kunichiko/RetroCastX/hardware/adc-frontend/parts/TI_PCM1808PWR/TSSOP-14_L5.0-W4.4-H1.0-LS6.4-P0.65.step

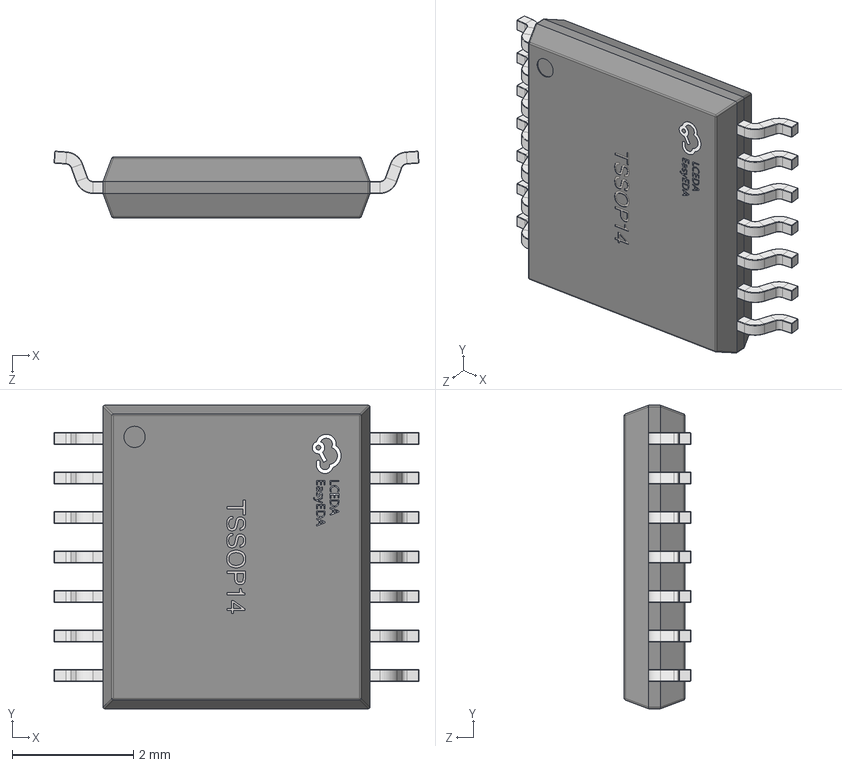
[picture p24: CAD file, 2026-07-28]
hardware/adc-frontend/parts/TI_PCM1808PWR/TSSOP-14_L5.0-W4.4-H1.0-LS6.4-P0.65.step
6.01 x 5.00 x 1.10 mm
