kunichiko/RetroCastX/hardware/adc-frontend/parts/TI_TLV70019DDCR/SOT-23-5_L2.9-W1.6-P0.95-LS2.8-BR.step

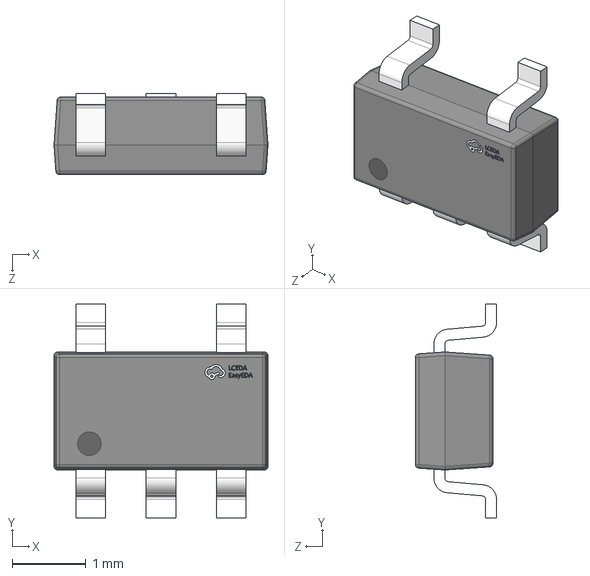
[picture p25: CAD file, 2026-07-28]
hardware/adc-frontend/parts/TI_TLV70019DDCR/SOT-23-5_L2.9-W1.6-P0.95-LS2.8-BR.step
2.90 x 2.90 x 1.10 mm
