kunichiko/RetroCastX/hardware/adc-frontend/parts/TI_TVP7002PZP/HTQFP-100_L14.0-W14.0-H1.20-P0.50-LS16.0-BL-EP6.2.step

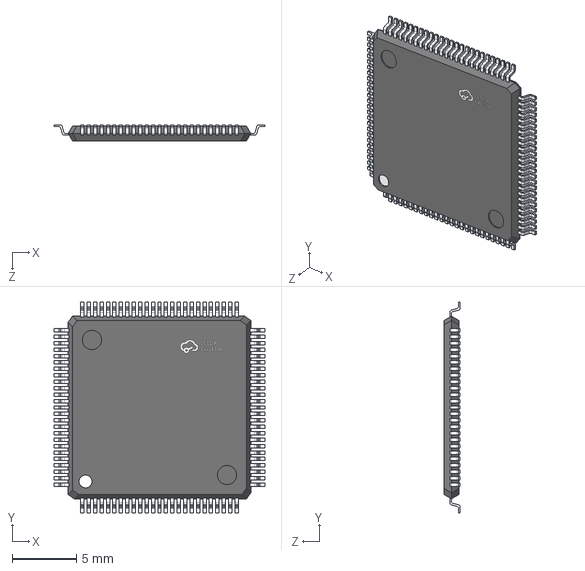
[picture p26: CAD file, 2026-07-28]
hardware/adc-frontend/parts/TI_TVP7002PZP/HTQFP-100_L14.0-W14.0-H1.20-P0.50-LS16.0-BL-EP6.2.step
16.4 x 16.4 x 1.28 mm
