kunichiko/RetroCastX/hardware/adc-frontend/parts/UNI_ROYAL_0402WGF1002TCE/R0402_L1.0-W0.5-H0.4.step

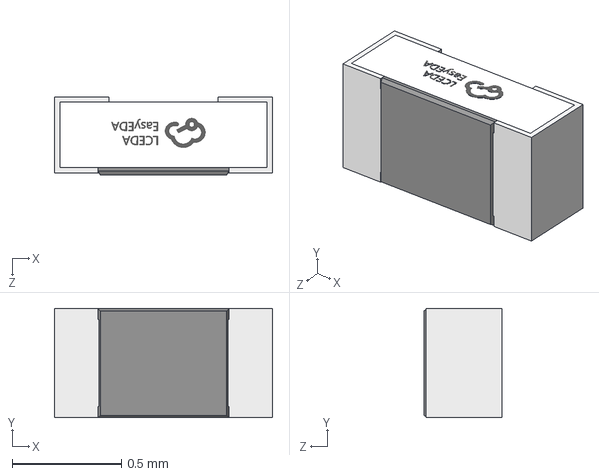
[picture p27: CAD file, 2026-07-28]
hardware/adc-frontend/parts/UNI_ROYAL_0402WGF1002TCE/R0402_L1.0-W0.5-H0.4.step
1.00 x 0.501 x 0.36 mm
