kunichiko/RetroCastX/hardware/adc-frontend/parts/UNKNOWN_PJ_327C_4A/AUDIO-SMD_L11.8-W6.0-H5.0-4P.step

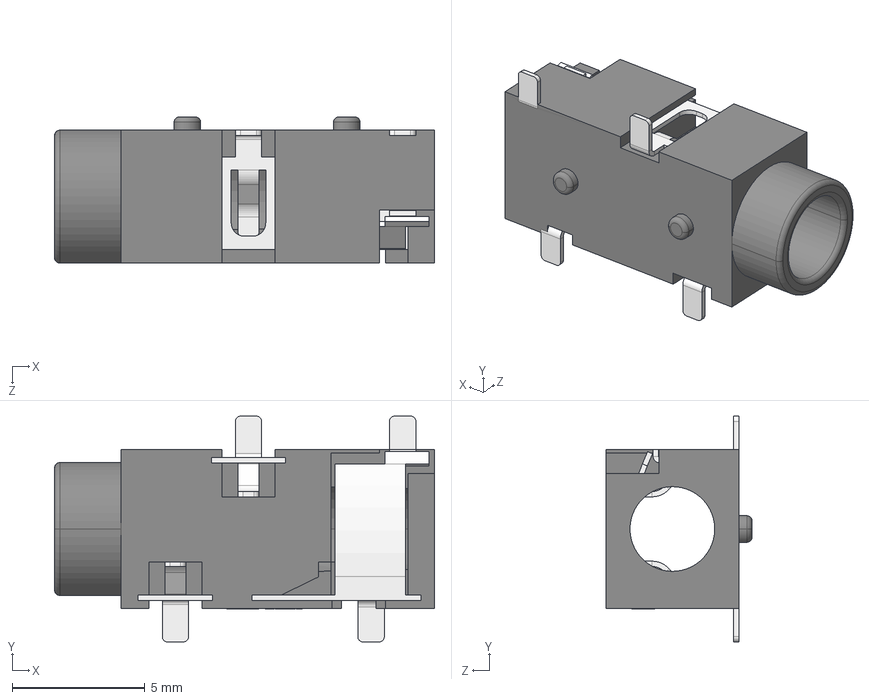
[picture p28: CAD file, 2026-07-28]
hardware/adc-frontend/parts/UNKNOWN_PJ_327C_4A/AUDIO-SMD_L11.8-W6.0-H5.0-4P.step
14.3 x 8.50 x 5.50 mm
