kunichiko/RetroCastX/hardware/adc-frontend/parts/UNKNOWN_TYPE_C_31_M_12/USB-C_SMD-TYPE-C-31-M-12.step

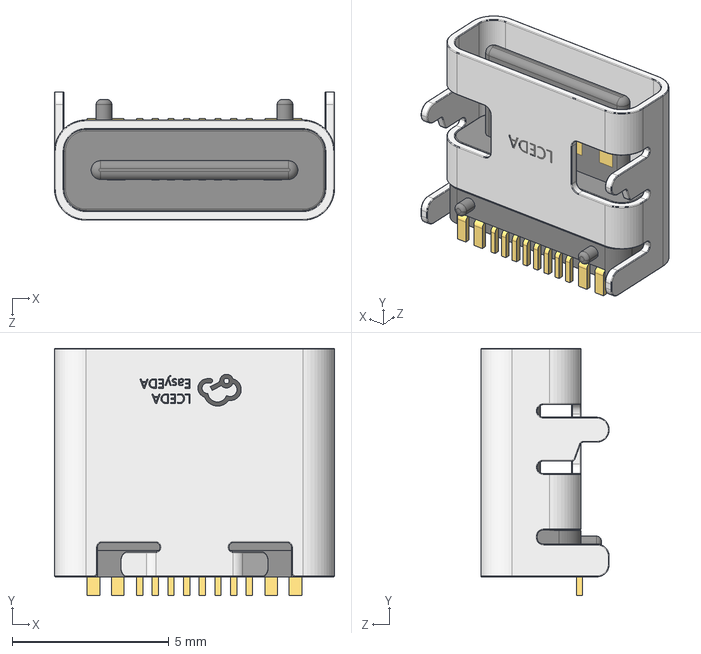
[picture p29: CAD file, 2026-07-28]
hardware/adc-frontend/parts/UNKNOWN_TYPE_C_31_M_12/USB-C_SMD-TYPE-C-31-M-12.step
8.94 x 7.90 x 4.10 mm
