kunichiko/RetroCastX/hardware/adc-frontend/parts/WCH_CH347F/QFN-28_L4.0-W4.0-P0.40-BL-EP2.7.step

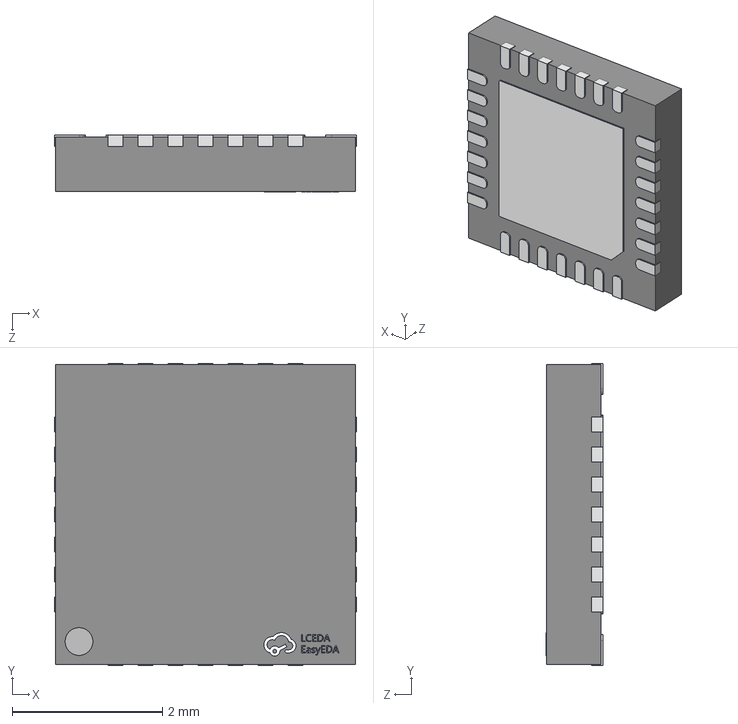
[picture p30: CAD file, 2026-08-18]
hardware/adc-frontend/parts/WCH_CH347F/QFN-28_L4.0-W4.0-P0.40-BL-EP2.7.step
4.02 x 4.02 x 0.76 mm
