kunichiko/RetroCastX/hardware/adc-frontend/parts/Worldsemi_WS2812B_2020/LED-SMD_4P-L2.0-W2.0-H0.8-TL_WS2812B-2020.step

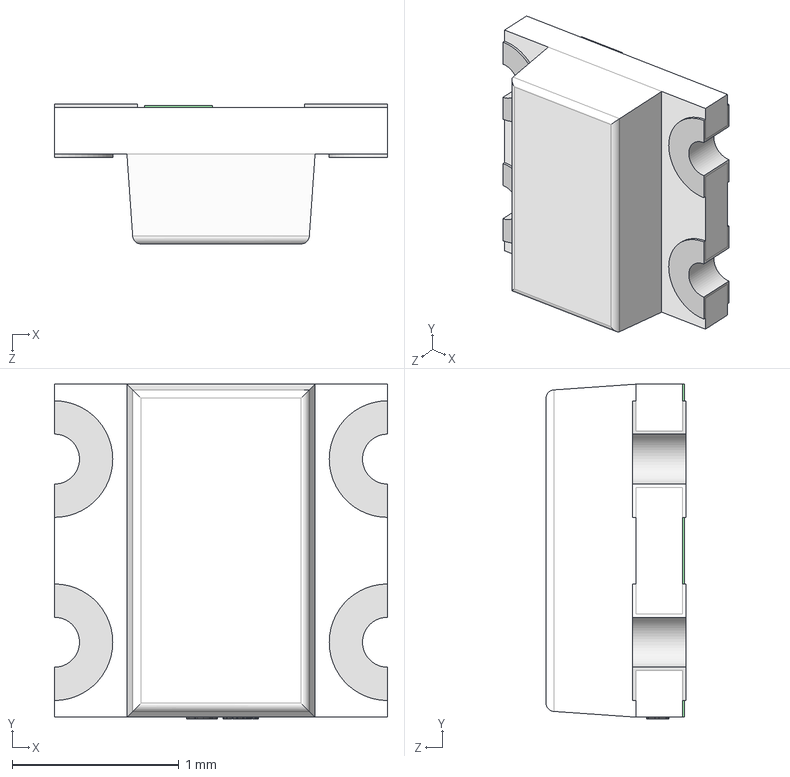
[picture p31: CAD file, 2026-08-12]
hardware/adc-frontend/parts/Worldsemi_WS2812B_2020/LED-SMD_4P-L2.0-W2.0-H0.8-TL_WS2812B-2020.step
2.00 x 2.01 x 0.84 mm
