kunichiko/RetroCastX/hardware/adc-frontend/parts/XFCN_BH254V_10P/IDC-TH_10P-P2.54-V-R2-C5-S2.54.STEP

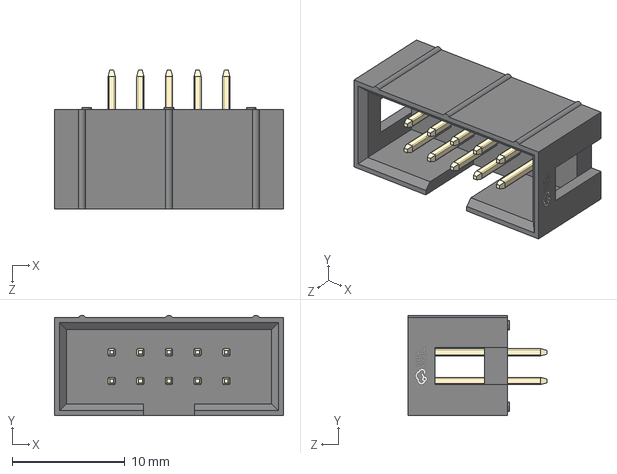
[picture p32: CAD file, 2026-09-25]
hardware/adc-frontend/parts/XFCN_BH254V_10P/IDC-TH_10P-P2.54-V-R2-C5-S2.54.STEP
20.3 x 8.89 x 12.3 mm
