kunichiko/RetroCastX/hardware/adc-frontend/parts/YAGEO_CC1812KKX7RDBB472/C1812_L4.5-W3.2-H2.6.step

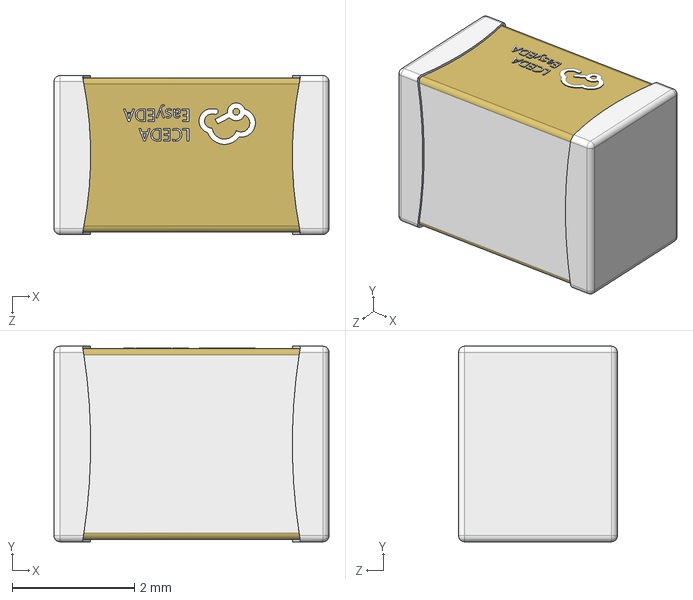
[picture p33: CAD file, 2026-07-28]
hardware/adc-frontend/parts/YAGEO_CC1812KKX7RDBB472/C1812_L4.5-W3.2-H2.6.step
4.50 x 3.20 x 2.60 mm
