kunichiko/RetroCastX/hardware/adc-frontend/parts/YXC_OT322527MJBA4SL/OSC-SMD_4P-L3.2-W2.5-CJ13-320001210A20.step

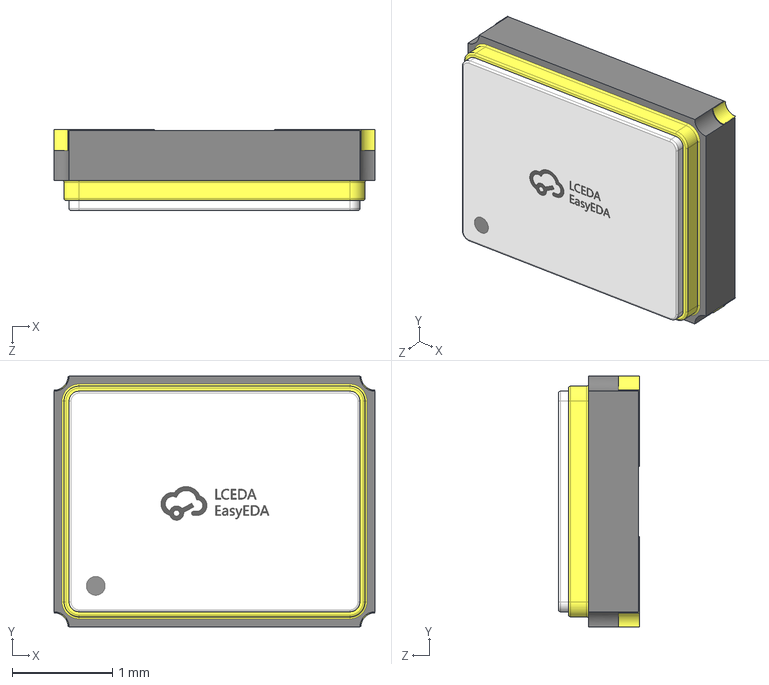
[picture p34: CAD file, 2026-07-28]
hardware/adc-frontend/parts/YXC_OT322527MJBA4SL/OSC-SMD_4P-L3.2-W2.5-CJ13-320001210A20.step
3.20 x 2.50 x 0.811 mm
