kunichiko/RetroCastX/hardware/adc-frontend/parts/YXC_X32258MSB4SI/CRYSTAL-SMD_4P-L3.2-W2.5-BL.step

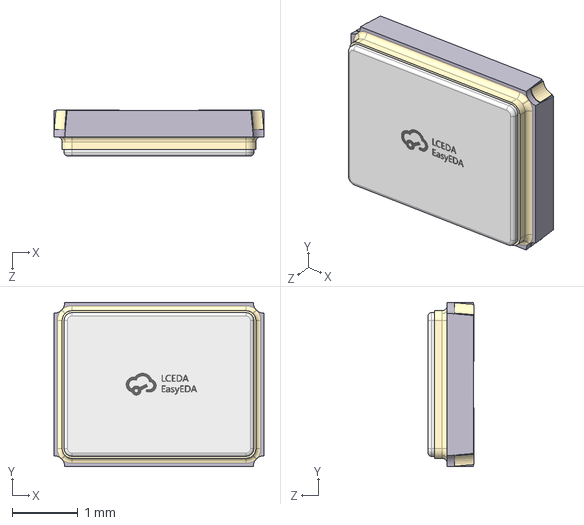
[picture p35: CAD file, 2026-08-03]
hardware/adc-frontend/parts/YXC_X32258MSB4SI/CRYSTAL-SMD_4P-L3.2-W2.5-BL.step
3.20 x 2.50 x 0.701 mm
