kunichiko/RetroCastX/hardware/console-frontend/parts/ROHM_EMZT6_8ET2R/EMT6_L1.6-W1.2-P0.50-LS1.6-BL.step

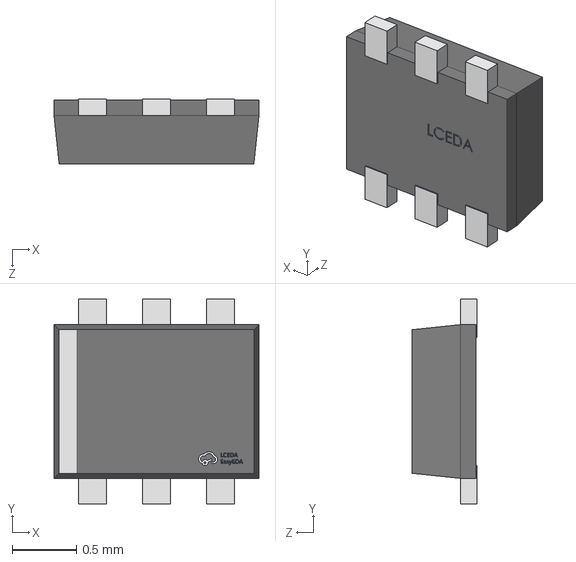
[picture p36: CAD file, 2026-07-28]
hardware/console-frontend/parts/ROHM_EMZT6_8ET2R/EMT6_L1.6-W1.2-P0.50-LS1.6-BL.step
1.60 x 1.60 x 0.511 mm
