kunichiko/RetroCastX/hardware/console-frontend/parts/SAMSUNG_CL21A106KAYNNNE/C0805_L2.0-W1.3-H1.3.step

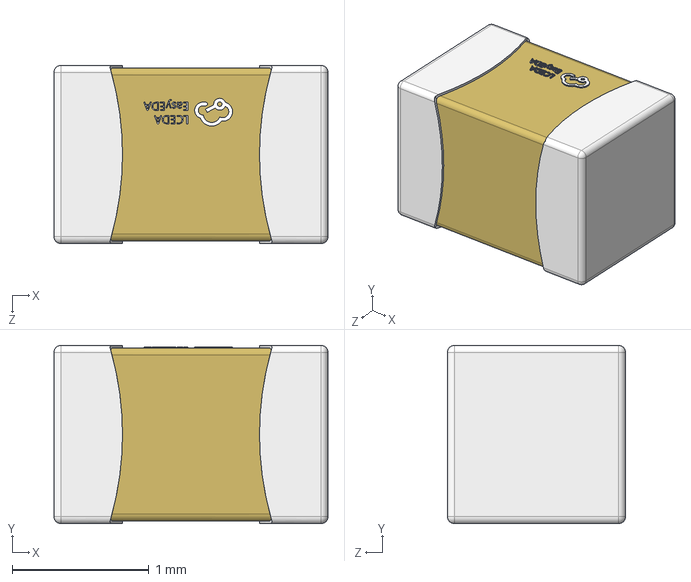
[picture p37: CAD file, 2026-07-28]
hardware/console-frontend/parts/SAMSUNG_CL21A106KAYNNNE/C0805_L2.0-W1.3-H1.3.step
2.00 x 1.30 x 1.30 mm
