kunichiko/RetroCastX/hardware/console-frontend/parts/TI_TS5A23159DGSR/VSSOP-10_L3.0-W3.0-H1.1-LS4.9-P0.50.step

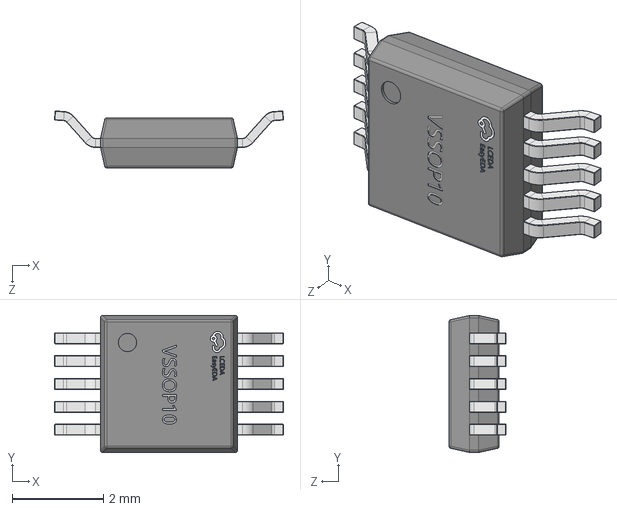
[picture p38: CAD file, 2026-09-25]
hardware/console-frontend/parts/TI_TS5A23159DGSR/VSSOP-10_L3.0-W3.0-H1.1-LS4.9-P0.50.step
5.01 x 3.00 x 1.25 mm
