kunichiko/RetroCastX/hardware/console-frontend/parts/UNI_ROYAL_0603WAF1002T5E/R0603.STEP

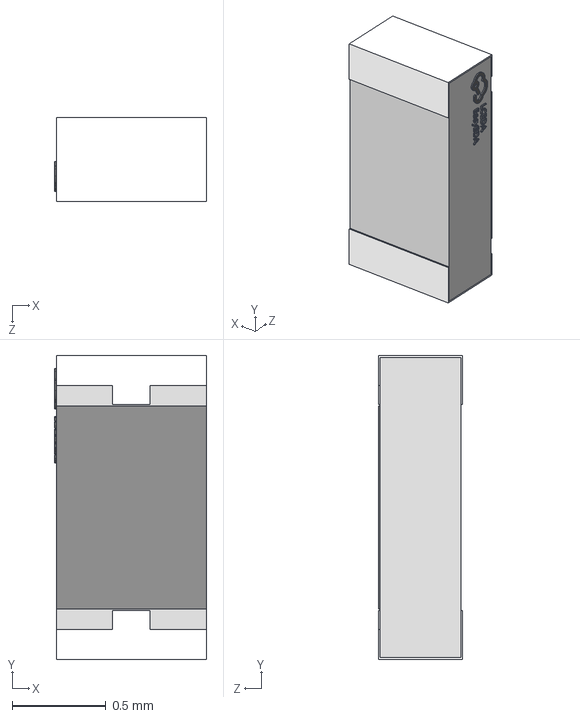
[picture p39: CAD file, 2026-09-25]
hardware/console-frontend/parts/UNI_ROYAL_0603WAF1002T5E/R0603.STEP
0.81 x 1.62 x 0.45 mm
