kunichiko/RetroCastX/hardware/console-frontend/parts/XINGLIGHT_XL_2020RGBC_2812B/6.STEP

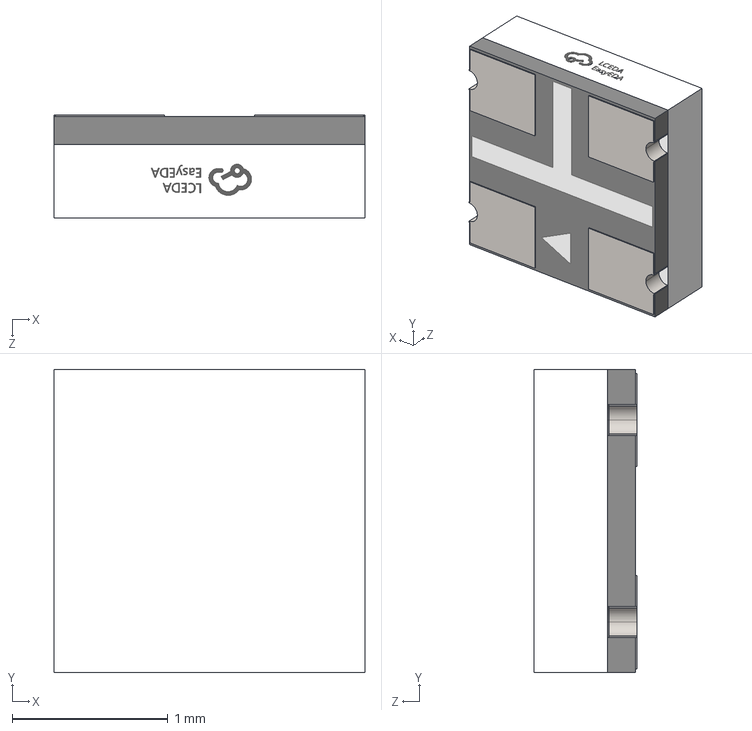
[picture p40: CAD file, 2026-08-19]
hardware/console-frontend/parts/XINGLIGHT_XL_2020RGBC_2812B/6.STEP
2.00 x 1.95 x 0.66 mm
