kunichiko/RetroCastX/hardware/console-frontend/parts/YAGEO_CC0603KRX7R9BB104/C0603_L1.6-W0.8-H0.8.step

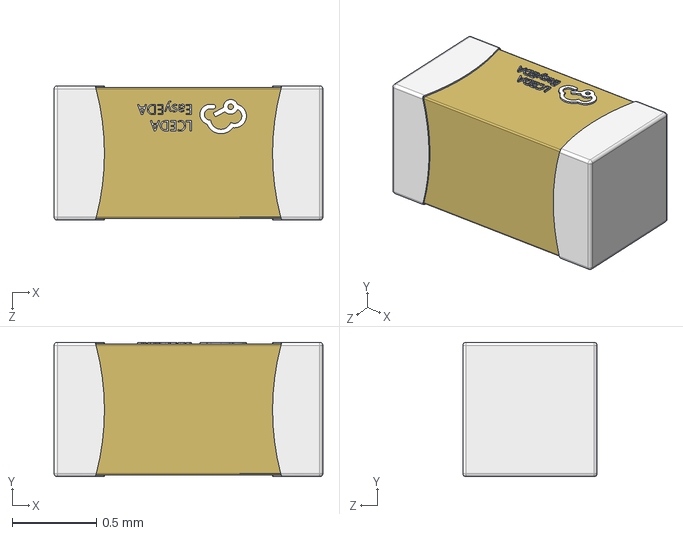
[picture p41: CAD file, 2026-07-28]
hardware/console-frontend/parts/YAGEO_CC0603KRX7R9BB104/C0603_L1.6-W0.8-H0.8.step
1.60 x 0.8 x 0.8 mm
