kunichiko/RetroCastX/client/src/main.rs

//! RetroCastX viewer (scaffold).
//!
//! egui/eframe(wgpuバックエンド)でフレームを表示する。v0.1はegui標準の
//! テクスチャAPIで毎フレーム全面アップロード(512x512なら余裕)。
//! パレット吸着・CRTシェーダ・VRR present制御は、後段でwgpuの
//! paint callback(egui_wgpu::Callback)へ移行して実装する。
//!
//! Usage:
//!   cargo run --release -- [--board IP] [--mac AA:BB:..] [--port 34600] [--no-subscribe]
//!
//! --mimicx-probe は MimicX へのキー転送経路(CoreMIDI)だけを確かめて終了する。
//!
//! --mac は購読対象ボードのMACを指名する(複数ボードLANで必須。省略時は
//! ワイルドカード=全ボード、単一ボードLAN専用)。
//!
//! 既定ではSUBSCRIBEを**各NICのサブネット宛**にブロードキャストし、ボードの
//! ストリームを自分に向ける。限定ブロードキャスト(255.255.255.255)は使わない:
//! あれは既定経路に載るので、VPN接続中は送信自体が失敗する
//! (receiver.rs の broadcast_targets 参照)。sender_sim相手なら --no-subscribe
//! でよい(sender_simはSUBSCRIBEを無視して--dest宛に送るため)。

// Windows: コンソール窓を出さずに起動する。これが無いと、Explorerから起動しても
// 先に真っ黒なコンソールが開いてからUIが出る(通常のGUIアプリの見た目にならない)。
// 代わりにコンソールから起動したときは main の先頭で親のコンソールへ繋ぎ直すので、
// --headless の出力はこれまでどおり見える。
#![windows_subsystem = "windows"]

mod appicon;
mod assembler;
mod awake;
mod audio;
mod bezel;
mod claim;
mod cleanout;
mod fullscreen;
mod keytap;
mod netcheck;
mod ntsc;
mod profiles;
mod remote_input;
mod render;
mod protocol;
mod receiver;
mod settings;
mod theme;
mod toast;

use std::sync::atomic::Ordering;
use std::sync::Arc;

use eframe::egui;

/// コンソールから起動されたときだけ、その親コンソールへ標準出力を戻す。
/// Explorer から起動したときは親が無いので何も起きない(コンソールは出ない)。
/// **最初の出力より前に呼ぶこと** — 標準ハンドルは初回使用時に決まるため。
#[cfg(windows)]
fn attach_parent_console() {
    use windows_sys::Win32::System::Console::{AttachConsole, ATTACH_PARENT_PROCESS};
    unsafe { AttachConsole(ATTACH_PARENT_PROCESS) };
}

#[cfg(not(windows))]
fn attach_parent_console() {}

/// 伝送形式の表示名。数値のままだと 0=888 / 1=555 が直感に反するので名前で出す
fn pixfmt_name(f: u8) -> &'static str {
    match f {
        protocol::PIXFMT_RGB888 => "RGB888 (3B/px)",
        protocol::PIXFMT_RGB555 => "RGB555 (2B/px)",
        protocol::PIXFMT_RGB565 => "RGB565 (2B/px)",
        protocol::PIXFMT_YC8 => "YC8 (2B/px)",
        _ => "unknown",
    }
}

fn main() -> eframe::Result {
    attach_parent_console();
    let mut port = protocol::DEFAULT_PORT;
    let mut subscribe_to = Some("255.255.255.255".to_string());
    let mut headless_secs: Option<u64> = None;
    // --headless のときに完成フレームをPPMへ落とす。絵を目で見られない環境で
    // 「組立・復調までは合っているのか」を切り分けるため
    let mut dump_frame: Option<String> = None;
    // 連続Nフレームを番号付きで落とす(フレーム間で変わる現象の追跡用)
    let mut dump_seq: Option<usize> = None;
    let mut no_vsync = false;
    let mut fullscreen_mode = false;
    let mut rotate: u32 = u32::MAX;   // 未指定なら設定ファイルの値を使う
    let mut target_mac: Option<[u8; 6]> = None;
    let mut decay = 0.8f32;
    // インターレース時の減衰率。既定1.0=減衰しない。
    // インターレースは「毎フレーム半分の行が来ない」のが正常なので、パケットロス用の
    // 減衰をそのまま掛けると面全体がフィールドレートでちらつく。CRTの残光を模すなら
    // 少し減衰させたい人もいるので設定にしてある。
    let mut interlace_decay = 1.0f32;
    // ★**ウィンドウ番号はアプリが配る。** 1プロセスで複数のウィンドウを開く
    //   ので、プロセスごとにロックを取る必要はもう無い。0番が主ウィンドウ。
    let slot_id: u32 = 0;

    // 保存済み設定を読み、CLI引数があればそれで上書きする(その回だけ有効)
    let mut cfg = settings::Settings::load_slot(slot_id);
    eprintln!("settings: {}", settings::Settings::path_for_slot(slot_id).display());
    let mut audio = receiver::AudioOpts::default();
    audio.source = cfg.audio_source;
    // 起動時から設定のデバイスで開く(既定デバイスで鳴り始めるのを防ぐ)
    audio.device = cfg.audio_device.clone();
    let mut bind = String::from("0.0.0.0");
    let mut args = std::env::args().skip(1);
    while let Some(a) = args.next() {
        match a.as_str() {
            "--board" => subscribe_to = Some(args.next().expect("--board needs an IP")),
            "--mac" => target_mac = Some(parse_mac(&args.next().expect("--mac needs AA:BB:.."))),
            "--port" => port = args.next().expect("--port needs a value").parse().unwrap(),
            "--no-subscribe" => subscribe_to = None,
            // 受信/送信ソケットを1つのNICに縛る。**VPN下でも通常は不要**
            // (宛先がNICごとのサブネット宛なので既定経路を参照しない。
            //  receiver.rs の broadcast_targets 参照)。NICを1つに絞りたいときだけ。
            "--bind" => bind = args.next().expect("--bind needs an IP (e.g. 192.168.11.24)"),
            // ドット復元(1タップ逆フィルタ)の係数 a を 0.0..0.9 で指定。
            // 0 で無効。設定ファイルの値を一時的に上書きする(A/B検証用)。
            "--dot-restore" => {
                let a: f32 = args.next().expect("--dot-restore needs a (e.g. 0.36)")
                    .parse().expect("--dot-restore は 0.0〜0.9 の数値");
                cfg.dot_a_milli = (a.clamp(0.0, 0.9) * 1000.0).round() as u32;
            }
            "--dump-seq" => {
                dump_seq = Some(args.next().expect("--dump-seq needs a count")
                                .parse().unwrap())
            }
            "--dump-frame" => {
                dump_frame = Some(args.next().expect("--dump-frame needs a path"))
            }
            "--headless" => {
                headless_secs = Some(args.next().expect("--headless needs seconds").parse().unwrap())
            }
            // VRR実験用: presentをvsyncから切り離す(wgpu AutoNoVsync)。
            // VRR対応パネルなら「フレームが来たときに出す」に近づく第一歩
            "--no-vsync" => no_vsync = true,
            // 低遅延フルスクリーン(専用presentスレッド+Immediate、ソース駆動present)
            "--fullscreen" => fullscreen_mode = true,
            // 画面回転(縦画面のゲーム用)。0/90/180/270 度、時計回り
            "--rotate" => {
                let v: u32 = args.next().expect("--rotate needs 0|90|180|270").parse().unwrap();
                rotate = match v {
                    0 => 0, 90 => 1, 180 => 2, 270 => 3,
                    _ => panic!("--rotate は 0/90/180/270 のいずれか"),
                };
            }
            // 欠損ライン減衰率(1.0=前フレーム保持のまま, 0.8=毎フレーム80%へ暗転して消える)
            "--interlace-decay" => {
                interlace_decay = args.next()
                    .expect("--interlace-decay needs a value (e.g. 1.0)").parse().unwrap()
            }
            "--decay" => {
                decay = args.next().expect("--decay needs a value (e.g. 0.8)").parse().unwrap()
            }
            // 音声: 再生するsource(0=RGB端子音声, 1=LINE入力, 2=S/PDIF)
            "--audio" => {
                audio.source =
                    Some(args.next().expect("--audio needs 0|1|2").parse().unwrap());
                cfg.audio_source = audio.source;
            }
            // MimicX への経路だけを確かめて終了する(GUIは起動しない)。
            // 「キーが効かない」ときに、宛先が無いのか送れているのかを切り分ける
            "--mimicx-probe" => std::process::exit(!remote_input::probe() as i32),
            // 受け取った物理キーを stderr へ出す。「そのキーがアプリに届いて
            // いないのか、届いているが転送していないのか」の切り分け用
            // NIC受信バッファーの確認だけして終了する(GUIは起動しない)。
            // 実機での切り分け用。IPはボードのアドレス(経路の判定に使う)
            "--netcheck" => {
                let ip = args.next().expect("--netcheck needs the board IP");
                let b = netcheck::probe(&ip);
                println!("board {ip} への経路の NIC: {b:?}");
                match &b {
                    netcheck::Buffers::Known { adapter, value } => {
                        println!("  アダプタ      : {adapter}");
                        println!("  ReceiveBuffers: {value} (推奨 {})", netcheck::RECOMMENDED);
                        if b.should_warn() {
                            println!("  → 小さすぎます:");
                            println!("     {}", netcheck::fix_command(Some(adapter)));
                        } else {
                            println!("  → 足りています");
                        }
                    }
                    netcheck::Buffers::Unsupported => {
                        println!("  このドライバは *ReceiveBuffers を公開していません(判定不能)");
                    }
                    netcheck::Buffers::Unknown => {
                        println!("  調べられませんでした(経路が引けない/レジストリが読めない)");
                    }
                }
                std::process::exit(0);
            }
            "--log-keys" => {
                remote_input::LOG_KEYS.store(true, Ordering::Relaxed);
            }
            "--no-audio" => {
                audio.source = None;
                cfg.audio_source = None;
            }
            // 音量[%]。保存値より優先(その回だけ)
            "--volume" => {
                let pct: f32 = args.next().expect("--volume needs 0..150").parse().unwrap();
                cfg.volume = (pct / 100.0).clamp(0.0, 1.5);
            }
            // 音声バッファ[ms]。小さいほど低遅延だが枯渇(音切れ)しやすい
            "--audio-buffer" => {
                audio.prebuffer_ms =
                    args.next().expect("--audio-buffer needs ms").parse().unwrap();
                audio.max_ms = audio.prebuffer_ms * 3;
            }
            other => {
                eprintln!("unknown arg: {other}");
                std::process::exit(2);
            }
        }
    }

    if let Some(secs) = headless_secs {
        return run_headless(port, bind, subscribe_to, target_mac, secs, decay, interlace_decay,
                            audio, dump_frame, dump_seq, cfg.dot_a_milli);
    }
    if fullscreen_mode {
        let rot = if rotate == u32::MAX { cfg.rotate } else { rotate };
        let p = render::Params {
            rotate: rot,
            tube: cfg.tube_aspect,
            filter: cfg.filter,
            window: cfg.window,
            time_based: cfg.tube_time_based,
            h_size: 1.0, h_pos: 0.0, v_size: 1.0, v_pos: 0.0,
            ..Default::default()
        };
        fullscreen::run(port, bind, subscribe_to, target_mac, decay, interlace_decay, audio, p); // 戻らない
    }

    let mut wgpu_options = eframe::egui_wgpu::WgpuConfiguration::default();
    if no_vsync {
        wgpu_options.surface.present_mode = eframe::wgpu::PresentMode::AutoNoVsync;
        wgpu_options.surface.desired_maximum_frame_latency = Some(1); // 低遅延優先
    }

    let options = eframe::NativeOptions {
        viewport: {
            // アイコンは実行時に設定しないとタスクバー/タイトルバーに出ない
            // (exeへの埋め込みはExplorerのファイル用。appicon.rs 参照)
            let mut vp = egui::ViewportBuilder::default()
                .with_inner_size([cfg.window_w, cfg.window_h])
                .with_title(if slot_id == 0 {
                    "RetroCast X".to_string()
                } else {
                    // ★**番号を出す。** 3つ並べたときに、どのウィンドウの設定を
                    //   触っているのか分からなくなる
                    format!("RetroCast X #{}", slot_id)
                });
            // ★**位置も戻す。** 大きさだけでは並びが戻らない(3画面筐体では
            //   横に並べた配置そのものが設定)。
            if let (Some(x), Some(y)) = (cfg.window_x, cfg.window_y) {
                vp = vp.with_position([x, y]);
            }
            if let Some(icon) = appicon::egui_icon() {
                vp = vp.with_icon(icon);
            }
            vp
        },
        wgpu_options,
        ..Default::default()
    };
    eframe::run_native(
        "RetroCast X",
        options,
        Box::new(move |cc| {
            // アイコン由来の配色を先に当てる(ウィジェットが作られる前)
            theme::apply(&cc.egui_ctx);
            install_cjk_font(&cc.egui_ctx);
            // ★**映像テクスチャの置き場はアプリに1つ。** セッションごとに
            //   insert すると型で索く辞書なので上書きになり、**先に開いた
            //   ウィンドウの映像が消える**。中身はウィンドウ番号で分ける。
            if let Some(rs) = cc.wgpu_render_state.as_ref() {
                // 描画先の色空間を出す。映像テクスチャはこれに合わせて選ぶ
                // (render::video_tex_format が sRGB 性を揃える)。
                eprintln!("render target format: {:?}", rs.target_format);
                rs.renderer
                    .write()
                    .callback_resources
                    .insert(render::Blits::default());
            }
            let mut app = App {
                sessions: vec![Session::new(
                    slot_id, &cc.egui_ctx, cc.wgpu_render_state.clone(), port,
                    subscribe_to, target_mac, bind.clone(), no_vsync,
                    decay, interlace_decay, audio, cfg.clone(),
                )],
                port,
                bind: bind.clone(),
                no_vsync,
                decay,
                interlace_decay,
                awake: awake::KeepAwake::new(),
            };
            app.restore_windows(&cc.egui_ctx, cc.wgpu_render_state.clone());
            Ok(Box::new(app))
        }),
    )
}


/// CJKを含むシステムフォントをeguiへ追加する。
/// 出力デバイス名はOS由来で日本語を含むことがあり、egui既定フォントにはCJKの
/// グリフが無いため豆腐(□)になる。フォントは同梱せず、実行環境のものを使う。
fn install_cjk_font(ctx: &egui::Context) {
    // 単一フォント(.ttf/.otf)のみ。.ttc はコレクションでab_glyphが扱えない
    const CANDIDATES: &[&str] = &[
        // macOS
        "/System/Library/Fonts/Supplemental/Arial Unicode.ttf",
        "/Library/Fonts/Arial Unicode.ttf",
        // Linux (Noto/VLGothic)
        "/usr/share/fonts/opentype/noto/NotoSansCJK-Regular.ttc",
        "/usr/share/fonts/truetype/noto/NotoSansCJK-Regular.ttf",
        "/usr/share/fonts/truetype/vlgothic/VL-Gothic-Regular.ttf",
        // Windows
        "C:/Windows/Fonts/meiryo.ttc",
        "C:/Windows/Fonts/msgothic.ttc",
        "C:/Windows/Fonts/YuGothR.ttc",
    ];
    for path in CANDIDATES {
        let Ok(bytes) = std::fs::read(path) else { continue };
        let mut fonts = egui::FontDefinitions::default();
        fonts.font_data.insert(
            "cjk".to_owned(),
            std::sync::Arc::new(egui::FontData::from_owned(bytes)),
        );
        // 既定フォントの後ろに足す(ASCIIは既定の見た目を保ち、CJKだけ補完)
        for family in [egui::FontFamily::Proportional, egui::FontFamily::Monospace] {
            fonts.families.entry(family).or_default().push("cjk".to_owned());
        }
        ctx.set_fonts(fonts);
        return;
    }
    eprintln!("font: CJK対応フォントが見つからないため日本語が豆腐になります");
}

/// "AA:BB:CC:DD:EE:FF" → [u8; 6](区切りは ':' or '-')。
fn parse_mac(s: &str) -> [u8; 6] {
    let parts: Vec<&str> = s.split([':', '-']).collect();
    assert_eq!(parts.len(), 6, "MAC must have 6 octets: {s}");
    let mut mac = [0u8; 6];
    for (i, p) in parts.iter().enumerate() {
        mac[i] = u8::from_str_radix(p, 16).expect("bad MAC octet");
    }
    mac
}

/// GUIなしで受信パイプラインだけ動かし、毎秒統計を出力する(検証・CI用)。
fn run_headless(
    port: u16,
    bind: String,
    subscribe_to: Option<String>,
    target_mac: Option<[u8; 6]>,
    secs: u64,
    decay: f32,
    interlace_decay: f32,
    audio: receiver::AudioOpts,
    dump_frame: Option<String>,
    dump_seq: Option<usize>,
    dot_a_milli: u32,
) -> eframe::Result {
    let shared = Arc::new(receiver::Shared::default());
    shared.dot_a_milli.store(dot_a_milli, std::sync::atomic::Ordering::Relaxed);
    receiver::spawn(
        receiver::Config { port, bind: bind.clone(), subscribe_to, target_mac, decay, interlace_decay, audio },
        shared.clone(),
        || {},
    )
    .expect("UDP bind failed");
    for _ in 0..secs {
        std::thread::sleep(std::time::Duration::from_secs(1));
        let s = shared.stats.lock().unwrap().clone();
        let mode = shared.mode.lock().unwrap().clone();
        let dims = mode
            .map(|m| format!("{}x{}", m.hactive, m.vactive))
            .unwrap_or_else(|| "no mode".into());
        println!(
            "{dims}  {:.1} fps  {:.1} Mbps  frames={} pkts={} lost={} qdrop={} orphan={}",
            s.fps, s.mbps, s.frames, s.packets, s.lost_packets, s.queue_drops,
            s.orphan_lines
        );
        // 音声。**枯渇の切り分け表示を GUI を開かずに読めるように。**
        if let Some(a) = shared.audio.lock().unwrap().clone() {
            let ms = |us: u64| us as f64 / 1000.0;
            let rate = a.device_rate.load(Ordering::Relaxed).max(1);
            let last = a.last_underrun_us.load(Ordering::Relaxed);
            println!(
                "   audio: buffered {} ms  pkts {}  underruns {}  gap max {:.1} ms  cb max {} f{}",
                a.buffered.load(Ordering::Relaxed) * 1000 / rate,
                a.packets.load(Ordering::Relaxed),
                a.underruns.load(Ordering::Relaxed),
                ms(a.arrival_gap_max_us.load(Ordering::Relaxed)),
                a.cb_frames_max.load(Ordering::Relaxed),
                if last > 0 {
                    format!("  last {:.0}s前 無着 {:.0} ms",
                            ms(a.now_us() - last) / 1000.0,
                            ms(a.last_underrun_gap_us.load(Ordering::Relaxed)))
                } else { String::new() });
        }
        // 連続フレームを番号付きで落とす。**フレームごとに入れ替わる縞**のような
        // 「1枚では分からない」現象を追うのに要る(実際に必要になった)。
        if let (Some(path), Some(n)) = (dump_frame.as_ref(), dump_seq) {
            let mut last = 0u64;
            let mut got = 0usize;
            let t0 = std::time::Instant::now();
            while got < n && t0.elapsed() < std::time::Duration::from_secs(10) {
                let g = shared.frame_gen.load(Ordering::Acquire);
                if g == last {
                    std::thread::sleep(std::time::Duration::from_micros(500));
                    continue;
                }
                last = g;
                if let Some(f) = shared.frame.lock().unwrap().as_ref() {
                    let mut out = format!("P6\n{} {}\n255\n", f.width, f.height)
                        .into_bytes();
                    for px in f.rgba.chunks_exact(4) {
                        out.extend_from_slice(&px[..3]);
                    }
                    let _ = std::fs::write(format!("{path}.{got:04}.ppm"), &out);
                    got += 1;
                }
            }
            println!("   dump: {path}.0000..{:04}.ppm ({}枚)", got.saturating_sub(1), got);
            return Ok(());
        }
        // 完成フレームをそのままPPMへ落とす。**GUIを開かずに絵を確かめる唯一の手段。**
        // 「絵が出ない」を追うとき、組立・復調までは正しいのか、描画側なのかを
        // ここで切り分けられる(実際にこれで切り分けた)。
        if let Some(path) = dump_frame.as_ref() {
            if let Some(f) = shared.frame.lock().unwrap().as_ref() {
                let mut out = format!("P6\n{} {}\n255\n", f.width, f.height).into_bytes();
                for px in f.rgba.chunks_exact(4) {
                    out.extend_from_slice(&px[..3]);
                }
                if std::fs::write(path, &out).is_ok() {
                    let n = f.rgba.chunks_exact(4).filter(|p| p[0] | p[1] | p[2] != 0).count();
                    println!("   dump: {path} ({}x{}) 非黒画素 {}/{} = {:.1}%",
                             f.width, f.height, n, f.width * f.height,
                             n as f32 * 100.0 / (f.width * f.height) as f32);
                }
            }
        }
        // NTSC復調の状態。**GUIを開かずに確認できるようにしておく。**
        // この環境は画面収録の権限が無く、絵で確かめられないので数値で出す
        if s.ntsc_comb_step > 0 {
            println!("   NTSC復調: {}行ロック  コム間隔{}  位相差{:.0}°(180°が正常)",
                     s.ntsc_locked, s.ntsc_comb_step, s.ntsc_phase_deg);
            if s.ntsc_svideo {
                println!("   S端子(赤chのバーストで判定): コムは使わない/輝度は素通し");
            } else {
                println!("   3次元コム: {}行  動きと判定 {:.1}%  1フレーム前との位相ズレ {:.1}°  \
                          TBC {:.3}サンプル",
                         s.ntsc_lines_3d, 100.0 * s.ntsc_motion_frac,
                         s.ntsc_phase_drift_deg, s.ntsc_tbc_rms);
            }
        } else if s.ntsc_mono {
            println!("   NTSC: 白黒(バーストなし) 黒レベルのみ校正");
        }
        // 生産側がUIを待った時間。**GUIのときだけパケットが落ちる**を切り分ける
        if s.publish_wait_max_ms > 0.05 {
            println!("   フレーム差し替えのUI待ち: 合計{:.1}ms 最大{:.1}ms /区間",
                     s.publish_wait_ms, s.publish_wait_max_ms);
        }
        println!("   インタレース判定(測定): {}  未充填の行 {}",
                 if s.interlace_measured { "1フィールドずつ来ている(太らせ停止・減衰なし)" }
                 else { "プログレッシブ扱い(太らせ有効)" },
                 s.unfilled_rows);
        // 何も来ないときに、どの種別が届いていないかを出す。
        // ブロードキャストだけ届いてユニキャストが届かない、などが分かる
        if s.frames == 0 {
            let k: Vec<String> = ["LINE", "AUDIO", "MODE", "INFO", "CONFIG", "other"]
                .iter()
                .zip(shared.kind_counts.iter())
                .map(|(n, c)| format!("{n}={}", c.load(Ordering::Relaxed)))
                .collect();
            println!("   受信種別: {}", k.join(" "));
        }
    }
    let s = shared.stats.lock().unwrap().clone();
    shared.stop.store(true, Ordering::Relaxed);
    if s.frames == 0 {
        eprintln!("FAIL: no frames received");
        std::process::exit(1);
    }
    println!("OK: {} frames, {} lost packets", s.frames, s.lost_packets);
    Ok(())
}

/// **新しいフレームが画面に出る間隔**の計測(vsync量子化の検出用)。
///
/// ★**描画にかかった時間ではない。** `refresh_texture` は新フレームが無ければ
///   即 return するので、ここに来るのは「中身が変わったpaint」だけ。だから
///   ボードが59.8fps送っているのにここが54.9Hzなら、**8%のフレームが表示されずに
///   置き換わっている**という意味になる。以前は "paint" と表示していて
///   「描画に18msかかっている」と読めてしまった。
///
/// present完了時刻そのものはwgpu経由では取れないため、この間隔を代理指標にする
/// (FIFOではスワップチェーンのバックプレッシャでvsync周期に量子化される)。
/// CPU側で実際にかかった時間は `cpu_summary` に別に出す。
struct PaceMeter {
    last_paint: Option<std::time::Instant>,
    intervals_ms: std::collections::VecDeque<f32>,
    last_log: std::time::Instant,
    summary: String,
    /// ★**間隔と処理時間は別物。** 上の intervals_ms は「新フレームが画面に出る
    ///   間隔」で、FIFOのvsync待ちを含む。こちらはCPU側で実際にかかった時間で、
    ///   間隔が伸びたときに「我々が遅いのか、待たされているのか」を分ける。
    ui_ms: std::collections::VecDeque<f32>,
    upload_ms: std::collections::VecDeque<f32>,
    cpu_summary: String,
    /// ★**描画そのものの回数。** 新フレームの有無に関わらず数える。
    ///   これが60Hz出ているのに新フレーム間隔が54Hzなら「描画は回っているが
    ///   フレームが置き換わっている」、こちらも54Hzなら「描画が回っていない」。
    ui_calls: u32,
    ui_rate_hz: f32,
    ui_since: std::time::Instant,
    /// 表示できた新フレームのレート[Hz]。受信レートと並べて出す
    pub new_frame_hz: f32,
}

impl PaceMeter {
    fn new() -> Self {
        Self {
            last_paint: None,
            intervals_ms: std::collections::VecDeque::with_capacity(256),
            last_log: std::time::Instant::now(),
            summary: String::new(),
            ui_ms: std::collections::VecDeque::with_capacity(256),
            upload_ms: std::collections::VecDeque::with_capacity(256),
            cpu_summary: String::new(),
            ui_calls: 0,
            ui_rate_hz: 0.0,
            ui_since: std::time::Instant::now(),
            new_frame_hz: 0.0,
        }
    }

    fn note_upload(&mut self, d: std::time::Duration) {
        if self.upload_ms.len() >= 256 { self.upload_ms.pop_front(); }
        self.upload_ms.push_back(d.as_secs_f32() * 1000.0);
    }

    fn note_ui(&mut self, d: std::time::Duration) {
        if self.ui_ms.len() >= 256 { self.ui_ms.pop_front(); }
        self.ui_ms.push_back(d.as_secs_f32() * 1000.0);
        self.ui_calls += 1;
        let el = self.ui_since.elapsed().as_secs_f32();
        if el >= 1.0 {
            self.ui_rate_hz = self.ui_calls as f32 / el;
            self.ui_calls = 0;
            self.ui_since = std::time::Instant::now();
        }
        let f = |v: &std::collections::VecDeque<f32>| -> (f32, f32) {
            if v.is_empty() { return (0.0, 0.0); }
            let n = v.len() as f32;
            let mean = v.iter().sum::<f32>() / n;
            let max = v.iter().cloned().fold(0.0f32, f32::max);
            (mean, max)
        };
        let (um, ux) = f(&self.ui_ms);
        let (tm, tx) = f(&self.upload_ms);
        self.cpu_summary = format!(
            "描画 {:.1}Hz / CPU: UI {um:.2}ms(最大{ux:.2}) 転送 {tm:.2}ms(最大{tx:.2})",
            self.ui_rate_hz);
    }

    /// 新フレームを受け取った(= 中身が変わるpaint)
    fn on_new_frame(&mut self) {
        let now = std::time::Instant::now();
        if let Some(prev) = self.last_paint {
            let ms = prev.elapsed().as_secs_f32() * 1000.0;
            if self.intervals_ms.len() >= 256 {
                self.intervals_ms.pop_front();
            }
            self.intervals_ms.push_back(ms);
        }
        self.last_paint = Some(now);
        if self.last_log.elapsed().as_secs_f32() >= 1.0 && !self.intervals_ms.is_empty() {
            let n = self.intervals_ms.len() as f32;
            let mean = self.intervals_ms.iter().sum::<f32>() / n;
            let var = self.intervals_ms.iter().map(|x| (x - mean) * (x - mean)).sum::<f32>() / n;
            self.new_frame_hz = 1000.0 / mean;
            self.summary = format!(
                "新フレーム間隔 {:.2}ms σ{:.2} → {:.2}Hz",
                mean,
                var.sqrt(),
                self.new_frame_hz
            );
            // ★CPU側の内訳も一緒に出す。パネルはマウスを止めないと読めないので、
            //   「マウスを動かしている最中」の数字はログでしか取れない
            //   (実機で「ウィンドウ上でマウスを動かすとレートが下がる」を追うのに要った)
            eprintln!("pace: {} | {}", self.summary, self.cpu_summary);
            self.last_log = std::time::Instant::now();
        }
    }
}

/// 実測タイミングから「まともな映像が来ているか」を判定する。
/// 無信号だとTVPのH-PLLがロックを失い、DATACLKが低速で自走してADCが浮いた入力の
/// ノイズを拾うため、砂嵐が表示される。実測値が現実的な範囲を外れたら無信号とみなす。
fn signal_is_valid(m: &protocol::Mode) -> bool {
    let fh_hz = m.hfreq_mhz_x1000 as f64 / 1000.0;
    // 15kHz系(≒15.98k)〜31kHz系(≒31.5k)を含む余裕のある範囲
    (12_000.0..80_000.0).contains(&fh_hz)
        && (100..1500).contains(&m.vtotal)
        && m.dotclk_hz > 5_000_000
}

/// pll_divide と位相を自動で決める処理の進行状態。
///
/// 原理は host/python/retrocastx/pll_tune.py の autotune と同じ。要点だけ:
/// 「近傍で鋭さが最大の点」を探す方法は有理倍に騙される(1.5倍は位相ロックする
/// 有理比なので本物の局所ピークに見える)。そこで、まず上限まで意図的に過剰
/// サンプルしてスペクトル占有率から倍率を割り出し、そこから8の倍数で±7%だけ
/// 局所探索して詰める。最後に位相を振る。
///
/// ## 簡易(Quick)とフル(Full)
///
/// 上のフルスキャンは**探索範囲が広すぎる**。プロファイルを選んでいるなら
/// pll_divide は「水晶÷分周 ÷ fH が整数」を満たす数点しか取り得ないので、
/// その数点だけを見ればよい(例: X68000の31.5kHzなら htotal 1104/736/552/368)。
///
/// **機種固有の分岐は一切書かない。** 候補は `profiles::scan_candidates` が
/// プロファイルの水晶/分周表と fH から作るので、機種を足すときは
/// `profiles.rs` の表を書けばここは触らなくてよい。
///
/// ### 何で1:1を判定するか — 位相感度
///
/// 使うのは**位相感度**。1ドット=1サンプルなら、位相を半ドット動かせば全サンプルが
/// ドットの中央から境目へ移るので鮮鋭度が大きく落ちる。過剰サンプルだと、位相を
/// 動かしても「一部のサンプルが境目に来る」状態が入れ替わるだけなので変化が小さい。
/// **同じ pll_divide での比**なので、絵の内容にも入力の帯域にも依存しない。
///
/// ★**スペクトル占有率で1:1を判定してはいけない。** 一度これで実装して外した。
///   占有率は「1:1ならスペクトルがNyquistまで埋まる」を前提にするが、入力の
///   アナログ帯域がドットレートに対して足りていない機種ではその前提が崩れる。
///   X68000の768x512(34.776MHz)がまさにそれで、1ドットが白の64%までしか
///   立たない。正解の1104で測っても占有率は0.7程度しか出ないので、
///   `1104 × 0.7 = 773` から「736だ」と誤って1段降りた(実機で発生)。
///   1.0倍と1.5倍を占有率で見分けるのは、この機種では原理的に無理。
///
///   占有率にも使い道はあって、`est = 設定値 × 占有率 = 真のhtotal × 帯域率`
///   なので **真の htotal の下限**になる(帯域率 ≤ 1 だから)。下限としてなら
///   信用できるので、枝刈りと最後のフォールバックにだけ使う。
///
/// ### 選び方
///
/// **全候補の位相感度を測ってから、いちばん感度が強い(最悪÷最良がいちばん小さい)
/// 点を採る。** どれもしきい値を下回らなければ判別できていないので、いちばん
/// 大きい候補に倒す。大きい側は整数倍の過剰サンプルで眠くなるだけだが、小さい側は
/// ドットを飛ばして絵が壊れる。非対称なので迷ったら上。この経路に来るのはたいてい、
/// そのモードが1:1にできない(TVPの下限12MHzで整数倍を強いられている)場合。
///
/// ★**「感度が立った最初の候補で止まり、降りる先を占有率で枝刈りする」形は
///   実機で外した**(2026-09-04、31.5kHz の 512x512 で 1104 のまま動かなかった。
///   降下が一度も起きていなかった)。枝刈りの根拠は「est = 設定値 × 占有率 は
///   真の htotal の下限」だったが成り立っていなかった。真値 736 を 1104 で測った
///   ときの占有率の理論上の上限は 736/1104 = 0.667 なのに実測は 0.716 出た
///   (99%エネルギーの裾がノイズを拾う)。下限として使えない量で枝刈りしていた
///   ので、正解が候補から消えていた。
///
///   判定材料の側は十分な差が出ていた。実測(31.5kHz 512x512、真値736):
///
/// ```text
///     pll 1104  最良 160.25  最悪 156.58  → 98%   1.5倍オーバーサンプル
///     pll  736  最良 377.11  最悪 200.92  → 53%   ★1:1
///     pll  552  最良 406.15  最悪 351.23  → 87%
/// ```
///
///   **鮮鋭度の絶対値では選べない**ことにも注意(552 の最良 406 は 736 の 377 より
///   大きい)。見るのは同じ設定内での比。`quick_pick` の試験でこの値を固定してある。
///
/// ### 結果には内訳を出す
///
/// 「pll_div 1104 / 位相 0 で完了(要確認: 最悪の位相は 98%)」だけでは、候補を1つ
/// しか測っていないのか、全部測って選べなかったのかが分からない。上の不具合の
/// 切り分けに手間をかけたので、候補ごとの位相感度を必ず並べる。
enum AutoPhase {
    /// 上限まで過剰サンプルして占有率を測る
    Oversample,
    /// 8の倍数で局所探索(pll候補, 結果)
    Sweep { cands: Vec<u32>, i: usize, best: (u32, f32), med: Vec<f32> },
    /// 簡易: 候補を htotal の**大きい順**に、位相を8点振って「1:1かどうか」を見る。
    /// `k` は位相の点番号(位相 = k*4)
    QuickProbe { i: usize, k: u8, best: (u8, f32), worst: f32 },
    /// 位相を粗く振る
    PhaseCoarse { i: u8, best: (u8, f32), all: Vec<f32> },
    /// 位相を1刻みで詰める
    PhaseFine { list: Vec<u8>, i: usize, best: (u8, f32) },
}

/// スキャンの種類。**探索空間の広さだけが違う**。測り方(占有率と鮮鋭度)も
/// 位相の詰め方も同じ。
enum AutoMode {
    /// 簡易: プロファイルの水晶/分周が許すモードだけを見る。
    Quick {
        /// 測る順番。htotal の**降順**で、設定値(pll_divide)の重複は除いてある。
        /// 設定値が同じ点は測っても区別できないので1回で済ませる
        ladder: Vec<profiles::ScanPoint>,
        /// 候補ごとの (最良位相, その鮮鋭度, 最悪の鮮鋭度)。測った順に積む。
        /// 全候補を測り終えたら、位相感度(最悪÷最良)がいちばん小さい点を採る
        probes: Vec<(u8, f32, f32)>,
    },
    /// フル: プロファイルを使わず、絵のスペクトルだけから範囲を割り出して
    /// 8刻みで舐める。プロファイルに無いモードや、未知の機種で使う
    Full,
}

struct AutoTune {
    mode: AutoMode,
    phase: AutoPhase,
    /// この時刻まではボードの反映待ち
    wait_until: std::time::Instant,
    /// 待ち開始時点の測定回数。これより進んだ測定だけを採用する
    base_n: u64,
    /// 経過表示
    note: String,
    /// 最悪の位相(参考表示用)
    worst: f32,
    /// 半分にして測り直した回数
    attempt: u8,
    /// 簡易スキャンで選んだ点のオーバーサンプル倍率。
    /// **1より大きいなら位相感度が弱いのが正常**なので、最後の判定に使う
    over: u32,
    /// 簡易スキャンの判定の内訳(例 "1104→98% 736→53% 552→87%")。
    /// **結果だけだと外したときに切り分けられない。** 実機で1度そうなった
    report: String,
}

/// 位相を振っても鮮鋭度が変わらない(最悪÷最良がこれより大きい)なら、まだ
/// 1ドットが複数サンプルに広がっている = 過剰サンプル、と判定する。
///
/// 0.85 はフルスキャン側で実機から決めた値(15kHz帯で 0.95 = ほぼ変わらない、が
/// 過剰サンプルの実測)。簡易スキャンが1段降りるかどうかもこの1つの数字で決まる。
const PHASE_SENSITIVE: f32 = 0.85;

/// NTSCの1ライン[µs]と1フレームのライン数。管面の窓を時間とライン数で書くのに使う
const NTSC_LINE_US: f32 = 63.556;
const NTSC_LINES: f32 = 525.0;

/// コンポジット/S端子(YC8)の管面を `mon_bands` に置くキー。実在しない帯域番号
/// (帯域は kHz の値なので重ならない)。設定ファイルには `mon.1000` で残る。
const MON_KEY_NTSC: u32 = 1000;

/// コンポジット/S端子の管面の初期値 [H幅, H位置, V幅, V位置]。
///
/// ★**ビデオデッキの HDMI 出力と同じ範囲を映す**(2026-10-09 実測、白黒の格子
///   パターン。中央の点と格子を目印に、こちらの受信データと同じ物差しで比べた)。
///     横: 9.95〜60.87µs(= ntsc::ACTIVE_US)。中心 35.41µs が中央の点に一致
///     縦: 480ライン。フレームの 35.6〜515.6 行目(中央の点は 272.5 行目)
///   以前は15kHz帯の管面(RGB用)を共用していて、帰線区間の黒い余白まで映り、
///   中心も右へずれていた。
///   位置は「周期の中心からのずれ」で、絵を動かす向きに符号を取る(render.rs)。
const MON_NTSC: [f32; 4] = {
    let (h0, h1) = ntsc::ACTIVE_US;
    let (v0, v1) = (35.6, 515.6);
    [
        (h1 - h0) / NTSC_LINE_US,
        0.5 - (h0 + h1) * 0.5 / NTSC_LINE_US,
        (v1 - v0) / NTSC_LINES,
        0.5 - (v0 + v1) * 0.5 / NTSC_LINES,
    ]
};

/// 全候補を測り終えたあと、どれを採るかを決める。返り値は (添字, その位相感度)。
///
/// 位相感度(最悪÷最良)がいちばん小さい = 1ドットが1サンプルに載っている点を採る。
/// どれも `PHASE_SENSITIVE` を下回らなければ判別できていないので、**いちばん
/// 大きい候補(添字0)** に倒す。大きい側は整数倍の過剰サンプルで眠くなるだけだが、
/// 小さい側はドットを飛ばして絵が壊れる。非対称なので迷ったら上。
///
/// `probes` は (最良位相, 最良の鮮鋭度, 最悪の鮮鋭度) を候補の順(htotal降順)に。
/// 「画に合わせる」ときの目標のウィンドウ内寸。動かす必要が無ければ `None`。
///
/// `tex` は**画の実寸ではなく、いま画面に出ている(レターボックス後の)大きさ**。
/// だから `tex + 外側の余白` は必ず現在の内寸**以下**になる ─ つまりこの操作は
/// 「余白を削って縮める」。1回なら意図どおりだが、**繰り返すと縮み続ける**。
///
/// ★**丸め程度の差では動かさない。** 比が一致すれば余白は0になって収束する
///   はずだが、点と画素の丸めやパネル幅の増減で毎回わずかに残る。Windows の
///   DPI 拡大では1回あたりの目減りが大きく、**同期がふらつくたびに合わせ直して
///   窓が消えていった**(2026-09-10 実機。Macでは目減りが小さく気付かなかった)。
/// 要求した内寸と実寸のずれをどこまで許すか[point]。
/// 端数の丸めは通すが、タイトルバーや枠のぶん(数十point)は通さない。
const FIT_TOLERANCE: f32 = 4.0;

/// 要求してから答え合わせをするまでの猶予。ウィンドウマネージャの応答と
/// アニメーションを待つぶん。
const FIT_VERDICT_AFTER: std::time::Duration = std::time::Duration::from_millis(700);

/// 直前の内寸要求が通ったかの判定。
#[derive(Debug, PartialEq, Eq)]
enum FitVerdict {
    /// まだ分からない(猶予内)。要求を保持して次のフレームで見直す
    Pending,
    /// 要求どおりになった
    Honored,
    /// 猶予を過ぎても要求と違う。以後この環境では自動サイズ合わせをしない
    Ignored,
}

fn fit_verdict(
    requested: egui::Vec2,
    actual: egui::Vec2,
    elapsed: std::time::Duration,
) -> FitVerdict {
    if (actual - requested).length() <= FIT_TOLERANCE {
        FitVerdict::Honored
    } else if elapsed >= FIT_VERDICT_AFTER {
        FitVerdict::Ignored
    } else {
        FitVerdict::Pending
    }
}

fn fit_target(
    window: egui::Vec2,
    avail: egui::Vec2,
    tex: egui::Vec2,
    monitor: Option<egui::Vec2>,
) -> Option<egui::Vec2> {
    let chrome = window - avail;
    let mut want = tex + chrome;
    // 画面より大きくしない(はみ出すと操作できなくなる)
    if let Some(mon) = monitor {
        want = want.min(mon * 0.95);
    }
    let delta = (want - window).abs();
    (delta.x > 3.0 || delta.y > 3.0).then_some(want)
}

fn quick_pick(probes: &[(u8, f32, f32)]) -> (usize, f32) {
    let rel_of = |p: &(u8, f32, f32)| if p.1 > 0.0 { p.2 / p.1 } else { 1.0 };
    let (mut j, mut min_rel) = (0usize, f32::MAX);
    for (idx, p) in probes.iter().enumerate() {
        let r = rel_of(p);
        if r < min_rel {
            (j, min_rel) = (idx, r);
        }
    }
    if min_rel > PHASE_SENSITIVE {
        j = 0;
    }
    (j, min_rel)
}

const AUTO_PLL_MIN: u32 = 200;
const AUTO_PLL_MAX: u32 = 2304;

struct Session {
    shared: Arc<receiver::Shared>,
    /// 再生中の音声source(UI表示用)
    audio_source: Option<u8>,
    /// 出力デバイス一覧(起動時に列挙。再列挙ボタンで更新)
    audio_devices: Vec<String>,
    /// UIで選択中のデバイス。None は「システム既定」
    audio_device_sel: Option<String>,
    /// 音量(0.0..1.5、1.0=原音)。ミュート時も値は保持してトグルで戻せるようにする
    audio_volume: f32,
    audio_muted: bool,
    /// 設定の保存(スライダー操作中に毎フレーム書かないよう、変更後に少し待って書く)
    settings_dirty: Option<std::time::Instant>,
    /// 画枠パラメータ(ボードへCONFIGで送る値)。モードごとに最適値が違うので、
    /// ビルドし直さずにここで追い込む。
    tune_vbp: i32,
    tune_hs_offset: i32,
    tune_pll_divide: i32,
    /// TVPのアナログ映像帯域。0=最大 / 15=最小(約95MHz)
    tune_video_bw: u8,
    /// 1ラインまるごと送る(非黒範囲の最適化を切る)。
    /// 全黒行の直後の数行で範囲判定が壊れて行が欠ける不具合の回避策。
    tune_full_line: bool,
    /// フレーム間引き。0=毎フレーム / 1=2フレームに1回 …
    /// 受信が追いつかない機械での保険。音声は間引かない
    tune_frame_skip: u8,
    /// 復調を止めて生のYを見る(切り分け用。設定には保存しない)
    raw_view: bool,
    /// 表示するフィールド 0=織り込み / 1=偶数 / 2=奇数(同上)
    field_view: u8,
    /// 見た目の調整(彩度・明るさ・コントラスト・色相)。設定に保存する
    adjust: ntsc::Adjust,
    /// 管面の幾何に使う vtotal(スロット数)を平滑した値。**整数のまま使わない。**
    ///
    /// ★インターレースは 262.5 ライン/フィールドなので、ボードが測る vtotal は
    ///   262 と 263 を交互に返すのが正常。瞬間値を幾何に使うと縦のスケールが
    ///   フレームごとに 0.38% 変わり、絵が上下に震える(実機で「横線の縦位置が
    ///   フレームごとに動いて二重線に見える」形で出た。片フィールド表示でも
    ///   残ったので、織り込みではなく幾何側だと切り分けられた)。
    /// (描画中に更新するので Cell。paint_tube を &mut self にすると波及が大きい)
    vtotal_smooth: std::cell::Cell<f32>,
    /// 前回 vtotal_smooth を更新した時刻。平滑の時定数を**時間で**決めるのに使う。
    /// フレーム数で決めると、MODEが1秒に1〜2回しか来ないのに60Hzで回るせいで
    /// 収束しきってしまい、平均されずに追従する(実機で縦が数ピクセル伸び縮みした)
    vtotal_last_t: std::cell::Cell<Option<std::time::Instant>>,
    /// 平滑をリセットする判定用。モードが変わったら追従を待たずに飛ばす
    vtotal_mode_id: std::cell::Cell<u16>,
    /// 直近で入力設定を書き込んだソース(ラベル, 件数, 自動か)。パネルの確認表示用。
    /// 一時通知(スナックバー)
    toasts: toast::Toasts,
    /// 伝送形式が映像ソースと食い違ったので `input_regs` を自動で書いたか。
    /// **食い違いが解消したら false に戻す**ので、ボードの電源を入れ直すたびに
    /// 1回だけ書き直す。書いてから MODE が変わるまでの間に何度も書かないための掛け金。
    input_regs_autowritten: bool,
    /// 映像ソースのプロファイル名(profiles::PROFILES の key)。空文字は「自動」。
    /// pll_divide を絵の内容ではなく fH とドットクロック候補から決めるのに使う
    source_profile: String,
    tune_phase: u8,
    /// 送信したがまだボードの応答で確認できていない値(key → (値, 送信時刻))。
    /// 応答が返るまでは自分の値を優先し、押した瞬間に元へ戻って見えるのを防ぐ。
    tune_pending: std::collections::HashMap<u16, (u32, std::time::Instant)>,
    /// 次に現在値を問い合わせる時刻。全キーが揃うまで繰り返す
    tune_get_at: Option<std::time::Instant>,
    /// 「ボード」欄の編集中テキスト。**ボードの値を直接いじらない** ─
    /// 1文字打つたびにCONFIGが飛ぶと、打ちかけの名前が基板に載る。
    /// None は「まだ編集を始めていない(ボードの値をそのまま出す)」。
    ident_name_edit: Option<String>,
    ident_ip_edit: Option<String>,
    /// 個体設定を最後に問い合わせた時刻。ボードを選び直したら取り直す
    ident_get_at: Option<std::time::Instant>,
    /// いま個体設定を読み込んであるボードのMAC。切り替えを検知する
    ident_for: Option<[u8; 6]>,
    /// 最後に見たボード側の値。**これが変わったら編集欄を捨てる。**
    /// SETの応答が返るとボードの値が変わるので、編集欄に古いテキストが
    /// 残っていると「適用/戻す」が出たままになり、押すと古い名前が飛ぶ。
    ident_name_seen: Option<String>,
    ident_ip_seen: Option<u32>,
    /// ボードの現在値を取り込み済みか。起動時に1回だけ合わせる
    tune_synced: bool,
    /// TVPの細ゲイン(レジスタ08h/09h/0Ah)。ゲイン = 1 + N/256。
    /// **基板ごとに違う**ので手で詰められるようにする。値はボードから読み戻す。
    tune_gain_r: i32,
    /// SOGスライス閾値(レジスタ10h bit[7:3]、5bit)。**同期をどの高さで切るか。**
    /// 低すぎると暗い映像を同期と誤認して垂直検出が壊れる。映像源ごとに違うので
    /// 絵を見ながら振れるようにする。値はボードから読み戻す。
    tune_sog_thresh: i32,
    /// 同期処理制御(レジスタ22h)。bit0=VS Bypass / bit1=VS Select。
    /// 既定 0x08 は VSOUT をハーフライン積算器に作らせる(525ライン前提)。
    tune_sync_ctl2: i32,
    /// SOGOUTのLow期間を「垂直ブロードパルス」とみなす閾値[pixクロック]。
    /// 捕捉側はこれで垂直区間を見つけ、その瞬間のライン内位相からフィールド極性を出す。
    tune_sog_vth: i32,
    /// フィールド極性の向き(0/1)。経路によって符号が変わる。
    tune_field_invert: i32,
    /// 生同期(TTL)の位相をフィールド極性に使わないか。0=使う / 1=使わない。
    /// 生同期を繋がない方式では 1(浮いた同期入力の自己発振で raw_ok が誤って立つ)。
    tune_no_raw_phase: i32,
    /// lines/frame などの読み出し専用ステータスを次に問い合わせる時刻。
    /// これらは**変化する値**なので、tune 値と違って繰り返し取り直す。
    stat_get_at: Option<std::time::Instant>,
    /// 伝送形式(0x36)。0=RGB888 / 1=RGB555 / 3=YC8。
    /// ゲートウェアは実行時に切り替えるので、他の tune 値と同じ扱いにする
    tune_pixfmt: i32,
    tune_gain_g: i32,
    tune_gain_b: i32,
    /// 現在のウィンドウ内寸(保存用)
    window_size: egui::Vec2,
    /// ウィンドウ位置(復元用)。並びを戻すのに要る
    window_pos: Option<egui::Pos2>,
    /// このセッションのビューポートを一度でも出したか。
    ///
    /// ★**位置と大きさは最初の1回しか指定しない。** 毎フレーム
    ///   `ViewportBuilder` に載せると、eframe が差分を見て毎回
    ///   「ここへ動かせ」を送る。ユーザがドラッグしても次のフレームで
    ///   引き戻され、**掴んでも動かせないウィンドウ**になる。
    viewport_shown: bool,
    /// 最後に心拍(=設定の保存)を打った時刻
    settings_beat: Option<std::time::Instant>,
    /// アプリへの要求: 新しいウィンドウを開きたい(次のフレームで App が拾う)。
    /// 指定があればそのボードを選んだ状態で開く。
    want_new_window: Option<Option<[u8; 6]>>,
    /// このウィンドウの番号。設定ファイル・GPUテクスチャ・ビューポートIDの鍵。
    ///
    /// ★**空いているうち最小を割り当てる。** 0,1,2 を開いて1を閉じ、また開けば
    ///   1が返るので、そのウィンドウの設定(画枠・音量・接続先・位置)が
    ///   そのまま復元される。
    slot_id: u32,
    /// 接続先の指定(自動 / 特定の基板 / つながない)
    board_sel: settings::BoardSel,
    /// 中央の描画領域と画のサイズ。ウィンドウを等倍に合わせるのに使う
    last_avail: egui::Vec2,
    last_tex: egui::Vec2,
    /// 起動後に一度だけ自動で等倍に合わせたか
    did_autofit: bool,
    /// 次のフレームでウィンドウを等倍に合わせる
    want_fit: bool,
    /// 切り替わりかけているモードと、それを最初に見た時刻。
    ///
    /// ★**すぐには追従しない。** モードは fh/vtotal/htotal の**測定値**から
    ///   作るので、同期が一瞬乱れるだけで別のモードに見える。そのたびに
    ///   切り出しと回転をリセットしていたため、**絵が飛んでいた**
    ///   (2026-09-10。ボード側で vactive が 568→372 に飛ぶ現象を実測)。
    pending_mode: Option<(String, std::time::Instant)>,
    /// 最後にウィンドウを合わせたときの「絵の大きさを決める要素」。
    ///
    /// ★**モードキーとは別に持つ。** モードキーは fh/htotal/vtotal で作るので、
    ///   映像が乱れて同期がふらつくと**絵の大きさは変わっていないのに**変化する。
    ///   それでウィンドウを合わせ直していたため、乱れるたびに窓が縮んでいった。
    fitted_sig: Option<(u16, u16, u32, [u32; 4])>,
    /// 直前に OS へ要求した内寸。次のフレームで実際の内寸と突き合わせる。
    ///
    /// ★**要求どおりにならない環境がある。** `fit_target` は
    ///   「余白 = 内寸 - 描画領域」を測って、その余白ぶんを足した内寸を要求する。
    ///   要求した内寸と、次に測れる内寸がずれる環境では、そのずれが毎回余白に
    ///   化けて積もり、合わせ直すたびにウィンドウが縮んでいく(Windows で発生。
    ///   macOS では出なかった)。**ずれを見つけたら合わせるのをやめる。**
    ///   合っていない環境で反復しても正しい大きさには辿り着けないし、
    ///   ユーザーが手で決めた大きさを奪い続ける方がずっと害が大きい。
    fit_requested: Option<(egui::Vec2, std::time::Instant)>,
    /// 要求が通らないと分かった環境では、自動サイズ合わせを止める
    fit_disabled: bool,
    /// 受信中フレームの寸法(GPUテクスチャは callback_resources 側が持つ)
    frame_size: (u32, u32),
    render_state: Option<eframe::egui_wgpu::RenderState>,
    seen_gen: u64,
    /// 画面回転 0/1/2/3 = 時計回りに 0/90/180/270 度
    rotate: u32,
    /// 表示する切り出し範囲[画素]。w か h が 0 なら全体を表示
    crop: [u32; 4],
    /// 管面の縦横比(幅/高さ)。0 なら有効映像の比のまま
    tube_aspect: f32,
    /// 右の操作パネルを表示するか。隠すと映像(と枠)だけになる。
    /// 隠すと戻すUIが無くなるので、Tabキーで必ず戻せるようにしてある。
    show_panel: bool,
    /// モニタの枠(ベゼル)の名前。空文字は枠なし
    bezel: String,
    /// 枠を一時的に隠す。プルダウンの選択(bezel)は保ったまま切り替えたいので、
    /// 「なし」を選ぶのとは別に持つ。B キーで切り替える。
    bezel_off: bool,
    /// 配信用クリーン出力ウィンドウ(OBS のウィンドウキャプチャ用)
    clean_open: bool,
    clean_size: [f32; 2],
    clean_undecorated: bool,
    /// 調査用の数値と細かい設定を出すか
    show_advanced: bool,
    /// 音声入力を映像ソースに追従させるか
    audio_auto: bool,
    /// S/PDIF を主系統へ混ぜるか
    spdif_mix: bool,
    /// S/PDIF の音量(主系統とは独立)
    spdif_volume: f32,
    /// 実際にウィンドウへ適用済みの値。設定変更を1回だけ送るために持つ
    clean_size_applied: [f32; 2],
    clean_undecorated_applied: bool,
    /// 枠のテクスチャ。ラスタライズした幅と一緒に持ち、幅が変わったら作り直す
    bezel_tex: Option<(egui::TextureHandle, u32)>,
    /// 補間 0=ニアレスト 1=バイリニア 2=sharp-bilinear
    filter: u32,
    /// ドット復元の係数 a ×1000。0=無効。詳細は assembler の dot_a_milli
    dot_a_milli: u32,
    /// インターレース時の残光(1.0=減衰しない)。設定に保存する
    interlace_decay: f32,
    /// 管面が映す時間窓 [h0,h1,v0,v1]。CRTのH位置/H幅・V位置/V幅に相当
    window: [f32; 4],
    tube_time_based: bool,
    /// いまの帯域のモニタプロファイル [H幅, H位置, V幅, V位置]。
    /// 1周期のうち管面に出る割合と、周期の中心からのずれ
    mon: [f32; 4],
    /// 帯域ごとのモニタプロファイル(CZ-612Dのような3モードディスプレイに相当)
    mon_bands: std::collections::BTreeMap<u32, [f32; 4]>,
    /// 帯域ごとの [pll_divide, 位相]
    band_pll: std::collections::BTreeMap<u32, [u32; 2]>,
    /// いまの周波数帯[kHz]。0 は未確定
    band_khz: u32,
    /// `mon_bands` を引くキー。普段は `band_khz` と同じで、コンポジット/S端子
    /// (YC8)のときだけ `MON_KEY_NTSC` になる。0 は未確定
    mon_key: u32,
    auto: Option<AutoTune>,
    /// 自動調整の結果表示(完了後に残す)
    auto_done: Option<String>,
    /// モードごとの切り出し・回転。キーは fH_vtotal_htotal
    modes: std::collections::BTreeMap<String, [u32; 6]>,
    /// いま適用しているモードのキー(変化したら保存・復元する)
    mode_key: String,
    rx_error: Option<String>,
    subscribe_to: Option<String>,
    no_vsync: bool,
    pace: PaceMeter,
    /// MimicX へのキー転送。起動時は常にOFF(保存しない)。ONのまま起動すると
    /// キーが黙って実機へ流れるので、毎回明示的に入るようにしている
    remote: remote_input::RemoteInput,
    /// 転送ON/OFF操作(⌘+Shift+ESC / F12)の検出。押下の瞬間だけを拾う
    remote_toggle: remote_input::ToggleDetect,
    /// 物理キーの取り出し口。egui の Key では JIS の ¥/_/かな が落ちるので、
    /// AppKit のイベントを直接見る(keytap.rs)
    keytap: Option<keytap::KeyTap>,
    /// NIC受信バッファーの確認結果。ボードが見つかってから1回だけ調べる
    /// (レジストリを読むだけなので同期でよい)
    netcheck: Option<netcheck::Buffers>,
    /// 起動時のダイアログを出すか。**確度の高い設定チェックのときだけ**立てる
    /// (ロス率は推定なうえセッション中に発火するので、割り込ませない)
    netcheck_modal: bool,
    /// 「今後表示しない」。設定に保存する
    netcheck_muted: bool,
    /// 直ったことを確認したので、再起動を勧めるダイアログを出す。
    ///
    /// ★**直った直後が勧めどき。** 受信バッファーはNICドライバのリングなので、
    ///   広げても**すでに開いているソケットの取りこぼしの記録は消えない**し、
    ///   アダプタのリセットで購読も切れている。ここで再起動を促さないと
    ///   「直したのに lost が増えたまま」で直っていないように見える。
    netcheck_restart_ask: bool,
    /// 「直す」を押した結果。**押しただけで終わりにしない** ─ UACを拒否したり
    /// ドライバが受け付けなかったりするので、確かめ直して結果を出す。
    netcheck_fix: Option<String>,
    /// 直したあとに調べ直す時刻(アダプタのリセットが終わるのを待つ)
    netcheck_recheck_at: Option<std::time::Instant>,
}

impl Session {
    /// 映像のフレームが来ているか。受信が途絶えると統計は 200ms の待ちで
    /// 更新されて fps が 0 に戻るので、ボードを外せば1秒以内に偽になる。
    /// 音声だけ来ている状態は数えない(スリープ抑止の条件に使うため)
    fn receiving_video(&self) -> bool {
        self.shared.stats.lock().unwrap().fps > 1.0
    }

    /// ★**`CreationContext` を受け取らない。** 起動時にしか手に入らないので、
    ///   受け取っていると**実行中にウィンドウを増やせない**。必要なのは
    ///   `egui::Context` と wgpu の描画状態だけで、どちらも後からでも取れる。
    #[allow(clippy::too_many_arguments)]
    fn new(
        slot_id: u32,
        egui_ctx: &egui::Context,
        render_state: Option<eframe::egui_wgpu::RenderState>,
        port: u16,
        subscribe_to: Option<String>,
        target_mac: Option<[u8; 6]>,
        bind: String,
        no_vsync: bool,
        decay: f32,
    interlace_decay: f32,
        audio: receiver::AudioOpts,
        cfg: settings::Settings,
    ) -> Self {
        let audio_source = audio.source;
        let shared = Arc::new(receiver::Shared::default());
        let ctx = egui_ctx.clone();
        let rx_error = receiver::spawn(
            receiver::Config { port, bind: bind.clone(), subscribe_to: subscribe_to.clone(), target_mac, decay, interlace_decay, audio },
            shared.clone(),
            move || ctx.request_repaint(),
        )
        .err()
        .map(|e| format!("UDP {port} bind failed: {e}"));
        let mut app = Self {
            shared,
            audio_source,
            audio_devices: audio::output_devices(),
            audio_device_sel: cfg.audio_device.clone(),
            audio_volume: cfg.volume,
            audio_muted: cfg.muted,
            settings_dirty: None,
            tune_vbp: cfg.tune_vbp,
            tune_hs_offset: cfg.tune_hs_offset,
            tune_pll_divide: cfg.tune_pll_divide,
            tune_video_bw: cfg.tune_video_bw,
            tune_full_line: cfg.tune_full_line,
            tune_frame_skip: cfg.tune_frame_skip,
            tune_phase: cfg.tune_phase,
            raw_view: false,
            field_view: 0,
            adjust: ntsc::Adjust {
                hue_deg: cfg.adj_hue_deg,
                saturation: cfg.adj_saturation,
                brightness: cfg.adj_brightness,
                contrast: cfg.adj_contrast,
                gamma: if cfg.adj_gamma > 0.0 { cfg.adj_gamma } else { 1.0 },
            },
            vtotal_smooth: std::cell::Cell::new(0.0),
            vtotal_last_t: std::cell::Cell::new(None),
            vtotal_mode_id: std::cell::Cell::new(u16::MAX),
            toasts: toast::Toasts::default(),
            input_regs_autowritten: false,
            source_profile: cfg.source_profile.clone(),
            tune_pending: Default::default(),
            tune_get_at: None,
            ident_name_edit: None,
            ident_ip_edit: None,
            ident_get_at: None,
            ident_for: None,
            ident_name_seen: None,
            ident_ip_seen: None,
            tune_synced: false,
            // 初期値は REGS_X68000 と同じ(v0.9.0 で校正した値)。
            // 実際の値はボードから読み戻して上書きされる
            tune_gain_r: 64,
            // 初期値はゲートウェアの既定。起動時にボードから読み戻して合わせる
            tune_sog_thresh: 0x0B,
            tune_sync_ctl2: 0x08,
            tune_sog_vth: 400,
            tune_field_invert: 0,
            tune_no_raw_phase: 0,
            stat_get_at: None,
            tune_pixfmt: protocol::PIXFMT_RGB555 as i32,
            tune_gain_g: 61,
            tune_gain_b: 57,
            window_size: egui::vec2(cfg.window_w, cfg.window_h),
            window_pos: cfg.window_x.zip(cfg.window_y).map(|(x, y)| egui::pos2(x, y)),
            viewport_shown: false,
            settings_beat: None,
            want_new_window: None,
            slot_id,
            board_sel: cfg.board_sel,
            last_avail: egui::Vec2::ZERO,
            last_tex: egui::Vec2::ZERO,
            did_autofit: false,
            want_fit: false,
            pending_mode: None,
            fitted_sig: None,
            fit_requested: None,
            fit_disabled: false,
            frame_size: (0, 0),
            render_state,
            seen_gen: 0,
            rotate: cfg.rotate,
            crop: [cfg.crop_x, cfg.crop_y, cfg.crop_w, cfg.crop_h],
            tube_aspect: cfg.tube_aspect,
            show_panel: cfg.show_panel,
            bezel: cfg.bezel.clone(),
            bezel_off: cfg.bezel_off,
            clean_open: cfg.clean_open,
            clean_size: cfg.clean_size,
            clean_undecorated: cfg.clean_undecorated,
            show_advanced: cfg.show_advanced,
            audio_auto: cfg.audio_auto,
            spdif_mix: cfg.spdif_mix,
            spdif_volume: cfg.spdif_volume,
            clean_size_applied: cfg.clean_size,
            clean_undecorated_applied: cfg.clean_undecorated,
            bezel_tex: None,
            filter: cfg.filter,
            dot_a_milli: cfg.dot_a_milli,
            interlace_decay: cfg.interlace_decay,
            window: cfg.window,
            tube_time_based: cfg.tube_time_based,
            mon: cfg.mon,
            mon_bands: cfg.mon_bands.clone(),
            band_pll: cfg.band_pll.clone(),
            band_khz: 0,
            mon_key: 0,
            auto: None,
            auto_done: None,
            modes: cfg.modes.clone(),
            mode_key: String::new(),
            rx_error,
            subscribe_to,
            no_vsync,
            pace: PaceMeter::new(),
            remote: remote_input::RemoteInput::default(),
            remote_toggle: Default::default(),
            // ★**キー横取りは1つだけ。** AppKit のイベント監視をウィンドウの数だけ
            //   仕掛けると同じキーが何度も実機へ飛ぶ。転送するのは主ウィンドウだけ。
            keytap: (slot_id == 0).then(|| keytap::KeyTap::install(egui_ctx)),
            netcheck: None,
            netcheck_modal: false,
            netcheck_muted: cfg.netcheck_muted,
            netcheck_restart_ask: false,
            netcheck_fix: None,
            netcheck_recheck_at: None,
        };
        // ★起動時にも一度合わせる。設定に前回の音声入力が残っていても、
        //   復元した映像ソースと食い違ったままにしない。
        app.apply_auto_audio();
        // ★パネルを一度も開かなくても効くように、起動時に一度入れておく。
        //   UI の描画に依存させると「閉じたまま起動 → S/PDIF が鳴らない」になる。
        app.shared.aux.set(app.spdif_mix, app.spdif_volume);
        app
    }

    fn refresh_texture(&mut self, ctx: &egui::Context) {
        let generation = self.shared.frame_gen.load(Ordering::Acquire);
        if generation == self.seen_gen {
            return;
        }
        self.seen_gen = generation;
        self.pace.on_new_frame();
        // ★**ロックの順序が逆だった。** 以前はフレームのロックを持ったまま
        //   `rs.renderer.write()` を取りに行っていた。描画中はレンダラのロックが
        //   取れないので、paint が 19ms かかる間ずっとフレームのロックを握り続け、
        //   受信側の `shared.frame.lock()` がその間ブロックされていた。
        //   レンダラを先に取れば、フレームのロックはGPU転送の間だけで済む。
        //   (両方を取るのはここだけなので、順序を入れ替えても行き詰まらない)
        if let Some(rs) = self.render_state.as_ref() {
            let mut w = rs.renderer.write();
            let guard = self.shared.frame.lock().unwrap();
            let Some(frame) = guard.as_ref() else { return };
            self.frame_size = (frame.width as u32, frame.height as u32);
            if let Some(m) = w.callback_resources.get_mut::<render::Blits>() {
                m.entry(self.slot_id, &rs.device, rs.target_format).upload(
                    &rs.device, &rs.queue, &frame.rgba,
                    frame.width as u32, frame.height as u32);
            }
        } else {
            let guard = self.shared.frame.lock().unwrap();
            if let Some(frame) = guard.as_ref() {
                self.frame_size = (frame.width as u32, frame.height as u32);
            }
        }
        let _ = ctx;
    }
}

impl Session {
    /// いま使う枠。bezel_off なら枠なしとして扱う(選択は保つ)。
    fn active_bezel(&self) -> Option<&'static bezel::Bezel> {
        if self.bezel_off {
            None
        } else {
            bezel::by_key(&self.bezel)
        }
    }

    /// 管面(GPUで描く映像)を指定した矩形へ描く。
    ///
    /// Retina では論理座標と実画素が違う。sharp-bilinear は出力画素数を基準に
    /// 境目の幅を決めるので、実画素で渡す。
    fn paint_tube(&self, ui: &mut egui::Ui, rect: egui::Rect) {
        let ppp = ui.ctx().pixels_per_point();
        ui.painter().add(eframe::egui_wgpu::Callback::new_paint_callback(
            rect,
            render::Callback {
                session: self.slot_id,
                params: self.render_params(),
                dst: (rect.width() * ppp, rect.height() * ppp),
            },
        ));
    }

    /// パネルのセクション見出し。
    ///
    /// ★以前は `ui.strong()` だけだったので、本文の monospace と字面が近く
    ///   「どこでセクションが切れているか」が読み取れなかった。区切り線は
    ///   既に各セクションの終わりに入っているので、ここでは大きさと余白で
    ///   段差を付ける。
    fn section(ui: &mut egui::Ui, title: &str) {
        theme::section(ui, title);
    }

    /// パネル最上部の簡易スキャン。
    ///
    /// ★**Tune の奥にもあるが、そこはスクロールしないと届かない。** モードが
    ///   変わるたびに押すものなので、いちばん上に出して S キーでも叩けるように
    ///   してある。実体は同じ `auto_start_quick()`。
    fn quick_scan_bar(&mut self, ui: &mut egui::Ui) {
        ui.horizontal(|ui| {
            if self.auto.is_some() {
                if ui.button("中止").clicked() {
                    self.auto = None;
                    self.auto_done = Some("中止しました".into());
                }
                if let Some(a) = self.auto.as_ref() {
                    ui.monospace(a.note.clone());
                }
            } else {
                let n = self.scan_candidates().len();
                let btn = ui.add_enabled(
                    n > 0,
                    egui::Button::new(egui::RichText::new("簡易スキャン").strong()),
                );
                let btn = btn.on_hover_text(if n > 0 {
                    format!(
                        "候補 {n} 点の位相感度を測って、いちばん感度が強い点を採ります\n\
                         (候補1つにつき8秒ほど。位相も最適値に合わせます)。\n\
                         S キーでも実行できます。詳細は Tune の同じボタンを参照"
                    )
                } else {
                    "この fH を説明できる候補がありません\n\
                     (MODE未受信か、プロファイルに無いドットクロック)".to_string()
                });
                if btn.clicked() {
                    self.auto_start_quick();
                }
                ui.weak("S");
                // ★詳細の出し入れはここに置く。**調査用の数値と細かい設定が
                //   常用時の表示に混ざっていて読みづらい**ため、既定では畳む。
                ui.separator();
                let mut adv = self.show_advanced;
                if ui.checkbox(&mut adv, "詳細")
                    .on_hover_text(
                        "調査用の数値(present方式・CPU時間・パケット統計など)と、\n\
                         細かい設定(vbp / hs_offset / pll_div / 間引き / 帯域制限 / 位相)を\n\
                         出し入れします。問題を追うときだけ開けば十分です")
                    .changed()
                {
                    self.show_advanced = adv;
                    self.mark_settings_dirty();
                }
            }
        });
        // 直前の結果はここに出す。押した場所の近くに出ないと見落とす
        if self.auto.is_none() {
            if let Some(d) = self.auto_done.clone() {
                ui.weak(d);
            }
        }
    }

    /// 配信用クリーン出力ウィンドウを1フレーム描く。
    ///
    /// 本体と同じ `paint_tube`(同じシェーダ)を、UIもベゼルも無い別ウィンドウへ
    /// 出すだけ。OBS の「ウィンドウキャプチャ」でこれを掴めば、調整UIを写り込ませずに
    /// 配信ソースにできる。
    fn clean_output(&mut self, ctx: &egui::Context) {
        if !self.clean_open {
            return;
        }
        let opts = cleanout::Opts {
            session: self.slot_id,
            size: self.clean_size,
            resize: self.clean_size != self.clean_size_applied,
            undecorated: self.clean_undecorated,
            redecorate: self.clean_undecorated != self.clean_undecorated_applied,
            aspect: cleanout::display_aspect(
                self.frame_size, self.crop, self.tube_aspect_eff(), self.rotate),
            has_video: self.frame_size.0 > 0,
        };
        let keep = cleanout::show(ctx, &opts, |ui, rect| self.paint_tube(ui, rect));
        self.clean_size_applied = self.clean_size;
        self.clean_undecorated_applied = self.clean_undecorated;
        if !keep {
            self.clean_open = false;
            self.mark_settings_dirty();
        }
    }

    /// 現在のUI状態を設定として書き出す。スライダー操作中に毎フレーム書くのを
    /// 避けるため、変更を記録して少し待ってから1回だけ保存する。
    fn mark_settings_dirty(&mut self) {
        self.settings_dirty = Some(std::time::Instant::now());
    }

    fn flush_settings(&mut self) {
        if self.mon_key > 0 {
            self.mon_bands.insert(self.mon_key, self.mon);
        }
        if self.band_khz > 0 {
            let k = self.band_khz;
            self.band_pll.insert(k, [self.tune_pll_divide.max(0) as u32,
                                     self.tune_phase as u32]);
        }
        if !self.mode_key.is_empty() {
            let k = self.mode_key.clone();
            self.modes.insert(k, [self.crop[0], self.crop[1], self.crop[2],
                                  self.crop[3], self.rotate, self.tune_phase as u32]);
        }
        let due = self
            .settings_dirty
            .map_or(false, |t| t.elapsed() >= std::time::Duration::from_millis(700));
        if !due {
            return;
        }
        self.settings_dirty = None;
        settings::Settings {
            volume: self.audio_volume,
            muted: self.audio_muted,
            audio_source: self.audio_source,
            audio_device: self.audio_device_sel.clone(),
            rotate: self.rotate,
            tube_aspect: self.tube_aspect,
            dot_a_milli: self.dot_a_milli,
            show_panel: self.show_panel,
            netcheck_muted: self.netcheck_muted,
            bezel: self.bezel.clone(),
            bezel_off: self.bezel_off,
            clean_open: self.clean_open,
            clean_size: self.clean_size,
            clean_undecorated: self.clean_undecorated,
            show_advanced: self.show_advanced,
            audio_auto: self.audio_auto,
            spdif_mix: self.spdif_mix,
            spdif_volume: self.spdif_volume,
            filter: self.filter,
            interlace_decay: self.interlace_decay,
            adj_hue_deg: self.adjust.hue_deg,
            adj_saturation: self.adjust.saturation,
            adj_brightness: self.adjust.brightness,
            adj_contrast: self.adjust.contrast,
            adj_gamma: self.adjust.gamma,
            window: self.window,
            tube_time_based: self.tube_time_based,
            mon: self.mon,
            mon_bands: self.mon_bands.clone(),
            band_pll: self.band_pll.clone(),
            modes: self.modes.clone(),
            crop_x: self.crop[0],
            crop_y: self.crop[1],
            crop_w: self.crop[2],
            crop_h: self.crop[3],
            board_sel: self.board_sel,
            // 生きている間は心拍を打つ。落ちても最後の時刻が残るので復元できる
            last_used: settings::Settings::now_unix(),
            window_x: self.window_pos.map(|p| p.x),
            window_y: self.window_pos.map(|p| p.y),
            window_w: self.window_size.x,
            window_h: self.window_size.y,
            tune_vbp: self.tune_vbp,
            tune_hs_offset: self.tune_hs_offset,
            tune_pll_divide: self.tune_pll_divide,
            tune_video_bw: self.tune_video_bw,
            tune_full_line: self.tune_full_line,
            tune_frame_skip: self.tune_frame_skip,
            tune_phase: self.tune_phase,
            source_profile: self.source_profile.clone(),
        }
        .save_slot(self.slot_id);
    }

    /// 音声の状態表示 + 出力デバイス/source の選択UI。
    /// cpalのStreamは生成スレッドから動かせないので、選択は「要求」として置き、
    /// 受信スレッドが再生器を作り直す。
    /// 映像入力の選択。**もっともよく使う操作なのでパネル上部に置く。**
    ///
    /// ★以前は Tune の中にあったが、Tune は問題を追うときの場所なので
    ///   常用の操作がそこにあるのは筋が悪かった。送信は自前で完結させて
    ///   いるので、Tune が畳まれていても入力は切り替えられる。
    fn source_ui(&mut self, ui: &mut egui::Ui) {
        let mut send: Vec<(u16, u32)> = Vec::new();
        // 映像ソースは「配線の方式」でもある。選んだらその入力設定をボードへ書く。
        //
        // ★**TVPのレジスタは電源で消える。** ビットストリームをSPIフラッシュに
        //   焼いても、pixfmt・入力MUX・同期の取り方・クランプ・ゲインは
        //   CONFIG で入れ直す必要がある。以前は毎回
        //   `python3 -m retrocastx.videoin apply composite` を叩いていた。
        //   同じ選択を選び直してもコンボは反応しないので、書き直しボタンも要る。
        ui.horizontal(|ui| {
            theme::label_col(ui, "映像ソース");
            let cur = self.source_profile.clone();
            let mut sel = cur.clone();
            let name = |k: &str| -> String {
                if k.is_empty() {
                    "自動".into()
                } else {
                    profiles::by_key(k).map_or_else(|| k.to_string(), |p| p.label.to_string())
                }
            };
            egui::ComboBox::from_id_salt("srcprof")
                .width(190.0)
                .selected_text(name(&cur))
                .show_ui(ui, |ui| {
                    ui.selectable_value(&mut sel, String::new(), "自動");
                    for p in profiles::PROFILES {
                        ui.selectable_value(&mut sel, p.key.to_string(), p.label);
                    }
                });
            let changed = sel != cur;
            if changed {
                self.source_profile = sel;
                self.mark_settings_dirty();
                // ★入力を切り替えたら音声も付いてくる(「自動」のときだけ)
                self.apply_auto_audio();
            }
            let prof = profiles::by_key(&self.source_profile);
            let has_regs = prof.is_some_and(|p| !p.input_regs.is_empty());
            let write = ui
                .add_enabled(has_regs, egui::Button::new("入力設定を書き込む"))
                .on_hover_text(
                    "TVPの入力MUX・同期の取り方・クランプ・ゲイン・伝送形式を書く。\n\
                     ボードの電源を入れ直すと消えるので、そのときはここを押す\n\
                     (焼き直しは不要。全部CONFIGで済む)",
                )
                .clicked();
            if let Some(p) = prof {
                if (changed || write) && !p.input_regs.is_empty() {
                    // ★伝送形式は、**いまのボードの値でこのソースが成立するなら
                    //   上書きしない**。実行時に選べるようにしたので、
                    //   X68000 RGB を RGB888 で見ているところへ入力設定を書いて
                    //   黙って RGB555 に戻されると、選択が消えたように見える。
                    //   YC8 が要るソース(コンポジット/S端子)や、ボードが
                    //   別種の形式で止まっている場合は上書きする(救済が要る)。
                    let have = self.shared.mode.lock().unwrap().as_ref().map(|m| m.pixfmt);
                    let is_rgb = |f: u8| matches!(f, protocol::PIXFMT_RGB888
                                                    | protocol::PIXFMT_RGB555
                                                    | protocol::PIXFMT_RGB565);
                    let keep_fmt = match (p.pixfmt(), have) {
                        (Some(want), Some(h)) if want != protocol::PIXFMT_YC8 => is_rgb(h),
                        _ => false,
                    };
                    let mut n = 0;
                    let mut wrote: Vec<(u16, u32)> = Vec::new();
                    for (k, v, _) in p.input_regs {
                        if keep_fmt && *k == protocol::CFG_KEY_PIXFMT {
                            continue;
                        }
                        send.push((*k, *v));
                        wrote.push((*k, *v));
                        n += 1;
                    }
                    // ★書いた値で Tune欄の表示も更新する。ここを忘れると
                    //   表示が古いまま残り、次に触ったときに古い値が飛ぶ。
                    for (k, v) in wrote {
                        self.set_tune_mirror(k, v);
                    }
                    self.toasts.info(format!("{} の入力設定をボードへ書き込みました ({n}件)", p.label));
                }
            }
        });
        // ボードの伝送形式が**このソースで成立しない**ときだけ言う。
        //
        // ★「プロファイルの値と一致するか」で見てはいけない。伝送形式は
        //   実行時に選べる(上の「伝送形式」コンボ)ので、X68000 RGB を
        //   RGB888 で受けるのは**正当な選択**であって異常ではない。
        //   一致で判定すると、そこで「設定が消えた」と嘘の警告が出る
        //   (2026-09-03 に実際に出た)。
        //
        // 成立するかどうかは形式の**種類**で決まる:
        //   YC8 … コンポジット/S端子の復調には生の8bitが要る。必須
        //   RGB … RGB555 も RGB888 も絵になる。どちらでもよい
        // 電源断でTVPのレジスタが消えた状態は、この「種類が違う」側に出る
        // (コンポジットなのに RGB555 になっていて復調できない)。
        if let Some(p) = profiles::by_key(&self.source_profile) {
            if let (Some(want), Some(have)) = (
                p.pixfmt(),
                self.shared.mode.lock().unwrap().as_ref().map(|m| m.pixfmt),
            ) {
                let is_rgb = |f: u8| matches!(f, protocol::PIXFMT_RGB888
                                                | protocol::PIXFMT_RGB555
                                                | protocol::PIXFMT_RGB565);
                let ok = if want == protocol::PIXFMT_YC8 {
                    have == protocol::PIXFMT_YC8
                } else {
                    is_rgb(have)
                };
                if !ok {
                    ui.colored_label(
                        theme::AMBER,
                        format!(
                            "ボードの伝送形式が {} で、このソース({})では絵になりません。\
                             電源を入れ直して設定が消えた可能性 → 「入力設定を書き込む」",
                            pixfmt_name(have), pixfmt_name(want)
                        ),
                    );
                }
            }
        }
        self.queue_config(send);
    }

    /// 配信用クリーン出力の操作。**配信中いちばん触るものなので上に出す。**
    fn clean_out_ui(&mut self, ui: &mut egui::Ui) {
        ui.horizontal(|ui| {
            // 配信用のクリーン出力。UIもベゼルも無い別ウィンドウを出す。
            // 行のラベルはセクション名と重複するので置かない。
            let mut on = self.clean_open;
            if ui.checkbox(&mut on, "別窓")
                .on_hover_text(
                    "映像だけを描く別ウィンドウを開きます。\n\
                     OBS の「ウィンドウキャプチャ」でこれを掴むと、\n\
                     調整UIやベゼルを写さずに配信ソースにできます。")
                .changed()
            {
                self.clean_open = on;
                self.mark_settings_dirty();
            }
            let mut nodec = self.clean_undecorated;
            if ui.checkbox(&mut nodec, "枠なし")
                .on_hover_text(
                    "タイトルバーを消します。OBS のウィンドウキャプチャは\n\
                     タイトルバーごと取り込むので、既定で消しています。\n\
                     枠なしのときは映像のどこを掴んでもウィンドウを動かせます。")
                .changed()
            {
                self.clean_undecorated = nodec;
                self.mark_settings_dirty();
            }
            let sel = format!("{:.0}x{:.0}", self.clean_size[0], self.clean_size[1]);
            egui::ComboBox::from_id_salt("clean_size")
                .width(110.0)
                .selected_text(sel)
                .show_ui(ui, |ui| {
                    for (label, size) in cleanout::PRESETS {
                        let cur = self.clean_size == *size;
                        if ui.selectable_label(cur, *label).clicked() && !cur {
                            self.clean_size = *size;
                            self.mark_settings_dirty();
                        }
                    }
                })
                .response
                .on_hover_text(
                    "ウィンドウの内寸。**映像の解像度が変わっても変えません**。\n\
                     変えると OBS 側のソースサイズが動いて配信が崩れるためです。\n\
                     中の映像はアスペクトを保って収め、余りは黒で埋めます。");
        });
    }

    /// CONFIG をボードへ送る。未確認の送信として記録し、設定も保存する。
    fn queue_config(&mut self, send: Vec<(u16, u32)>) {
        if send.is_empty() {
            return;
        }
        let now = std::time::Instant::now();
        for (k, v) in &send {
            self.tune_pending.insert(*k, (*v, now));
        }
        self.shared.config_queue.lock().unwrap().extend(send);
        self.mark_settings_dirty();
    }

    /// 音声入力の呼び名。0=RGB端子(D-SUB15) / 1=LINE入力 / 2=S/PDIF。
    fn audio_src_name(src: Option<u8>) -> String {
        match src {
            None => "off".into(),
            Some(0) => "0 RGB".into(),
            Some(1) => "1 LINE".into(),
            Some(2) => "2 S/PDIF".into(),
            Some(n) => n.to_string(),
        }
    }

    /// 音声入力を切り替えて受信スレッドへ要求を出す。
    fn set_audio_source(&mut self, src: Option<u8>) {
        if src == self.audio_source {
            return;
        }
        self.audio_source = src;
        self.mark_settings_dirty();
        *self.shared.audio_request.lock().unwrap() = Some(receiver::AudioRequest {
            device: self.audio_device_sel.clone(),
            source: src,
        });
    }

    /// 映像ソースに対応する音声入力へ合わせる。
    ///
    /// ★**入力を切り替えたら音声も付いてくるべき。** 基板の音声入力は3系統しか
    ///   なく、どれと組になるかは配線で決まっている(RGB端子は X68000 式の
    ///   2列DA-15 で、ピン10/11 に音声が来る)。映像と音声を別々に選ばせるのは、
    ///   その決まっている対応を毎回人間に思い出させているだけだった。
    ///
    ///   対応表は profiles.rs の `audio_src`。「自動」を外せば従来どおり手で選べる。
    fn apply_auto_audio(&mut self) {
        if !self.audio_auto {
            return;
        }
        if let Some(want) = profiles::by_key(&self.source_profile).and_then(|p| p.audio_src) {
            self.set_audio_source(Some(want));
        }
    }

    /// 音声入力の選択。映像ソースと組なので、パネル上部の「入力」に置く。
    fn audio_src_ui(&mut self, ui: &mut egui::Ui) {
        let (mut src, mut auto) = (self.audio_source, self.audio_auto);
        ui.horizontal(|ui| {
            theme::label_col(ui, "音声");
            let label = if auto {
                format!("自動 ({})", Self::audio_src_name(self.audio_source))
            } else {
                Self::audio_src_name(self.audio_source)
            };
            egui::ComboBox::from_id_salt("audio_src")
                .selected_text(label)
                .width(150.0)
                .show_ui(ui, |ui| {
                    if ui.selectable_label(auto, "自動 (映像ソースに従う)").clicked() {
                        auto = true;
                    }
                    for (v, name) in [
                        (None, "off"),
                        (Some(0u8), "0 RGB (D-SUB15)"),
                        (Some(1), "1 LINE in"),
                        (Some(2), "2 S/PDIF"),
                    ] {
                        if ui.selectable_label(!auto && src == v, name).clicked() {
                            auto = false;
                            src = v;
                        }
                    }
                })
                .response
                .on_hover_text(
                    "映像ソースと組になる音声入力。\n\
                     「自動」なら映像を切り替えたときに一緒に切り替わります\n\
                     (RGB端子のピン10/11 に音声が来るのは X68000 式のコネクタだけ\n\
                      なので、それ以外は LINE 入力になります)");
        });
        if auto != self.audio_auto {
            self.audio_auto = auto;
            self.mark_settings_dirty();
            self.apply_auto_audio();
        }
        if !auto {
            self.set_audio_source(src);
        }
    }

    /// S/PDIF(デジタル音声入力)を主系統へ混ぜる。
    ///
    /// ★**主系統の選択とは独立**。ボードは3系統とも常に送ってきている
    ///   (audio_enable_mask の既定が 0b111)ので、混ぜるのは再生側の話でしかない。
    ///   音量を別に持つのは、S/PDIF が別機材の音であることが多く、レベルが
    ///   アナログ入力と揃っている保証が無いため。
    fn spdif_ui(&mut self, ui: &mut egui::Ui) {
        let astats = self.shared.audio.lock().unwrap().clone();
        let (on0, vol0) = (self.spdif_mix, self.spdif_volume);
        // ★**主系統が既に S/PDIF なら混ぜる意味が無い。** 同じ音を自分自身に
        //   重ねることになるし、受信側も主系統で取ってしまうので副系統には
        //   1パケットも回らない。以前はそれを「パケットが来ていません」と
        //   出していて、鳴っているのに壊れているように見えた。
        let main_is_spdif = self.audio_source == Some(receiver::AUX_SOURCE);
        ui.horizontal(|ui| {
            theme::label_col(ui, "S/PDIF");
            ui.add_enabled_ui(!main_is_spdif, |ui| {
                // 主系統が S/PDIF のときは「混ぜない」状態として見せる。
                // 設定そのものは保つので、入力を戻せば元どおりになる。
                let mut on = self.spdif_mix && !main_is_spdif;
                let r = ui.checkbox(&mut on, "混ぜる")
                    .on_hover_text(
                        "光デジタル入力(TOSLINK)を、いま選んでいる音声に重ねて鳴らします。\n\
                         入力の選択とは独立なので、映像ソースを切り替えても外れません")
                    .on_disabled_hover_text(
                        "S/PDIF は音声の入力に選ばれています(自分自身には重ねません)");
                if r.changed() {
                    self.spdif_mix = on;
                    self.mark_settings_dirty();
                }
                ui.add_enabled_ui(on, |ui| {
                    theme::align_sliders(ui);
                    ui.add(egui::Slider::new(&mut self.spdif_volume, 0.0..=1.5)
                           .show_value(false))
                        .on_hover_text("S/PDIF だけの音量(主系統とは別)");
                    ui.monospace(format!("{:3.0}%", self.spdif_volume * 100.0));
                });
            });
        });
        // ★**混ぜていなくても状態は見せる。** S/PDIF を主系統に選んでいるときも
        //   「いま何Hzで来ていて、詰まっていないか」は同じだけ知りたい。
        //   どちらの系統で鳴っているかで、見るべき統計が入れ替わるだけ。
        if self.show_advanced && (self.spdif_mix || main_is_spdif) {
            if let Some(a) = &astats {
                use std::sync::atomic::Ordering::Relaxed;
                let rate = if main_is_spdif {
                    a.src_rate.load(Relaxed)
                } else {
                    a.aux_rate.load(Relaxed)
                };
                // ★**pkts を必ず出す。** 音が出ないときに「ボードが送っていない」
                //   のか「こちらが鳴らせていない」のかを分ける唯一の手掛かり。
                let (pkts, buffered, underruns) = if main_is_spdif {
                    (a.packets.load(Relaxed), a.buffered.load(Relaxed),
                     a.underruns.load(Relaxed))
                } else {
                    (a.aux_packets.load(Relaxed), a.aux_buffered.load(Relaxed),
                     a.aux_underruns.load(Relaxed))
                };
                if rate > 0 {
                    theme::kv(ui, "", format!(
                        "{}  buffered {} ms  underruns {}  pkts {pkts}",
                        audio::describe_rate(rate as u32),
                        buffered * 1000 / a.device_rate.load(Relaxed).max(1),
                        underruns));
                } else if pkts > 0 {
                    theme::kv(ui, "", format!("レート未確定  pkts {pkts}"));
                } else {
                    ui.weak("S/PDIF のパケットが来ていません(pkts 0)");
                }
            }
        }
        if self.spdif_mix != on0 || self.spdif_volume != vol0 {
            self.mark_settings_dirty();
        }
        // ★再生器ではなく Shared 側へ書く。再生器は作り直されるので、そちらに
        //   書くと出力デバイスや入力を切り替えた瞬間に設定が消える。
        self.shared.aux.set(self.spdif_mix, self.spdif_volume);
    }

    /// 音量。よく触るのでパネル上部に置く。
    fn volume_ui(&mut self, ui: &mut egui::Ui) {
        let astats = self.shared.audio.lock().unwrap().clone();
        // 音量。ミュートは値を保持したままゲインだけ0にする
        let (vol0, mute0) = (self.audio_volume, self.audio_muted);
        ui.horizontal(|ui| {
            theme::label_col(ui, "音量");
            let icon = if self.audio_muted { "🔇" } else { "🔊" };
            if ui.button(icon).on_hover_text("mute").clicked() {
                self.audio_muted = !self.audio_muted;
            }
            ui.spacing_mut().slider_width = 150.0;
            ui.add(
                egui::Slider::new(&mut self.audio_volume, 0.0..=1.5)
                    .show_value(false),
            );
            ui.monospace(format!("{:3.0}%", self.audio_volume * 100.0));
        });
        if self.audio_volume != vol0 || self.audio_muted != mute0 {
            self.mark_settings_dirty();
        }
        if let Some(a) = &astats {
            let g = if self.audio_muted { 0.0 } else { self.audio_volume };
            audio::AudioPlayer::set_gain(a, g);
        }

    }

    fn audio_ui(&mut self, ui: &mut egui::Ui) {
        use std::sync::atomic::Ordering::Relaxed;
        let now = self.shared.audio_now.lock().unwrap().clone();
        let astats = self.shared.audio.lock().unwrap().clone();

        let mut request: Option<receiver::AudioRequest> = None;


        // 出力デバイス
        let mut dev = self.audio_device_sel.clone();
        ui.horizontal(|ui| {
            ui.label("out");
            let sel_text = dev.clone().unwrap_or_else(|| "(system default)".to_string());
            egui::ComboBox::from_id_salt("audio_dev")
                .selected_text(sel_text)
                .width(180.0)
                .show_ui(ui, |ui| {
                    ui.selectable_value(&mut dev, None, "(system default)");
                    for d in &self.audio_devices {
                        ui.selectable_value(&mut dev, Some(d.clone()), d);
                    }
                });
            if ui.small_button("⟳").on_hover_text("rescan devices").clicked() {
                self.audio_devices = audio::output_devices();
            }
        });
        if dev != self.audio_device_sel {
            self.audio_device_sel = dev.clone();
            self.mark_settings_dirty();
            request = Some(receiver::AudioRequest { device: dev, source: self.audio_source });
        }

        if let Some(req) = request {
            *self.shared.audio_request.lock().unwrap() = Some(req);
        }

        match astats {
            Some(a) => {
                let rate = a.device_rate.load(Relaxed).max(1);
                ui.monospace(format!(
                    "{}  {} Hz",
                    if a.playing.load(Relaxed) { "playing" } else { "buffering" },
                    rate
                ));
                if !now.device.is_empty() {
                    if self.show_advanced {
                        ui.monospace(format!("dev {}", now.device));
                    }
                    // ★**選んだデバイスと実際に開いたデバイスが違うことを黙らない。**
                    //   見つからないと既定デバイスへ落ちる仕様なので、ユーザーからは
                    //   「音が鳴らない」としか見えない。実機で起きた(2026-09-06)。
                    //   2秒ごとに開き直しを試みているので、繋ぎ直せば自然に直る。
                    if let Some(w) = now.wanted.as_ref() {
                        if !w.is_empty() && *w != now.device {
                            ui.colored_label(theme::AMBER, format!(
                                "「{w}」を開けないので「{}」で鳴っています。\n\
                                 接続を確認してください(開けるようになれば自動で切り替わります)",
                                now.device));
                        }
                    }
                }
                ui.monospace(format!(
                    "buffered {:.0} ms  pkts {}",
                    a.buffered.load(Relaxed) as f64 * 1000.0 / rate as f64,
                    a.packets.load(Relaxed)
                ));
                ui.monospace(format!(
                    "underruns {}  dropped {}",
                    a.underruns.load(Relaxed),
                    a.dropped.load(Relaxed)
                ));
                // ★**枯渇の原因を分けるための表示。** 「無着」は枯渇した瞬間に
                //   最後の到着から何ms経っていたか。溜め(約80ms)以上なら音声が
                //   届いていない(ネットワーク/受信の停止)、短ければ出力側が一度に
                //   大きく読んだ(cb がそれを示す)。gap max は枯渇に至らなかった
                //   分も含めた到着間隔の最大で、どこまで余裕が削られていたかが分かる。
                let ms = |us: u64| us as f64 / 1000.0;
                let last = a.last_underrun_us.load(Relaxed);
                let mut line = format!(
                    "gap max {:.0} ms  cb max {} f",
                    ms(a.arrival_gap_max_us.load(Relaxed)),
                    a.cb_frames_max.load(Relaxed));
                if last > 0 {
                    let ago = a.now_us().saturating_sub(last) / 1_000_000;
                    line += &format!(
                        "\nlast underrun {}分{}秒前  無着 {:.0} ms",
                        ago / 60, ago % 60,
                        ms(a.last_underrun_gap_us.load(Relaxed)));
                }
                ui.monospace(line);
            }
            None => {
                ui.monospace("stopped");
            }
        }
    }
}

impl Session {
    fn render_params(&self) -> render::Params {
        let m = self.shared.mode.lock().unwrap().clone();
        // 実測した有効映像の外接矩形。MODEの hactive はラインバッファの幅(定数 2048)で
        // 有効映像の幅ではないため、管面の中心と縦の連動にはこの実測値を使う
        // 1ラインが何スロットを占めるか(MODEの mflags bit0 = インターレース)
        let slot_k: u32 = match m.as_ref() {
            Some(m) if m.mflags & 0x0001 != 0 => 1,
            _ => 2,
        };
        // vtotal を平滑する。**262/263 の交互は正常なので、その平均(262.5)を使う。**
        // モードが変わったときだけ即座に飛ばす(追従を待つと一瞬絵が伸びる)。
        // 時定数は**経過時間**で効かせる。ここは描画のたびに呼ばれるが、raw の
        // 出どころ(MODE)は1秒に1〜2回しか更新されないので、フレーム数で減衰させると
        // 同じ値へ収束しきって平均にならない(render.rs の smooth_vtotal 参照)。
        {
            let now = std::time::Instant::now();
            let dt = self
                .vtotal_last_t
                .get()
                .map_or(1.0 / 60.0, |t| now.duration_since(t).as_secs_f32());
            self.vtotal_last_t.set(Some(now));
            let raw = m.as_ref().map_or(0.0, |m| (m.vtotal as u32 * slot_k) as f32);
            let id = m.as_ref().map_or(u16::MAX, |m| m.mode_id as u16);
            let reset = id != self.vtotal_mode_id.get();
            self.vtotal_smooth
                .set(render::smooth_vtotal(self.vtotal_smooth.get(), raw, reset, dt));
            if raw > 0.0 {
                self.vtotal_mode_id.set(id);
            }
        }
        let act = {
            let st = self.shared.stats.lock().unwrap();
            // span_* は「明るい画素が1つでもある行/列」の外接矩形。active_* は
            // 「20%以上の行が明るい列」なので、細い線ばかりの画面ではベタ塗りの
            // ブロックだけに縮む(実機で幅125になった)。管面の幾何は絵の広がりを
            // 知りたいので span_* を使い、無ければ active_* に落とす
            if st.span_w > 64 {
                (st.span_x as u32, st.span_y as u32, st.span_w as u32, st.span_h as u32)
            } else {
                (st.active_x as u32, st.active_y as u32,
                 st.active_w as u32, st.active_h as u32)
            }
        };
        render::Params {
            rotate: self.rotate,
            tube: self.tube_aspect_eff(),
            filter: self.filter,
            htotal: m.as_ref().map_or(0, |m| m.htotal as u32),
            // 行位置は半ライン単位のスロット。1VSYNC周期に何スロット入るかは
            // 織り込みの有無で変わる:
            //   プログレッシブ  1ラインが2スロット      → 2*vtotal
            //   インターレース  折り返して2フィールドが  → vtotal
            //                   交互に入るので1ラインが1スロット
            // これを間違えると縦が2倍に引き伸ばされる(実機で絵が上半分に収まった)。
            vtotal: self.vtotal_smooth.get(),
            // offset_px はライン内の絶対位置で来るので、ここでずらす必要はない。
            // pll_divide を変えても絵が動かないのはこのため(hs_offset は取り込み
            // 窓の設定であって、描画位置とは無関係になった)
            hs_offset: 0,
            vbp: self.tune_vbp.max(0) as u32 * slot_k,
            window: self.window,
            fh_hz: m.as_ref().map_or(0, |m| (m.hfreq_mhz_x1000 / 1000) as u32),
            hactive: m.as_ref().map_or(0, |m| m.hactive as u32),
            vactive: m.as_ref().map_or(0, |m| m.vactive as u32),
            time_based: self.tube_time_based,
            h_size: self.mon[0],
            h_pos: self.mon[1],
            v_size: self.mon[2],
            v_pos: self.mon[3],
            act_x: act.0, act_y: act.1, act_w: act.2, act_h: act.3,
        }
    }

    /// 実行時に調整できるキーの一覧。読み戻しと表示の同期に使う
    const TUNE_KEYS: [u16; 16] = [
        protocol::CFG_KEY_VBP,
        protocol::CFG_KEY_HS_OFFSET,
        protocol::CFG_KEY_PLL_DIVIDE,
        protocol::CFG_KEY_VIDEO_BW,
        protocol::CFG_KEY_PHASE,
        protocol::CFG_KEY_FULL_LINE,
        protocol::CFG_KEY_FRAME_SKIP,
        protocol::CFG_KEY_GAIN_R,
        protocol::CFG_KEY_GAIN_G,
        protocol::CFG_KEY_GAIN_B,
        protocol::CFG_KEY_PIXFMT,
        protocol::CFG_KEY_SOG_THRESH,
        protocol::CFG_KEY_SYNC_CTL2,
        protocol::CFG_KEY_SOG_VTH,
        protocol::CFG_KEY_FIELD_INVERT,
        protocol::CFG_KEY_NO_RAW_PHASE,
    ];

    /// ボードの現在値を表示へ反映する。
    ///
    /// 読み戻さないと表示と実体が食い違う。設定はボードの電源で
    /// 消え、Viewerの保存値とは別々に動くため)。送信パケットが落ちたときも
    /// ずれるので、応答で確認できた値を正としてUIを合わせる。
    /// いまの入力モードのキー。同じ31kHzでも 768x512 と 256x256 は同期信号が
    /// 同一なので、htotal(= pll_divide)まで含めないと区別できない。
    fn current_mode_key(&self) -> Option<String> {
        let m = self.shared.mode.lock().unwrap().clone()?;
        if m.htotal == 0 || m.vtotal == 0 || m.hfreq_mhz_x1000 == 0 {
            return None;
        }
        let fh = (m.hfreq_mhz_x1000 as f64 / 1000.0 / 100.0).round() as u32;
        Some(format!("{fh}_{}_{}", m.vtotal, m.htotal))
    }

    /// モードが変わったら、いまの切り出し・回転を旧モードへ保存し、
    /// 新モードの値を復元する。未知のモードでは切り出しを解除する
    /// (別モードの座標で切り出すと絵が切れるため)。
    fn follow_mode(&mut self) {
        let Some(key) = self.current_mode_key() else { return };
        if key == self.mode_key {
            self.pending_mode = None;
            return;
        }
        // ★**新しいモードが続いていることを確かめてから追従する。**
        //
        //   モードキーは測定値(fh / vtotal / htotal)から作るので、入力の同期が
        //   一瞬乱れるだけで別のモードに見える。そのまま追従すると
        //   「未知のモード → 切り出しと回転をリセット」で**絵が飛ぶ**。
        //   実測では乱れは1秒ほど続いたので、それより長く待つ。
        //
        //   ★**遅れても実害は小さい。** 映像そのものは MODE パケットに即座に
        //     追従する。ここで遅れるのは切り出し・回転・位相の復元だけ。
        const SETTLE: std::time::Duration = std::time::Duration::from_secs(2);
        match &self.pending_mode {
            Some((k, since)) if *k == key => {
                if since.elapsed() < SETTLE {
                    return;
                }
            }
            _ => {
                self.pending_mode = Some((key, std::time::Instant::now()));
                return;
            }
        }
        self.pending_mode = None;
        if !self.mode_key.is_empty() {
            let old = self.mode_key.clone();
            self.modes.insert(old, [self.crop[0], self.crop[1], self.crop[2],
                                    self.crop[3], self.rotate, self.tune_phase as u32]);
        }
        match self.modes.get(&key) {
            Some(v) => {
                self.crop = [v[0], v[1], v[2], v[3]];
                self.rotate = v[4].min(3);
                // 位相はモードごとに最適値が違うので、復元したらボードへ送り直す
                let ph = (v[5].min(31)) as u8;
                if ph != self.tune_phase {
                    self.tune_phase = ph;
                    self.send_cfg(protocol::CFG_KEY_PHASE, ph as u32);
                }
            }
            None => {
                self.crop = [0; 4];
                self.rotate = 0;
            }
        }
        self.mode_key = key;
        self.mark_settings_dirty();
        // ★**絵の大きさが変わったときだけ合わせ直す。** 同期がふらついただけで
        //   窓を動かさない(乱れるたびに窓が動くのは実害が大きい)。
        if self.display_sig() != self.fitted_sig {
            self.want_fit = true;
        }
    }

    /// 絵の見た目の大きさを決める要素だけを拾った署名。
    fn display_sig(&self) -> Option<(u16, u16, u32, [u32; 4])> {
        let m = self.shared.mode.lock().unwrap();
        m.as_ref().map(|m| (m.hactive, m.vactive, self.rotate, self.crop))
    }

    /// pll_divide を変える。hs_offset を同じ比で追従させて絵が動かないようにする。
    ///
    /// サンプル k の水平位置は (hs_offset + k)/htotal で htotal = pll_divide。
    /// k は pll_divide に比例して増えるので式としては時間ベースだが、hs_offset は
    /// サンプル単位なので固定のままだと取り込み開始「時刻」が変わり、絵が横へ跳ぶ。
    /// pll_divide はドットクロック再生のためのもので描画位置とは無関係でなければ
    /// ならない。いまは hs_offset を常に0で運用しているので実質的な効果は無いが、
    /// 0以外にしたときに壊れないようにしておく。
    /// pll_divide を Viewer 側が動かしてよいか。
    ///
    /// **YC8(生8bit)のときは動かしてはいけない。** コンポジット/S端子の
    /// サンプルレートは規格で決まっていて(NTSC 8fsc = 227.5×8 = 1820
    /// サンプル/ライン)、実測で探すものではない。8サンプル/周期という
    /// 前提が崩れると副搬送波の直交復調が成立しなくなる。
    ///
    /// 実際に踏んだ: コンポジットで 1820 を入れた直後に Viewer が
    /// **帯域ごとの保存値と自動調整の初期値(2304)で上書き**し、
    /// 10.13サンプル/周期になっていた(絵は出るので気づきにくい)。
    ///
    /// 入力方式ごとの値は `retrocastx.videoin` が入れる。Viewer は触らない。
    fn pll_locked_by_format(&self) -> bool {
        // ★**ボードが返す pixfmt だけで判定してはいけない。** 見た瞬間のボードは、
        //   こちらが書いたばかりの形式をまだ反映していないことがある。
        //
        //   実機で踏んだ(2026-09-06、コンポジット)。電源投入直後のボードは
        //   RGB555 を流していて、同じフレームの中で
        //     1. autowrite_input_regs が pll_divide=1820 と pixfmt=YC8 を送る
        //     2. follow_band が「15kHz帯の保存値」を復元する。**15kHz帯は MSX と
        //        共有**なので 1368 が入る。MODE はまだ RGB555 なのでここが素通しで、
        //        1820 を上書きしてしまう
        //     3. MODE が YC8 になった頃には誰も 1820 に戻さない
        //   結果、副搬送波が 8サンプル/周期にならず**復調が未ロックで白黒**になった。
        //   「一度モードを切り替えて戻すと直る」のは、そのときは既に YC8 だから。
        //
        //   なので**選んでいる映像ソースが YC8 を要求するか**も見る。こちらは
        //   ボードの応答を待たずに決まるので、書き込みと復元の順序に依存しない。
        if profiles::by_key(&self.source_profile)
            .and_then(|p| p.pixfmt())
            .is_some_and(|f| f == protocol::PIXFMT_YC8)
        {
            return true;
        }
        matches!(self.shared.mode.lock().unwrap().as_ref(),
                 Some(m) if m.pixfmt == protocol::PIXFMT_YC8)
    }

    fn set_pll(&mut self, new: u32) {
        // 自動でここへ来る経路(帯域切替の復元など)を1か所で止める。
        // 手動の pll_div 欄は別経路なので、逃げ道としては残る。
        if self.pll_locked_by_format() {
            return;
        }
        let old = self.tune_pll_divide.max(1) as f32;
        let hs = ((self.tune_hs_offset as f32 * (new as f32 / old)).round() as i32)
            .clamp(0, (new / 2) as i32);
        self.tune_pll_divide = new as i32;
        self.send_cfg(protocol::CFG_KEY_PLL_DIVIDE, new);
        if hs != self.tune_hs_offset {
            self.tune_hs_offset = hs;
            self.send_cfg(protocol::CFG_KEY_HS_OFFSET, hs as u32);
        }
    }

    /// CONFIGを1つ送る。UIの外(モード追従など)から使う
    fn send_cfg(&mut self, key: u16, val: u32) {
        self.tune_pending.insert(key, (val, std::time::Instant::now()));
        self.shared.config_queue.lock().unwrap().push((key, val));
        self.mark_settings_dirty();
    }

    /// Tune欄の表示値(ボードの値のミラー)を1キーぶん更新する。
    ///
    /// ★**表示と実体がずれると、次に触ったときに古い値がボードへ飛ぶ。**
    ///   映像ソースを選ぶと `input_regs` が伝送形式や細ゲインを書き換えるのに、
    ///   ここを更新していなかったので Tune欄は起動時の値のままだった
    ///   (`sync_tune_from_board` は同期が済むと二度と反映しない)。実機で
    ///   S端子プロファイルを書いた直後に「伝送形式 RGB555 / 細ゲイン 64,61,57」
    ///   = X68000 の値が表示されたままになっていた(2026-09-05)。この状態で
    ///   伝送形式のコンボや gain の send を押すと、画面に見えている古い値が
    ///   そのまま送られて**絵が消える**。書いた側が必ずここを呼ぶこと。
    fn set_tune_mirror(&mut self, key: u16, val: u32) {
        match key {
            protocol::CFG_KEY_VBP => self.tune_vbp = val as i32,
            protocol::CFG_KEY_HS_OFFSET => self.tune_hs_offset = val as i32,
            protocol::CFG_KEY_PLL_DIVIDE => self.tune_pll_divide = val as i32,
            protocol::CFG_KEY_VIDEO_BW => self.tune_video_bw = val as u8,
            protocol::CFG_KEY_FULL_LINE => self.tune_full_line = val != 0,
            protocol::CFG_KEY_FRAME_SKIP => self.tune_frame_skip = val as u8,
            protocol::CFG_KEY_PHASE => self.tune_phase = (val as u8).min(31),
            protocol::CFG_KEY_PIXFMT => self.tune_pixfmt = val as i32,
            protocol::CFG_KEY_GAIN_R => self.tune_gain_r = val as i32,
            protocol::CFG_KEY_GAIN_G => self.tune_gain_g = val as i32,
            protocol::CFG_KEY_GAIN_B => self.tune_gain_b = val as i32,
            protocol::CFG_KEY_SOG_THRESH => self.tune_sog_thresh = (val as i32).min(31),
            protocol::CFG_KEY_SYNC_CTL2 => self.tune_sync_ctl2 = (val as i32).min(255),
            protocol::CFG_KEY_SOG_VTH => self.tune_sog_vth = (val as i32).min(65535),
            protocol::CFG_KEY_FIELD_INVERT => self.tune_field_invert = (val != 0) as i32,
            protocol::CFG_KEY_NO_RAW_PHASE => self.tune_no_raw_phase = (val != 0) as i32,
            _ => {}
        }
    }

    /// ボードの伝送形式が映像ソースと食い違っていたら `input_regs` を自動で書く。
    ///
    /// ★**TVPのレジスタはボードの電源で消える。** ビットストリームはフラッシュに
    ///   残るが、入力MUX・同期の取り方・クランプ・ゲイン・伝送形式は毎回 CONFIG で
    ///   入れ直す必要がある。Viewer は映像ソースを**選び直したとき**にしか書かないので、
    ///   前回の選択が保存されたまま起動すると誰も書かず、**選んであるのに映らない**
    ///   状態になる(2026-09-05 に実機で踏んだ。コンポジットへ切り替えてから
    ///   S端子へ戻すと「変化」になって書かれ、直ったように見えるので分かりにくい)。
    ///
    /// 条件は既にある警告と同じ「伝送形式の**種類**が成立しない」だけにしてある:
    ///
    ///   - YC8 が要るソース(コンポジット/S端子)なのにボードが RGB を流している
    ///   - RGB のソースなのにボードが YC8 を流している
    ///
    /// **値の一致では判定しない。** 伝送形式は実行時に選べるので、X68000 RGB を
    /// RGB888 で見るのは正当な選択であって異常ではない。ここで一致を要求すると、
    /// 起動のたびに手で選んだ形式を RGB555 へ戻してしまう。
    ///
    /// 掛け金(`input_regs_autowritten`)は食い違いが解消したら外れるので、
    /// **ボードを入れ直すたびに1回だけ**書く。書いても直らない場合
    /// (パケットが落ちた等)は自動では追わない — 既存の警告と「入力設定を書き込む」が残る。
    fn autowrite_input_regs(&mut self) {
        let Some(p) = profiles::by_key(&self.source_profile) else {
            return;
        };
        if p.input_regs.is_empty() {
            return;
        }
        let Some(want) = p.pixfmt() else {
            return;
        };
        // MODE が来ていないうちは判定できない。ボードが落ちたら掛け金も外す
        // (次に上がってきたときが「新しい電源投入」なので、また1回書く)
        let Some(have) = self.shared.mode.lock().unwrap().as_ref().map(|m| m.pixfmt) else {
            self.input_regs_autowritten = false;
            return;
        };
        let is_rgb = |f: u8| {
            matches!(f, protocol::PIXFMT_RGB888
                        | protocol::PIXFMT_RGB555
                        | protocol::PIXFMT_RGB565)
        };
        let ok = if want == protocol::PIXFMT_YC8 {
            have == protocol::PIXFMT_YC8
        } else {
            is_rgb(have)
        };
        if ok {
            self.input_regs_autowritten = false;
            return;
        }
        if self.input_regs_autowritten {
            return;
        }
        self.input_regs_autowritten = true;
        for (k, v, _) in p.input_regs {
            self.send_cfg(*k, *v);
            self.set_tune_mirror(*k, *v);
        }
        // ★頼まれていないのにボードのレジスタを書き換えた。黙ってやるのは
        //   良くないので必ず伝える(ただし数秒で消す。状態ではなく出来事なので)
        self.toasts.notice(format!(
            "伝送形式が食い違っていたため、{} の入力設定を自動で書き込みました ({}件)",
            p.label, p.input_regs.len()));
    }

    /// いまの有効映像が何µsか。管面の掃引時間を決める基準になる
    fn active_us(&self) -> Option<f32> {
        let aw = {
            let st = self.shared.stats.lock().unwrap();
            if st.span_w > 64 { st.span_w as f32 } else { st.active_w as f32 }
        };
        let m = self.shared.mode.lock().unwrap().clone()?;
        let fh_khz = m.hfreq_mhz_x1000 as f32 / 1_000_000.0;
        if aw <= 0.0 || fh_khz <= 1.0 || m.htotal == 0 {
            return None;
        }
        Some(aw / m.htotal as f32 * (1000.0 / fh_khz))
    }

    /// H-PLL制御(TVPレジスタ03h)の値をモードから計算する。
    ///
    /// データシート 03h の定義:
    ///   VCO 00 = Ultra low (KVCO  75)  PCLK < 36 MHz
    ///       01 = Low       (KVCO  85)  36 ≤ PCLK < 70
    ///       10 = Medium    (KVCO 150)  70 ≤ PCLK < 135   ← 既定(A8h)
    ///       11 = High      (KVCO 200)  135 ≤ PCLK ≤ 165
    ///   ICP = 40 × KVCO / (pixels per line)
    ///
    /// データシートは「VCOレンジ制御の目的はノイズ性能の改善」と書いている。
    /// レンジ外で動かすと位相ノイズが増え、ラインごとにサンプリング位相が揺れて
    /// 行単位の横ずれになる(既定のA8h=Mediumを全モードに使っていて実機で発生)。
    /// X68000は全モード PCLK < 36MHz なので Ultra low が正しい。
    ///
    /// 計算式が Table 4 と一致することは確認済み(720×480p: 27MHz/858 → ICP 3.50
    /// → 18h)。
    /// 想定される最大のライン周波数。VCOレンジを決めるときの最悪ケースに使う。
    /// レトロ機の水平周波数は 15〜32kHz の範囲なので、上端を取れば
    /// 「PLLが作る必要のある最大周波数」を fH の測定値に依存せず見積もれる。
    const FH_MAX_HZ: f64 = 32_000.0;

    fn pll_ctl_for(pclk_hz: f64, pix_per_line: u32) -> u8 {
        let (vco, kvco) = if pclk_hz < 36.0e6 {
            (0u8, 75.0)
        } else if pclk_hz < 70.0e6 {
            (1, 85.0)
        } else if pclk_hz < 135.0e6 {
            (2, 150.0)
        } else {
            (3, 200.0)
        };
        let icp = (40.0 * kvco / pix_per_line.max(1) as f64).round().clamp(0.0, 7.0) as u8;
        (vco << 6) | (icp << 3)
    }

    /// fH[kHz] を呼称の帯域へ分類する。
    ///
    /// 丸めると 24.698kHz が 25 になって呼称とずれる。マルチスキャンモニタの
    /// インジケータと同じ 15 / 24 / 31 に寄せる。範囲外は丸めた値をそのまま使う。
    fn band_of(fh_khz: f32) -> u32 {
        if fh_khz < 20.0 {
            15
        } else if fh_khz < 28.0 {
            24
        } else if fh_khz < 40.0 {
            31
        } else {
            fh_khz.round() as u32
        }
    }

    /// 描画に使う管面の縦横比。
    ///
    /// コンポジット/S端子(YC8)は**規格で画素の形が決まっている**ので、管面の
    /// 設定(4:3 など)ではなく、いま映している窓の大きさから求める。基準は
    /// 720サンプル(BT.601、53.33µs) × 480ライン = 4:3。ビデオデッキの HDMI 出力も
    /// この比で、50.9µs × 480ライン を 1.274 で出していた(実測)。管面の設定をそのまま
    /// 使うと、窓を詰めたぶん横に伸びる(格子の升目が横長になる)。
    fn tube_aspect_eff(&self) -> f32 {
        if self.mon_key != MON_KEY_NTSC || !self.tube_time_based {
            return self.tube_aspect;
        }
        let h_us = self.mon[0].max(0.01) * NTSC_LINE_US;
        let lines = self.mon[2].max(0.01) * NTSC_LINES;
        4.0 / 3.0 * (h_us / 53.333) * (480.0 / lines)
    }

    /// 周波数帯が変わったら、いまの管面設定を旧帯域へ保存し、新帯域の値を復元する。
    ///
    /// 実機のマルチスキャンモニタは周波数帯ごとに走査速度を切り替えて管面いっぱいに
    /// 走らせる。掃引時間を絶対時間で共通にすると、15kHz(有効52.7µs)に合わせた
    /// 管面では31kHz(同22.1µs)が42%の大きさになってしまう。帯域ごとに持てば、
    /// 同じ帯域内のモードは同じ大きさで表示される(31kHzの512x512と768x512は
    /// 有効時間がどちらも22.1µsで実際に一致する)。
    fn follow_band(&mut self) {
        let khz = {
            let m = self.shared.mode.lock().unwrap().clone();
            match m {
                Some(m) if m.hfreq_mhz_x1000 > 1_000_000 => {
                    Self::band_of(m.hfreq_mhz_x1000 as f32 / 1_000_000.0)
                }
                _ => return,
            }
        };
        // ★コンポジット/S端子は管面を帯域と別に持つ。同じ15kHz帯でも、RGB(MSX・
        //   X68000)の管面はモニタに合わせて回すつまみで、NTSCの窓は規格と
        //   ビデオデッキで決まる。共用すると片方を合わせるともう片方がずれる。
        let mk = if self.pll_locked_by_format() { MON_KEY_NTSC } else { khz };
        if mk != self.mon_key {
            if self.mon_key > 0 {
                self.mon_bands.insert(self.mon_key, self.mon);
            }
            let default = if mk == MON_KEY_NTSC { MON_NTSC } else { [1.0, 0.0, 1.0, 0.0] };
            self.mon = self.mon_bands.get(&mk).copied().unwrap_or(default);
            self.mon_key = mk;
            self.mark_settings_dirty();
            self.want_fit = true;
        }
        if khz == self.band_khz {
            return;
        }
        if self.band_khz > 0 {
            let old = self.band_khz;
            self.band_pll.insert(old, [self.tune_pll_divide.max(0) as u32,
                                       self.tune_phase as u32]);
        }
        // 帯域ごとの pll_divide / 位相を復元してボードへ送る。
        // pll_divide はモードごとに正解が違い、位相も帯域ごとに最適値が変わるので、
        // 1つだけ持つと帯域を切り替えるたびに合わせ直しになる。
        if let Some(v) = self.band_pll.get(&khz).copied() {
            let pll = (v[0] as i32).clamp(200, 2304);
            if pll != self.tune_pll_divide {
                self.set_pll(pll as u32);
            }
            let ph = (v[1].min(31)) as u8;
            if ph != self.tune_phase {
                self.tune_phase = ph;
                self.send_cfg(protocol::CFG_KEY_PHASE, ph as u32);
            }
        }
        // 未知の帯域の管面は「1周期まるごとが管面に出る」から始める(上で復元済み)。
        // 管面の横幅は 1/fH そのものなので、これで必ず全体が収まる。あとは実機の
        // モニタに合わせて H幅/V幅を1未満へ詰めていけばよい(帰線の間ビームは
        // 戻っているので、実際のCRTは 0.85〜0.95 あたりが近い)。
        self.band_khz = khz;
        // H-PLLのVCOレンジ/チャージポンプはピクセルクロックとpixels per lineで
        // 決まるので、モードが変わったら計算して送り直す
        // VCOレンジは「報告されたドットクロック」ではなく pll_divide から決める。
        //
        // 報告値は誤ったロックの結果でもあり得るので、それを根拠にすると誤りが
        // 固定される。実機で発生: pll_div 1182 に対しレンジを Ultra low(<36MHz)に
        // 設定したため、必要な 37.2MHz を出せずPLLが半分のライン周期にロックし、
        // その状態が自己維持した。pll_divide × 想定最大fH で見積もれば、レンジが
        // 足りなくなることはない(少し高めのレンジになりノイズ性能を僅かに譲るが、
        // 誤ロックより害が小さい)。
        let ht = self.tune_pll_divide.max(1) as u32;
        let v = Self::pll_ctl_for(ht as f64 * Self::FH_MAX_HZ, ht);
        self.send_cfg(protocol::CFG_KEY_PLL_CTL, v as u32);
        self.mark_settings_dirty();
        self.want_fit = true;
    }

    fn sync_tune_from_board(&mut self) {
        // 取り込みは起動時の1回だけにする。毎フレーム反映すると、手で入力した値が
        // send を押す前にボードの値へ戻されてしまう(未送信の変更は pending に
        // 入らないため)。ずれ直したときは「読む」で取り直せる。
        if self.tune_synced {
            return;
        }
        let now = std::time::Instant::now();
        let state = self.shared.config_state.lock().unwrap().clone();
        // 未取得のキーがあるうちは定期的に問い合わせる
        if Self::TUNE_KEYS.iter().any(|k| !state.contains_key(k))
            && self.tune_get_at.map_or(true, |t| now >= t)
        {
            self.tune_get_at = Some(now + std::time::Duration::from_secs(2));
            self.shared
                .config_get_queue
                .lock()
                .unwrap()
                .extend(Self::TUNE_KEYS);
        }
        for (key, val) in &state {
            let (key, val) = (*key, *val);
            // 送信直後は応答が返るまで自分の値を優先する。応答が一致したら解除、
            // 一定時間返らなければ諦めてボードの値に合わせる(送信が落ちた場合)
            if let Some((want, at)) = self.tune_pending.get(&key) {
                if *want == val {
                    self.tune_pending.remove(&key);
                } else if at.elapsed() < std::time::Duration::from_millis(1500) {
                    continue;
                } else {
                    self.tune_pending.remove(&key);
                }
            }
            self.set_tune_mirror(key, val);
        }
        // 完了判定は「いま適用したのと同じスナップショット」で行う。config_state を
        // 取り直すと、スナップショット後に届いた応答を適用しないまま完了扱いになり、
        // 以後この関数が早期returnして二度と読まれない(hs_offset だけ古い値のまま
        // 残る、という形で実機で発覚した)。
        if Self::TUNE_KEYS.iter().all(|k| state.contains_key(k)) {
            self.tune_synced = true;
        }
    }

    /// マルチスキャンモニタの周波数インジケータ。いま同期している帯域が点灯する。
    ///
    /// 実機のモニタは 15/24/31kHz のどれで同期しているかをLEDで示していた。
    /// 帯域は管面のプリセットを選ぶ単位でもあるので、いまどれなのかが常に
    /// 見えている方が分かりやすい。
    fn band_leds(&self, ui: &mut egui::Ui) {
        const BANDS: [u32; 3] = [15, 24, 31];
        ui.horizontal(|ui| {
            for b in BANDS {
                let on = self.band_khz == b;
                let (rect, _) = ui.allocate_exact_size(
                    egui::vec2(52.0, 18.0), egui::Sense::hover());
                let p = ui.painter();
                // 消灯時も枠は見えるようにして、何段あるかが分かるようにする
                let (fill, text) = if on {
                    // ★点灯色はアクセントに揃える。緑のままだと見出しの teal と
                    //   競合して、どちらが「いま効いているもの」か読めなくなる
                    (theme::ACCENT, egui::Color32::BLACK)
                } else {
                    (egui::Color32::from_rgb(38, 40, 44), egui::Color32::from_gray(110))
                };
                p.rect_filled(rect, 3.0, fill);
                p.rect_stroke(rect, 3.0, egui::Stroke::new(1.0,
                              egui::Color32::from_gray(70)), egui::StrokeKind::Inside);
                p.text(rect.center(), egui::Align2::CENTER_CENTER,
                       format!("{b}kHz"), egui::FontId::monospace(11.0), text);
            }
            // 呼称の帯域に当てはまらない周波数(他機種など)はそのまま出す
            if self.band_khz > 0 && !BANDS.contains(&self.band_khz) {
                ui.monospace(format!("{}kHz", self.band_khz));
            }
            if self.band_khz == 0 {
                ui.weak("同期なし");
            }
        });
    }

    /// TVPが許す pll_divide の下限(8の倍数に切り上げ)。
    ///
    /// TVP7002のピクセルクロックは 12MHz 未満だと動作が保証されない(データシート)。
    /// 実測でも 11.25MHz から崩れ始め、9.72MHz では白の青/赤比が上下で0.43違った。
    /// X68000の15kHzモードは本来の htotal が 608(9.72MHz)なので、**1:1で
    /// サンプリングできない**。下限を満たす最小の整数倍(2倍=1216)を使う。
    /// 整数倍なら位相ロックするのでドット間の混ざりは起きず、各ドットが2サンプルに
    /// なるだけで済む。
    fn pll_min_hw(&self) -> u32 {
        match self.shared.mode.lock().unwrap().as_ref() {
            Some(m) if m.hfreq_mhz_x1000 > 0 => {
                let fh = m.hfreq_mhz_x1000 as f64 / 1000.0;
                let v = (12.0e6 / fh).ceil() as u32;
                ((v + 7) / 8 * 8).clamp(AUTO_PLL_MIN, AUTO_PLL_MAX)
            }
            _ => AUTO_PLL_MIN,
        }
    }

    /// フルスキャンを開始する。上限まで過剰サンプルするところから始める
    fn auto_start(&mut self) {
        // YC8 は pll_divide が規格で決まっているので探索してはいけない
        if self.pll_locked_by_format() {
            self.auto_done = Some("YC8では pll_divide は規格値。自動調整しません".into());
            return;
        }
        self.send_cfg(protocol::CFG_KEY_PLL_DIVIDE, AUTO_PLL_MAX);
        self.tune_pll_divide = AUTO_PLL_MAX as i32;
        self.auto = Some(AutoTune {
            mode: AutoMode::Full,
            phase: AutoPhase::Oversample,
            wait_until: std::time::Instant::now() + std::time::Duration::from_millis(1800),
            base_n: self.shared.stats.lock().unwrap().tune_n,
            note: "過剰サンプル中...".into(),
            worst: 0.0,
            attempt: 0,
            over: 1,
            report: String::new(),
        });
    }

    /// いま選んでいるプロファイル(「自動」なら fH から推定したもの)で、
    /// この fH に対して実在しうるモードの一覧。簡易スキャンの探索空間。
    ///
    /// **機種固有の分岐はここにも無い。** プロファイルの表と fH だけで決まる。
    fn scan_candidates(&self) -> Vec<profiles::ScanPoint> {
        let fh_hz = self
            .shared
            .mode
            .lock()
            .unwrap()
            .as_ref()
            .map(|m| m.hfreq_mhz_x1000 as f64 / 1000.0)
            .unwrap_or(0.0);
        if !(fh_hz > 0.0) {
            return Vec::new();
        }
        let p = if self.source_profile.is_empty() {
            profiles::best_over_all(fh_hz).map(|(p, _)| p)
        } else {
            profiles::by_key(&self.source_profile)
        };
        p.map(|p| profiles::scan_candidates(p, fh_hz))
            .unwrap_or_default()
    }

    /// 簡易スキャンを開始する。
    ///
    /// **htotal のいちばん大きい候補から始めて、下へしか動かない。** これが安全側:
    /// 真値より大きい pll_divide は整数倍の過剰サンプルなので情報は落ちない
    /// (絵が眠くなるだけ)が、小さい値はドットを飛ばすので絵が壊れる。
    /// 降りるには「位相を振っても鮮鋭度が変わらない」= 過剰サンプルという
    /// 積極的な証拠を要求する。証拠が無ければその場に留まる。
    fn auto_start_quick(&mut self) {
        if self.pll_locked_by_format() {
            self.auto_done = Some("YC8では pll_divide は規格値。自動調整しません".into());
            return;
        }
        let mut cands = self.scan_candidates();
        if cands.is_empty() {
            self.auto_done =
                Some("この fH を説明できる候補がありません。フルスキャンを使ってください".into());
            return;
        }
        // htotal の降順に並べ替える。これが測る順番(=降りる順番)
        cands.sort_by(|a, b| b.htotal.cmp(&a.htotal));
        // 設定値が同じ点は測っても区別できない(31.5kHzの htotal 736 と 368 は
        // どちらも pll 736)。htotal 降順なので、残るのは大きい htotal の解釈
        let mut ladder: Vec<profiles::ScanPoint> = Vec::new();
        for c in &cands {
            if !ladder.iter().any(|l| l.pll_divide == c.pll_divide) {
                ladder.push(c.clone());
            }
        }
        let first = ladder[0].clone();
        let n = ladder.len();
        self.send_cfg(protocol::CFG_KEY_PLL_DIVIDE, first.pll_divide);
        self.tune_pll_divide = first.pll_divide as i32;
        self.send_cfg(protocol::CFG_KEY_PHASE, 0);
        self.tune_phase = 0;
        self.auto = Some(AutoTune {
            mode: AutoMode::Quick { ladder, probes: Vec::new() },
            phase: AutoPhase::QuickProbe { i: 0, k: 0, best: (0, 0.0), worst: f32::MAX },
            wait_until: std::time::Instant::now() + std::time::Duration::from_millis(1800),
            base_n: self.shared.stats.lock().unwrap().tune_n,
            note: if n > 1 {
                format!("候補 {n}通り。pll {} から位相を振ります...", first.pll_divide)
            } else {
                format!("候補は pll {} だけ。位相を振ります...", first.pll_divide)
            },
            worst: 0.0,
            attempt: 0,
            over: first.oversample,
            report: String::new(),
        });
    }

    /// 位相を1刻みで詰める段へ入る。`ph` を中心に±2
    fn auto_enter_phase_fine(&mut self, ph: u8, sharp: f32, note: String) {
        let list: Vec<u8> = (0..5)
            .map(|k| ((ph as i32 + k - 2).rem_euclid(32)) as u8)
            .collect();
        let head = list[0];
        if let Some(a) = self.auto.as_mut() {
            a.phase = AutoPhase::PhaseFine { list, i: 0, best: (ph, sharp) };
        }
        self.auto_next(protocol::CFG_KEY_PHASE, head as u32, note, 600);
    }

    /// 新しい測定が来ていれば (鋭さ, 占有率) を返す。まだなら None
    fn auto_measure(&self) -> Option<(f32, f32)> {
        let a = self.auto.as_ref()?;
        if std::time::Instant::now() < a.wait_until {
            return None;
        }
        let st = self.shared.stats.lock().unwrap();
        // 待ち終了後の測定を2回以上見てから採る(境界の1枚は前の設定の絵かもしれない)
        if st.tune_n < a.base_n + 2 || st.sharp_h <= 0.0 {
            return None;
        }
        Some((st.sharp_h, st.occ_h))
    }

    /// 次の測定点へ進む
    fn auto_next(&mut self, key: u16, val: u32, note: String, settle_ms: u64) {
        self.send_cfg(key, val);
        match key {
            protocol::CFG_KEY_PLL_DIVIDE => self.tune_pll_divide = val as i32,
            protocol::CFG_KEY_PHASE => self.tune_phase = val as u8,
            _ => {}
        }
        let base = self.shared.stats.lock().unwrap().tune_n;
        if let Some(a) = self.auto.as_mut() {
            a.wait_until = std::time::Instant::now()
                + std::time::Duration::from_millis(settle_ms);
            a.base_n = base;
            a.note = note;
        }
    }

    /// 推定値の周りを8の倍数で局所探索する段へ入る
    fn auto_enter_sweep(&mut self, est: u32, note: String) {
        let lo = ((est as f32 * 0.93 / 8.0) as u32 * 8).max(self.pll_min_hw());
        let hi = ((est as f32 * 1.07 / 8.0) as u32 * 8).min(AUTO_PLL_MAX);
        let cands: Vec<u32> = (lo..=hi).step_by(8).collect();
        if cands.is_empty() {
            self.auto = None;
            return;
        }
        let first = cands[0];
        let n = cands.len();
        if let Some(a) = self.auto.as_mut() {
            a.phase = AutoPhase::Sweep { cands, i: 0, best: (first, 0.0), med: Vec::new() };
        }
        self.auto_next(protocol::CFG_KEY_PLL_DIVIDE, first,
                       format!("{note} 局所探索 1/{n}"), 700);
    }

    fn auto_step(&mut self) {
        let Some((sharp, occ)) = self.auto_measure() else { return };
        let phase = match self.auto.as_mut() {
            Some(a) => std::mem::replace(&mut a.phase, AutoPhase::Oversample),
            None => return,
        };
        match phase {
            // --- 簡易スキャン: 候補の中を上から降りる ---
            //
            // 占有率は「Nyquistまでのうち実際に使われている割合」で、過剰サンプル
            // 側にいる限り 1/倍率 に一致する。だから (いまの pll_divide)×占有率 が
            // 1:1 の値の推定になる。フルスキャンはこの推定を ±7% の局所探索で
            // 詰めるが、こちらは**候補にスナップするだけ**でよい。候補は 4/3 倍
            // 以上離れているので、推定に -3% のバイアスと ±0.5% のばらつきが
            // あっても取り違えようがない。
            AutoPhase::QuickProbe { i, k, mut best, mut worst } => {
                if sharp > best.1 {
                    best = (k * 4, sharp);
                }
                worst = worst.min(sharp);
                // 位相は32段。粗く8点(4刻み)見れば感度の有無は分かる
                if k + 1 < 8 {
                    let n = match self.auto.as_ref().map(|a| &a.mode) {
                        Some(AutoMode::Quick { ladder, .. }) => ladder.len(),
                        _ => 1,
                    };
                    if let Some(a) = self.auto.as_mut() {
                        a.phase = AutoPhase::QuickProbe { i, k: k + 1, best, worst };
                    }
                    let pll = self.tune_pll_divide;
                    self.auto_next(protocol::CFG_KEY_PHASE, ((k + 1) * 4) as u32,
                                   format!("候補{}/{n} pll {pll}: 位相 {}/8",
                                           i + 1, k + 2),
                                   600);
                    return;
                }
                let ladder = match self.auto.as_ref().map(|a| &a.mode) {
                    Some(AutoMode::Quick { ladder, .. }) => ladder.clone(),
                    _ => return,
                };
                if let Some(AutoMode::Quick { probes, .. }) =
                    self.auto.as_mut().map(|a| &mut a.mode)
                {
                    probes.push((best.0, best.1, worst));
                }
                // --- 次の候補へ。**全部測ってから選ぶ。** ---
                //
                // ★以前は「感度が立った最初の候補で止まり、降りる先は占有率で
                //   枝刈りする」形だった。**枝刈りが効きすぎて実機で外した**
                //   (2026-09-04、31.5kHz の 512x512 で 1104 のまま動かなかった。
                //   降下が一度も起きていなかった)。
                //
                //   枝刈りの根拠は「est = 設定値 × 占有率 は真の htotal の下限」
                //   だったが、これが成り立っていなかった。真値 736 を 1104 で
                //   測ったときの占有率の理論上の上限は 736/1104 = 0.667 なのに、
                //   実測は 0.716 出た(99%エネルギーの裾がノイズを拾う)。下限として
                //   使えない量で枝刈りしていたので、正解が候補から消えていた。
                //
                //   いまは全候補の位相感度を測り、**いちばん感度が強い点**を採る。
                //   しきい値ちょうどの値に結果が左右されず、内訳も残せる。
                //   実測(31.5kHz 512x512): 1104→98% / 736→53% / 552→87%。
                //   正解の 736 が突出するので、取り違えようがない。
                let next = i + 1;
                if next < ladder.len() {
                    let c = ladder[next].clone();
                    let n = ladder.len();
                    if let Some(a) = self.auto.as_mut() {
                        a.phase = AutoPhase::QuickProbe {
                            i: next, k: 0, best: (0, 0.0), worst: f32::MAX,
                        };
                    }
                    self.send_cfg(protocol::CFG_KEY_PLL_DIVIDE, c.pll_divide);
                    self.tune_pll_divide = c.pll_divide as i32;
                    self.auto_next(protocol::CFG_KEY_PHASE, 0,
                                   format!("候補{}/{n} pll {}: 位相 1/8",
                                           next + 1, c.pll_divide),
                                   900);
                    return;
                }
                // --- 全候補を測り終えた。位相感度がいちばん強い点を採る ---
                let probes = match self.auto.as_ref().map(|a| &a.mode) {
                    Some(AutoMode::Quick { probes, .. }) => probes.clone(),
                    _ => return,
                };
                let (j, min_rel) = quick_pick(&probes);
                let rel_of = |p: &(u8, f32, f32)| if p.1 > 0.0 { p.2 / p.1 } else { 1.0 };
                // 判定の内訳を残す。**これが無くて原因の切り分けに手間をかけた。**
                let report = ladder
                    .iter()
                    .zip(probes.iter())
                    .map(|(c, p)| format!("{}→{:.0}%", c.pll_divide, rel_of(p) * 100.0))
                    .collect::<Vec<_>>()
                    .join(" ");
                let c = ladder[j].clone();
                let p = probes[j];
                if let Some(a) = self.auto.as_mut() {
                    a.worst = p.2;
                    a.over = c.oversample;
                    a.report = report;
                }
                if self.tune_pll_divide != c.pll_divide as i32 {
                    self.send_cfg(protocol::CFG_KEY_PLL_DIVIDE, c.pll_divide);
                    self.tune_pll_divide = c.pll_divide as i32;
                }
                self.auto_enter_phase_fine(
                    p.0, p.1,
                    format!("pll {} を採用(位相感度 {:.0}%)→ 位相を詰めています",
                            c.pll_divide, min_rel * 100.0));
            }
            AutoPhase::Oversample => {
                // 1:1の pll_divide ≒ 過剰サンプル時の pll_divide x 占有率。
                // 実測では真値に対して -3% の系統バイアスが残るので、局所探索で吸収する
                let est0 = (AUTO_PLL_MAX as f32 * occ).round() as u32;
                // TVPの下限を下回る場合は、下限を満たす最小の整数倍にする。
                // 整数倍なら位相ロックするのでドット間の混ざりは起きない。
                let pmin = self.pll_min_hw();
                let mut est = est0;
                let mut mult = 1u32;
                while est < pmin && mult < 8 {
                    mult += 1;
                    est = est0 * mult;
                }
                if occ > 0.9 || !(AUTO_PLL_MIN..=AUTO_PLL_MAX).contains(&est) {
                    if let Some(a) = self.auto.as_mut() {
                        a.note = format!("推定できません(占有率 {occ:.2})。\
                                          細かい模様が出ている画面で試してください");
                    }
                    // 元の値へ戻さず、ここで諦める(絵が出ない値に置き去りにしない)
                    let back = est.clamp(AUTO_PLL_MIN, AUTO_PLL_MAX);
                    self.send_cfg(protocol::CFG_KEY_PLL_DIVIDE, back);
                    self.tune_pll_divide = back as i32;
                    self.auto = None;
                    return;
                }
                let note = if mult > 1 {
                    format!("推定 {est0}(TVPの下限で{mult}倍= {est})→")
                } else {
                    format!("推定 {est} →")
                };
                self.auto_enter_sweep(est, note);
            }
            AutoPhase::Sweep { cands, i, mut best, mut med } => {
                if sharp > best.1 {
                    best = (cands[i], sharp);
                }
                med.push(sharp);
                let next = i + 1;
                if next < cands.len() {
                    let pll = cands[next];
                    let n = cands.len();
                    if let Some(a) = self.auto.as_mut() {
                        a.phase = AutoPhase::Sweep { cands, i: next, best, med };
                    }
                    self.auto_next(protocol::CFG_KEY_PLL_DIVIDE, pll,
                                   format!("局所探索 {}/{n}", next + 1), 700);
                } else {
                    // 突出度(中央値との比)が低いときは測定が信用できない
                    med.sort_by(|a, b| a.partial_cmp(b).unwrap());
                    let m = med[med.len() / 2];
                    let ratio = if m > 0.0 { best.1 / m } else { 0.0 };
                    if let Some(a) = self.auto.as_mut() {
                        a.phase = AutoPhase::PhaseCoarse { i: 0, best: (0, 0.0), all: Vec::new() };
                        a.note = format!("pll_div {} (突出度 {ratio:.2})→位相", best.0);
                    }
                    self.send_cfg(protocol::CFG_KEY_PLL_DIVIDE, best.0);
                    self.tune_pll_divide = best.0 as i32;
                    self.auto_next(protocol::CFG_KEY_PHASE, 0,
                                   format!("pll_div {} 突出度 {ratio:.2} → 位相 1/16", best.0),
                                   900);
                }
            }
            AutoPhase::PhaseCoarse { i, mut best, mut all } => {
                let cur = i * 2;
                if sharp > best.1 {
                    best = (cur, sharp);
                }
                all.push(sharp);
                if i + 1 < 16 {
                    let nxt = (i + 1) * 2;
                    if let Some(a) = self.auto.as_mut() {
                        a.phase = AutoPhase::PhaseCoarse { i: i + 1, best, all };
                    }
                    self.auto_next(protocol::CFG_KEY_PHASE, nxt as u32,
                                   format!("位相 {}/16", i + 2), 600);
                } else {
                    let worst = all.iter().cloned().fold(f32::MAX, f32::min);
                    // 粗い最良点の周辺を1刻みで詰める
                    let list: Vec<u8> = (0..5)
                        .map(|k| ((best.0 as i32 + k - 2).rem_euclid(32)) as u8)
                        .collect();
                    let first = list[0];
                    if let Some(a) = self.auto.as_mut() {
                        a.worst = worst;
                        a.phase = AutoPhase::PhaseFine { list, i: 0, best };
                    }
                    self.auto_next(protocol::CFG_KEY_PHASE, first as u32,
                                   "位相を詰めています".into(), 600);
                }
            }
            AutoPhase::PhaseFine { list, i, mut best } => {
                if sharp > best.1 {
                    best = (list[i], sharp);
                }
                let next = i + 1;
                if next < list.len() {
                    let ph = list[next];
                    if let Some(a) = self.auto.as_mut() {
                        a.phase = AutoPhase::PhaseFine { list, i: next, best };
                    }
                    self.auto_next(protocol::CFG_KEY_PHASE, ph as u32,
                                   "位相を詰めています".into(), 600);
                } else {
                    let worst = self.auto.as_ref().map_or(0.0, |a| a.worst);
                    let rel = if best.1 > 0.0 { worst / best.1 } else { 1.0 };
                    let attempt = self.auto.as_ref().map_or(0, |a| a.attempt);
                    let pll = self.tune_pll_divide as u32;
                    // 位相感度が1:1の指標になる。1ドット=1サンプルなら、位相を半ドット
                    // 動かせば全サンプルが中央から縁へ移るので鮮鋭度が大きく変わる。
                    // 変わらないなら「半分のサンプルが既に縁にいる」= 過剰サンプル。
                    // 実機の15kHzモードで最悪95%(=変わらない)のまま2.3倍の値に
                    // 着地したので、フルスキャンではその場合に半分にして測り直す。
                    // 半分にできるのは、それがTVPの下限以上のときだけ。下限で
                    // 過剰サンプルを強いられている帯域(15kHz)では位相感度が弱いのが
                    // 正常なので、ここで下げてしまうとPLLが範囲外の無効な領域へ入る
                    // (実機で432まで落ちて絵が壊れた)。
                    //
                    // ★**簡易スキャンではこの再測定をしない。** 探索空間が候補に
                    //   限られているので、位相感度で降りる先は「1つ下の候補」= 真値
                    //   より小さい実在しない設定になり、ドットを飛ばす方へ倒れる。
                    //   そもそも**倍率は分かっている**(選んだ点の oversample)。
                    //   下限のせいで×2になっている点なら位相感度が弱いのは当たり前で、
                    //   これは異常ではないので、判定にそう書けば足りる。
                    let quick = matches!(
                        self.auto.as_ref().map(|a| &a.mode),
                        Some(AutoMode::Quick { .. })
                    );
                    let over = self.auto.as_ref().map_or(1, |a| a.over);
                    let report = self.auto.as_ref().map_or(String::new(), |a| a.report.clone());
                    if !quick && rel > 0.85 && attempt < 2 && pll / 2 >= self.pll_min_hw() {
                        if let Some(a) = self.auto.as_mut() {
                            a.attempt = attempt + 1;
                        }
                        self.send_cfg(protocol::CFG_KEY_PHASE, 16);
                        self.tune_phase = 16;
                        let half = pll / 2;
                        self.auto_enter_sweep(
                            half,
                            format!("位相感度が弱い({:.0}%)ので {half} で再測定", rel * 100.0));
                        return;
                    }
                    self.send_cfg(protocol::CFG_KEY_PHASE, best.0 as u32);
                    self.tune_phase = best.0;
                    self.auto = None;
                    let at_floor = pll <= self.pll_min_hw() + 8;
                    let judge = if quick && over > 1 {
                        // 候補の htotal がTVPの下限を割るので、整数倍にせざるを
                        // 得なかった点。1:1にはできないが、位相ロックはしている
                        format!("TVPの下限で×{over}オーバーサンプル。このモードは1:1不可")
                    } else if at_floor {
                        "TVPの下限(12MHz)。このモードは1:1不可".to_string()
                    } else if rel <= 0.85 {
                        "1:1".to_string()
                    } else {
                        "要確認".to_string()
                    };
                    let how = if quick { "簡易" } else { "フル" };
                    // ★**判定の内訳を必ず出す。** 「pll_div 1104 / 位相 0 で完了
                    //   (要確認: 最悪の位相は 98%)」だけでは、候補を1つしか測って
                    //   いないのか全部測って選べなかったのかが分からず、実機で
                    //   外したときに切り分けられなかった(2026-09-04)。
                    let detail = if report.is_empty() {
                        String::new()
                    } else {
                        format!("  候補の位相感度: {report}")
                    };
                    self.auto_done = Some(format!(
                        "{how}: pll_div {} / 位相 {} で完了({judge}: 最悪の位相は {:.0}%){detail}",
                        pll, best.0, rel * 100.0));
                    self.want_fit = true;
                }
            }
        }
    }
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
