kunichiko/RetroCastX/gateware/retrocastx_capture.py

#!/usr/bin/env python3
"""TVP7002 ピクセルキャプチャ front-end(DATACLKドメイン → sysドメイン CDC)。

- cd_pix(=DATACLK) で RGB[9:2]=RGB888 をサンプルし RGB555 に変換
- HSOUT/VSOUT のアクティブエッジから 行内x / フレーム内row / frame / field を復元
- N面リングのラインバッファ(32bit=2px/entry, width/2 深さ×N面)に1ラインを書く
- ライン完成ごとにメタデータ {face, row, frame, field} を AsyncFIFO で sys へ渡す
  (pix→sys CDC)。sysのストリーマは pop して該当面を読み LINE パケット化する。
  FIFOが満杯(sysが間に合わない)なら、そのラインは書かずに捨てる=ライン単位ドロップ
  (画面の途中破壊=テアリングは起きない。面は TX 完了まで上書きされない)。

TVP設定(retrocastx_i2c 側): 0x18[0] CLK POL=1 にすると データは DATACLK 立下りで
launch されるので、pixドメイン(=DATACLK 立上り)で安定サンプルできる。

RGB555 レイアウト: 0RRRRRGGGGGBBBBB(host/python と一致)。
2px/entry: 低位16bit=偶数x(pix0), 高位16bit=奇数x(pix1)。
"""
from migen import *
from migen.genlib.cdc import PulseSynchronizer, MultiReg
from litex.soc.interconnect import stream


def rgb888_to_555(r, g, b):
    """8bit×3 → 16bit 0RRRRRGGGGGBBBBB(上位ビットを採用)。"""
    return Cat(b[3:8], g[3:8], r[3:8], C(0, 1))


# メタデータ(pix→sys AsyncFIFO のペイロード)。ts はそのラインの先頭画素における
# DATACLK自走カウンタ値(プロトコルのタイムスタンプ=ドットクロック単位)。
def _meta_layout(nface_bits, row_bits, entry_bits):
    # x_lo/x_hi はライン内の「黒でない範囲」をentry単位(=2画素)で示す。
    # (first/last はLiteXのストリームendpointで予約済みの名前なので使えない)
    # hs_offset を 0 にしてラインの頭から取り込む代わりに、送るのはこの範囲だけに
    # する。こうすると hs_offset は調整項目でなくなり、帯域も有効映像の幅ぶんで済む。
    return [("face", nface_bits), ("row", row_bits),
            ("frame", 16), ("field", 1), ("ts", 32),
            ("x_lo", entry_bits), ("x_hi", entry_bits)]


class TvpCapture(Module):
    """pads: r(8) g(8) b(8) hs vs [fid] を持つ Record。dataclk は呼び出し側で
    cd_pix に接続済みであること。width は偶数(2px/entry)。"""
    def __init__(self, pads, width=1024, height=512, nface=8, fifo_depth=4,
                 hs_active_low=True, vs_active_low=True,
                 hs_offset=0, vs_offset=0, vs_min_rows=0, vtotal=0,
                 vs_row_at_sync=0, hs_total=0, sys_clk_freq=45e6, measure=True,
                 auto_vtotal=False, vbp=0, interlace=False):
        # interlace: 1回のVSYNCの中にフィールドが2枚入る信号を、元の行数に織り直す。
        #   X68000の 24kHz 1024x848 は VSYNC がフレームに1回(vtotal 931行)しか来ず、
        #   その中に縦半分の解像度で画面全体を描いたフィールドが2枚並ぶ。そのまま
        #   送ると同じ絵が2回出る(実測: 466行周期で繰り返した)。
        # auto_vtotal: 実測vtotalに追従してフレーム境界と垂直位置を自動設定する。
        # vbp: 窓の先頭をVSYNCの何行後にするか(垂直バックポーチ相当)。
        # measure: 実測タイミング(周波数カウンタ)を作るか。34.8MHzで回る32bitカウンタが
        #   増えるため、ノイズ切り分け用に無効化できるようにしてある。無効時はMODEの
        #   諸元が0になる。
        # sys_clk_freq: 実測タイミングの1秒窓を作るのに使う(sysは25MHz水晶由来で正確)。
        # hs_total: 1ライン当たりのDATACLK数(=H-PLL分周比)。hs_offset+width がこれを
        #   超えると、行末側の列には一度も書き込まれずリングバッファの古い内容が
        #   残って見える。その範囲を毎ライン先頭(バックポーチ期間)に黒で埋める。
        # vs_row_at_sync (vtotal時のみ): VSYNC検出時に row へ入れる値。既定0=
        #   「キャプチャ窓の先頭=VSYNC」。N を指定すると窓はVSYNCの N 行手前から
        #   始まる(=映像がN行下がって見える)。フレーム境界(frameの歩進)は常に
        #   row のラップ点=窓の先頭なので、1枚の絵が2つのframe番号に割れない。
        # vs_min_rows: VSYNCを「フレーム開始」として受理する最小行数。0=ガード無効。
        #   row(=vsync以降に数えたHSYNC数)が vs_min_rows 未満のVSYNCエッジは無視する。
        #   VSOUTの等化/セレーションやノイズでフレーム途中に出る偽VSYNCで frame が
        #   多重に進む(受信側で内容が縦にロール)のを防ぐ。DATACLK周波数に非依存。
        # vtotal: >0 なら「HSYNC を vtotal 行数えたら1フレーム」の自走カウンタで
        #   フレーム境界を決める(VSOUTにノイズが乗っても崩れない)。TVP実測の
        #   Lines/Frame(例 568)を渡す。さらに vs_min_rows を併用すると、フレーム
        #   末尾付近のVSYNCエッジだけを受理して row=0 に再整列するため、垂直位置が
        #   本物のVSYNCへ自動で合う(自走のみだと開始位相が電源投入時のまま任意)。
        assert width % 2 == 0 and (width & (width - 1)) == 0, "width は2のべき乗"
        assert nface >= 2 and (nface & (nface - 1)) == 0
        # 面数 > 未処理メタ数 にして、送信中(head)の面が書込ポインタに追いつかれ
        # 上書きされる事を防ぐ(CDCのパイプライン段も見込んで +2 マージン)
        assert nface >= fifo_depth + 2, "nface は fifo_depth+2 以上"
        self.width = width
        self.height = height
        nface_bits = log2_int(nface)
        row_bits = max(1, log2_int(height))
        entries = width // 2                      # 面あたり32bitワード数
        entry_bits = log2_int(entries)            # entry(=xpix/2)のアドレスbit幅

        # --- sysドメイン: ストリーマ向けI/F ---
        self.line_valid = Signal()                # 送出可能ラインが有る
        self.line_row   = Signal(row_bits)        # 先頭ラインのフレーム内行
        self.line_frame = Signal(16)
        self.line_field = Signal()
        self.line_face  = Signal(nface_bits)      # FIFO先頭ラインの面(pop前にラッチ)
        self.line_ts    = Signal(32)              # 先頭ラインの先頭画素のDATACLKカウンタ
        self.line_first = Signal(entry_bits)      # 非黒範囲の先頭entry(=x/2)
        self.line_last  = Signal(entry_bits)      # 非黒範囲の末尾entry(内包)
        self.line_ack   = Signal()                # 1パルスで pop(送出開始時)
        self.rd_face    = Signal(nface_bits)      # 読み出す面(送信側がラッチして固定)
        self.rd_word    = Signal(max=max(entries, 2))   # 面内ワード位置(=x/2)
        self.rd_data    = Signal(64)              # {pix1, pix0} 各32bitスロット
        #   スロットの中身は **8bit×3 の生値**(byte0=R byte1=G byte2=B)。
        #   ★伝送形式(RGB555 / RGB888 / YC8)への変換は**送出側で行う**。
        #     バッファに8bitのまま持てば、形式を増やしてもここは変わらない。
        #     RGB555 は5bitしか運べず、X68000 の32階調を 1:1 で載せるには
        #     ゲイン誤差の余裕がゼロになる(実測 29/32)。8bit で運べば
        #     PC 側で32階調へ吸着できる。
        # 指定した行の「push時点の非黒範囲」を pix ドメインでラッチして見る窓。
        # FIFOも送信FSMも通らないので、キャプチャの判定そのものが正しいかを
        # 切り分けられる。実測で「範囲だけがFIFOの滞留段数ぶん遅れて見える」
        # 現象が出たが、それが判定側かFIFO/読出側かをこれで区別する。
        # フレーム間引き。0=毎フレーム送る、1=2フレームに1回、2=3回に1回…
        # 低スペックな受信機で取りこぼす場合の保険。映像だけを間引き、音声は
        # 間引かないので、同じ受信キューを共有している音声の取りこぼしも減る。
        # 間引くのは push の段階なので、メタFIFOにも面にも載らず、
        # ボード側の仕事そのものが減る。
        self.cfg_frame_skip     = Signal(4)          # key 0x35
        self.cfg_span_probe_row = Signal(row_bits)   # key 0x31
        self.stat_span_probe    = Signal(32)         # key 0x32: {any, hi, lo}
        # FIFO出口で pop した瞬間の {row, x_hi, x_lo}。同じエントリの値が揃って
        # 出ているかを見る。ヘッダの row は先頭からの直接スナップショット、
        # offset_px は先頭を追いかける2段レジスタ(span_lo)経由という非対称が
        # あるので、どちらで壊れているかをここで切り分ける。key 0x34
        self.stat_pop_probe     = Signal(32)
        # 診断用(sysで観測)
        self.cap_frame  = Signal(16)
        self.cap_drops  = Signal(16)
        # --- モードパラメータ(実行時に変更可。モード自動判定が書き換える)---
        # 既定値はコンストラクタ引数。cfg_* を駆動しなければその値のまま動く。
        # pixドメインで使うので、sysから変えるときは値が落ち着いてから使うこと
        # (モード切替時の1〜2フレームが乱れるだけなので、CDCは掛けていない)。
        self.cfg_vtotal        = Signal(13, reset=vtotal or 0)
        self.cfg_vs_min_rows   = Signal(13, reset=vs_min_rows)
        self.cfg_vs_row_at_sync = Signal(13, reset=vs_row_at_sync)
        self.cfg_hs_offset     = Signal(13, reset=hs_offset)
        self.cfg_vs_offset     = Signal(13, reset=vs_offset)
        # 末尾クリアの開始entry。= (hs_total - hs_offset)/2。0ならクリアしない。
        _fu = ((hs_total - hs_offset) // 2
               if (hs_total and hs_offset + width > hs_total) else 0)
        self.cfg_clear_from    = Signal(max=entries + 1, reset=_fu)
        # 垂直バックポーチ[行]。窓の先頭をVSYNCの何行後にするか。モードごとに違うので
        # 実行時に変えられるようにする(CONFIGパケットから調整する)。
        self.cfg_vbp           = Signal(13, reset=vbp)
        # 送出する行数。vtotalが小さいモードで512行送ると空きが出るので、
        # min(height, vtotal - vbp) を自動で入れる。
        self.cfg_vactive       = Signal(max=height + 1, reset=height)
        # 窓の長さ(折り返す前の row で数えた行数)。
        #
        # VSYNCで row には vtotal - vbp が入り、そこから増えて vtotal で0に戻るので、
        # VSYNC直後の vbp 本は row が大きい。折り返しを入れるとこの row が f2_row を
        # 超えて「第2フィールド」と判定され frow が小さくなり、窓の外なのに範囲内と
        # 見なされる(実機で帰線期間の行が画面下部に現れた)。折り返しはスロット番号を
        # 決めるためだけに使い、窓の判定は折り返す前の row で行う。
        # 既定は制限なし。auto_vtotal が vtotal - vbp を入れる。
        self.cfg_win_rows      = Signal(13, reset=2 ** 13 - 1)
        # インターレースの扱いは全て測定から決まるので設定は持たない。
        #   TVPの検出ビット(38h bit5)        インターレースかどうか
        #   生VSYNCの半ライン位相            どちらのフィールドが下か
        #   TVP vtotal / 生ライン数の比      フィールド単位かフレーム単位か
        # 以前は il(方式) / f2_row(折り返し点) / swap(偶奇) / field_src(極性の
        # 取得元)を人手で設定していたが、どれも信号から測れる量だった。
        # 方式2でフィールド極性をどこから取るか。0=VSYNCの水平位相 / 1=TVPのFIDOUT。
        # どちらが正しく出るかは実機で確かめられるよう選べるようにしてある。
        # TVPが検出したインターレース(レジスタ38h bit5 P/I detect の反転)。
        # データシート: "Progressive/interlaced video detection status. Not dependent
        # on the H-PLL being locked. 0 = Interlaced video detected"。
        # 1 なら折り返し+スロット偶奇の振り分けを自動で行う。
        self.cfg_il_detect     = Signal()
        # TVP自身が測った Lines per Frame(レジスタ37h:38h の12bit)。上位から供給。
        # 「VSOUTがフィールド単位か frame単位か」の判別に使う。生同期が来ない機種
        # (C-SYNCのみ→SOG)では meas_lines_raw が0になるので、こちらが唯一の手掛かり。
        # 0 なら未供給とみなして従来の仮定に落ちる。
        self.cfg_lpf_tvp       = Signal(12)
        # 1 で生同期の位相を使わない。既定0=生同期があれば使う(key 0x6A)。
        #
        # ★**生同期を繋がない入力方式では 1 にすること。** 未接続のシュミット
        #   バッファ入力は浮いて自己発振し、その周期が下の raw_ok の窓に入るので、
        #   **存在しない同期の位相でフィールド極性が決まってしまう**。
        #   詳細は retrocastx_stream.py の同名信号のコメント。
        self.cfg_no_raw_phase  = Signal()
        # ラインごとのHSYNC周期を測るプローブ。
        #
        # 「全幅の明るい横線の直後の3行だけ、内容が2サンプル早く取り込まれる」現象の
        # 切り分け用。生HSYNCとTVPのHSOUTを同じ行で同時に測れば、
        #   生の周期が変わっている  → X68000側がそう出している(実CRTでも起きる)
        #   生は一定でTVPだけ動く   → TVPの同期スライサが映像に引かれている
        # のどちらかが分かる。cfg_hs_probe_row で行を選び、2つの値を読む。
        self.cfg_hs_probe_row = Signal(13)
        self.stat_hs_probe_raw = Signal(16)   # その行の生HSYNC周期
        self.stat_hs_probe_tvp = Signal(16)   # その行のTVP HSOUT周期
        # 1ライン当たりのDATACLK数(=H-PLL分周比)。位相判定のしきい値に使う
        self.cfg_hs_total      = Signal(13, reset=hs_total or 0)
        # 診断用(sysで観測): VSYNCエッジ時の行内カウンタと、そのときのFIDOUT
        self.stat_vs_x         = Signal(16)
        self.stat_fid          = Signal()
        # 受信側へ報告する行数。インターレースでは織り込み後なので2倍になる。
        self.out_vactive       = Signal(max=2 * height + 1)

        # --- 実測タイミング(sysドメイン)。MODEパケットで報告する ---
        # ビルド時の仮定値ではなく実信号から測る。1秒窓のカウントなので単位はHz。
        self.meas_dotclk = Signal(32)             # DATACLK周波数 [Hz]
        self.meas_hfreq  = Signal(32)             # 水平周波数 [Hz]
        self.meas_vfreq  = Signal(32)             # 垂直周波数 [mHz] (8秒積算)
        self.meas_htotal = Signal(16)             # 1ライン当たりDATACLK数
        self.meas_vtotal = Signal(16)             # 1フレーム当たりライン数
        # ★ vtotal は「1秒窓のたまたまの1サンプル」なので偽VSYNCがそのまま出る。
        #   測定用VSYNC(vs_meas)は固定ガード64しか掛かっていない(鶏と卵を避ける
        #   ため意図的)ので、64行より後に出た偽VSYNCは素通りする。実機では
        #   vtotal 568 のところに 210/311/367/1136/2446 といった値が数十秒に一度
        #   混ざった(1136=VSYNC取りこぼし、他は偽VSYNCによる分割)。
        #   フレームごとに同じ値が連続したときだけ更新する版を別に持ち、
        #   モード追従とMODE報告はこちらを使う。meas_vtotal は生のまま診断に残す。
        self.meas_vtotal_stable = Signal(16)      # 連続一致したvtotalだけ通した値
        # 生同期(TVPを通らない経路)から測った絶対値。**pll_divideに一切依存しない。**
        #
        # 既存の meas_hfreq はTVPのHSOUTのエッジを数えているので、TVPのPLLが
        # サブハーモニックにロックすると半分の値になる。実機で発生: 31kHz 256x256
        # (真の htotal 552)に pll_div 1182 を入れるとPLLが半分のライン周期に
        # ロックし、fH が 15.98kHz と測れた。その値から VCOレンジやpll_minを決めて
        # いたため誤りが自己維持し、正しい値へ戻せなくなった。
        #
        # 生同期を sysドメイン(25MHz水晶由来)で数えれば、DATACLKが止まっていても
        # PLLが誤ロックしていても正しい値が得られる。すべての設定の根拠にできる。
        self.meas_fh_raw = Signal(32)             # 生HSYNC周波数 [Hz]
        self.meas_fv_raw = Signal(32)             # 生VSYNC周波数 [mHz](8秒積算)
        self.meas_lines_raw = Signal(16)          # 生VSYNC間の生HSYNC数(=vtotal)
        # TVPのHSOUT/VSOUTを sysクロック基準で測った絶対値。SOG(C-SYNCのみ)の機種では
        # 上の生同期系が全部0になるので、ロック判定はこちらで行う
        self.meas_fh_tvp = Signal(32)             # TVP HSOUT周波数 [Hz]
        self.meas_fv_tvp = Signal(32)             # TVP VSOUT周波数 [mHz](8秒積算)
        self.meas_lines_tvp = Signal(16)          # VSOUT間のHSOUT数(=vtotal)

        # --- ラインバッファ(true dual-port: write=pix / read=sys)---
        # 32bit→64bit へ広げた(2画素/エントリは維持、各画素32bitスロット)。
        # BRAM: 64 × nface × entries = 512 Kbit / LFE5U-25F の EBR 1008 Kbit
        self.specials.mem = mem = Memory(64, nface * entries)
        wr = mem.get_port(write_capable=True, clock_domain="pix")
        rd = mem.get_port(clock_domain="sys")
        self.specials += wr, rd

        # --- メタデータ CDC(pix → sys)。sink=pix / source=sys ---
        layout = _meta_layout(nface_bits, row_bits, entry_bits)
        self.submodules.meta = meta = stream.ClockDomainCrossing(
            layout, cd_from="pix", cd_to="sys", depth=max(fifo_depth, 4))

        # ================= pix ドメイン =================
        # RGB入力は必ず pix ドメインで1段レジスタに受ける。
        # 以前はピンから組合せ論理(ビット切り出し)を経てBRAMの書き込みデータ端子へ
        # 直結しており、ピン→BRAMの経路遅延が配置配線任せだった。DATACLKの分配遅延と
        # データ経路遅延の差が実効サンプリング点を決めるので、ビルドごとに配置が変わると
        # サンプリング点が動き、取りこぼし(下位ビットの化け=点状ノイズ)を起こし得る。
        # レジスタで受ければピン→FFが短く固定され、以降はnextpnrが時間検証できる
        # 内部経路になる。データはDATACLK同期なので1段でよい(非同期信号ではない)。
        r = Signal(8); g = Signal(8); b = Signal(8)
        self.sync.pix += [r.eq(pads.r), g.eq(pads.g), b.eq(pads.b)]
        # 入力2段FF(HSOUT/VSOUTはDATACLK同期だが念のため)
        hs0 = Signal(); vs0 = Signal(); hs = Signal(); vs = Signal()
        self.sync.pix += [hs0.eq(pads.hs), vs0.eq(pads.vs),
                          hs.eq(hs0), vs.eq(vs0)]
        hs_p = Signal(); vs_p = Signal()
        self.sync.pix += [hs_p.eq(hs), vs_p.eq(vs)]
        hs_edge = (hs_p & ~hs) if hs_active_low else (~hs_p & hs)  # アクティブ開始
        vs_edge_raw = (vs_p & ~vs) if vs_active_low else (~vs_p & vs)
        # vs_edge は row 定義後に行数ガードを掛ける(下記)
        vs_edge = Signal()

        x     = Signal(16)                        # 行内DATACLKカウンタ(hs後,飽和)
        face  = Signal(nface_bits)                # 書き込み中の面
        row   = Signal(13)                        # vsync以降の行番号(blanking含む)
        frame = Signal(16)
        field = Signal()
        wrote = Signal()                          # 現ラインに1画素以上書いたか
        # フレーム間引きの状態。frame_start で更新するが、push の判定に使うので
        # ここで宣言しておく(Migenは宣言順に依存しないが、Pythonの変数として
        # 先に存在している必要がある)
        skip_cnt = Signal(4)
        send_frame = Signal(reset=1)              # 間引きで落とすフレームでは 0
        pair_lo = Signal(32)                      # 偶数xピクセル保持(32bitスロット)

        # VSYNCエッジ行数ガード: 前回受理VSYNCからの経過行数(vrow)が vs_min_rows 以上の
        # エッジのみ受理する。row ではなく vrow を使うのは、vs_row_at_sync で表示位相を
        # ずらしても(=VSYNC時のrowが0でなくても)ガードが正しく効くようにするため。
        vrow = Signal(13)
        # cfg_vs_min_rows==0 ならガード無効(全VSYNCを受理)
        self.comb += vs_edge.eq(vs_edge_raw &
                                ((self.cfg_vs_min_rows == 0) |
                                 (vrow >= self.cfg_vs_min_rows)))
        probe_tvp = Signal(16)
        self.sync.pix += [
            If(hs_edge,
                If(vrow != 0x1FFF, vrow.eq(vrow + 1)),
                # 指定行のTVP HSOUT周期(hs_edge時点のxが直前ラインの長さ)
                If(vrow == self.cfg_hs_probe_row, probe_tvp.eq(x)),
            ),
            If(vs_edge, vrow.eq(0)),
        ]
        self.specials += MultiReg(probe_tvp, self.stat_hs_probe_tvp, "sys")
        # 測定用のVSYNCは cfg_vs_min_rows に依存させない。設定が現在のモードに
        # 合っていないと(例: vtotal 262 のモードでガードが497)VSYNCが全て捨てられ、
        # vtotalが測れなくなってモード追従が始められない(鶏と卵)。
        # 等化パルス除けの固定ガードだけ掛ける(実在モードの最小vtotalより十分小さい値)。
        VS_MEAS_GUARD = 64
        vrow_m = Signal(13)
        vs_meas = Signal()
        self.comb += vs_meas.eq(vs_edge_raw & (vrow_m >= VS_MEAS_GUARD))
        self.sync.pix += [
            If(hs_edge, If(vrow_m != 0x1FFF, vrow_m.eq(vrow_m + 1))),
            If(vs_meas, vrow_m.eq(0)),
        ]

        # --- vtotal のフレーム単位フィルタ(pixドメイン) ---
        # VSYNCごとに「前回と同じ値か」を見て、VT_HOLD+1 フレーム連続して同じ
        # だったときだけ vt_ok を更新する。単発の偽VSYNC/取りこぼしは1フレーム
        # で消えるので通らない。フレーム周期(約18ms)基準なので、本物のモード
        # 変更には 4フレーム = 0.07秒 で追従できる。
        #
        # ここを1秒窓の meas_vtotal 側でやってはいけない。1秒に1回しか値が
        # 変わらないので「3回連続」に3秒かかるうえ、以前の実装はsysクロック
        # ごとに数えていて、新しい値が来た最初のサイクルには既に飽和しており
        # ヒステリシスが全く効いていなかった(単発の異常値が即採用されていた)。
        #
        # 「同じ」は ±1 まで許し、候補は大きい方を取る。NTSC(コンポジット/S端子)
        # はフィールドごとに 262/263 が交互に来るので、完全一致を要求すると一度も
        # 成立せず、vt_ok が 0 のまま映像が出なくなった(gw-v0.9.3 後の main で実機)。
        # 大きい方を取るのは下の cfg_vtotal 側と同じ理由(自走の早回りを防ぐ)。
        # 偽VSYNCで割れたフレーム(例 100+101)は2つしか続かないので通らない。
        VT_HOLD = 3
        vt_cand = Signal(13)
        vt_n    = Signal(max=VT_HOLD + 1)
        vt_ok   = Signal(13)
        vt_same = Signal()
        self.comb += vt_same.eq((vrow_m == vt_cand)
                                | (vrow_m == vt_cand + 1)
                                | (vrow_m + 1 == vt_cand))
        self.sync.pix += If(vs_meas,
            If(vt_same,
                If(vrow_m > vt_cand, vt_cand.eq(vrow_m)),
                If(vt_n != VT_HOLD, vt_n.eq(vt_n + 1)).Else(vt_ok.eq(vt_cand)),
            ).Else(
                vt_cand.eq(vrow_m), vt_n.eq(0),
            ),
        )
        self.specials += MultiReg(vt_ok, self.meas_vtotal_stable, "sys")

        # --- 1画素(16bit)の詰め方。伝送フォーマットで切り替える ---
        #
        # 既定は RGB555。コンポジット/S-Video を扱うときは **8bitのまま**送る必要が
        # ある(RGB555の5bitではカラーバーストが数コードしか無く、副搬送波の位相を
        # 推定できない。詳細は docs/composite-video-plan.md §3)。
        #
        # YC8 は同じ16bit枠を「下位バイト=緑ch(コンポジットならCVBSそのもの、
        # S-VideoならY)/ 上位バイト=赤ch(S-VideoならC)」に使う。2B/px のままなので
        # **断片化もMTU計算も既存と完全に同じ**で、詰め方だけが変わる。
        # 1B/px の専用形式にすれば帯域は半分になるが、32bit語への詰め方から
        # 断片長の計算まで全部別系統になるので、まずはこの形で通す。
        self.cfg_raw_yc = Signal()          # 1 = YC8(生8bit) / 0 = RGB555
        raw_yc = Signal()                   # pixドメインへ同期した版
        self.specials += MultiReg(self.cfg_raw_yc, raw_yc, "pix")
        # ★バッファには**変換せず8bitのまま**入れる(byte0=R byte1=G byte2=B)。
        #   YC8 だけは「下位=緑ch / 上位=赤ch」という別の意味を持つ形式なので、
        #   ここで詰め替えておく(復調に8bitの生値が要るのは元から同じ)。
        pixw = Signal(32)
        self.comb += pixw.eq(Mux(raw_yc,
                                 Cat(g, r, C(0, 16)),      # YC8: byte0=緑 byte1=赤
                                 Cat(r, g, b, C(0, 8))))   # 生RGB888
        # 「黒でない」の判定しきい値(各成分の**上位5bit** = code>>3, 0..31)。
        # 範囲(送出する画素の左右端)を決めるためのもの。
        #
        # ★**この閾値は「暗い絵の中身」も黒と見なす。** 範囲から外れた画素は
        #   送られないので、受信側では 0 のままになる。閾値2は code>=24 でないと
        #   非黒にならないため、X68000 の32階調のうち**下2段(code 8,16)が
        #   丸ごと消えていた**(2026-09-03、RGB888で段ごとに実測して確定)。
        #   アナログでもクランプでもなく、ここが原因だった。粗オフセットを振っても
        #   直らなかったのは、デジタルの閾値だから。
        #
        # 既定を 2 → 0 にした。0 でも code 0..7 は非黒になれない(0>>3=0 で
        # 「> 0」を満たせない)ので、真っ黒は依然として範囲から外れる =
        # 帯域の最適化は生きている。実測した代償:
        #
        #     black_th=2   平均 count_px 304.4   314.7 Mbps
        #     black_th=0   平均 count_px 284.6   329.2 Mbps   (+4.6%)
        #
        #   以前は「ノイズで真っ暗な所が0にならないので、少し上げないと範囲が
        #   毎ライン全幅に広がる」としていたが、**v0.9.0 では起きなかった**。
        #   行数は増える(全黒扱いだった行が送られる)が1行あたりは短くなり、
        #   合計は +4.6% に収まる。仮配線の試作機で決めた値だったと思われる
        #   (MCLKがアナログRGBを横切っていた頃)。
        #   ※真っ黒画面でのノイズによる範囲の広がりは未測定。もし広がったら
        #     key 0x37 で実行時に上げられる。
        #
        # ★YC8では意味を持たない(ブランキングもバーストも「中身」なので、
        #   ライン全体を送る。上位が cfg_full_line 相当を強制する)。
        self.cfg_black_th = Signal(5, reset=0)

        # 有効行 row_eff = row - vs_offset(アクティブ行の0起点index)
        #
        # インターレース時は row をフィールド内行に直し、2倍して極性を足す
        # (= 元の行番号に織り戻す)。極性はVSYNCの位相ではなく「rowが折り返し点
        # f2_row を超えたか」で決める。この信号はVSYNCがフィールドごとに来ない
        # (フレームに1回だけ)ので、位相からは極性を判定できない。
        # --- インターレースのフィールド極性 ---
        # 方式1は row が折り返し点を超えたかで決まる(VSYNCが1回しか来ないので
        # 位相は使えない)。方式2はVSYNCがフィールドごとに来るので、標準どおり
        # 「VSYNCがラインの境界に来るか中央に来るか」で判別できる。TVP7002の
        # FIDOUTも同じ判定をしているはずなので、どちらを使うか選べるようにする。
        fid_in = Signal()
        if hasattr(pads, "fid"):
            fid0 = Signal()
            self.sync.pix += [fid0.eq(pads.fid), fid_in.eq(fid0)]
        # --- 生同期(TVPを通らない経路)の半ライン位相を測る ---
        #
        # TVPのVSOUTはインターレース入力の半ライン位相を保たない。生のHSYNC/VSYNCを
        # 直接見れば、第2フィールドのVSYNCが半ラインずれて来るのが分かる。位相が
        # 分かれば行位置の偶奇が決まり、il/f2_row/swap/field_src が不要になる。
        #
        # ここではまず測定だけを入れる(位置決めにはまだ使わない)。実機で位相が
        # 交互に出ることを確認してから繋ぐ。極性やRC遅延の影響で期待どおりに
        # ならない可能性があるので、先に切り分けられるようにしておく。
        self.stat_vs_x_raw = Signal(16)     # 生VSYNCエッジ時の生ライン内カウンタ
        self.stat_hs_len_raw = Signal(16)   # 生HSYNCの周期[pixクロック]
        ph_raw = Signal()                   # 生同期から見た半ライン位相
        raw_ok = Signal()                   # 生同期が使える状態か
        # ★**生同期から見た「インターレースかどうか」。**
        #
        #   半ライン位相がフィールドごとに交互になっていればインターレース。これは
        #   インターレースの定義そのもので、TVPの検出ビットに聞く必要が無い。
        #
        #   なぜ足したか: TVPのP/I検出(38h bit5)は X68000 の24kHz 1024x848 を
        #   **progressive と誤答する**(2026-09-03 実機: 0x57=0x21 でbit5=1。
        #   reg22h bit0 を立ててVSOUTを同期セパレータ直結にしても変わらなかった)。
        #   一方そのとき生VSYNCの位相は 715 と 11 を 106:94 で交互に取っていて、
        #   差 704 は生HSYNC周期 1407 のちょうど半分。判定材料としては完璧だった。
        #   il_det が 0 だと fld_pos も in_f2 も 0 に固定されるので、**織り込みが
        #   丸ごと止まり、2つのフィールドが上下に積まれた絵になる**(実機で発生)。
        il_raw = Signal()
        if hasattr(pads, "hs_raw") and hasattr(pads, "vs_raw"):
            hr0 = Signal(); hr = Signal(); hr_p = Signal()
            vr0 = Signal(); vr = Signal(); vr_p = Signal()
            self.sync.pix += [hr0.eq(pads.hs_raw), hr.eq(hr0), hr_p.eq(hr),
                              vr0.eq(pads.vs_raw), vr.eq(vr0), vr_p.eq(vr)]
            # 極性は不明なので両エッジで測り、周期が妥当な方を採る…のは複雑なので
            # まずアクティブローと仮定する(TVP経由と同じ想定)。ずれていたら
            # 位相が周期の端に張り付くので実機で判別できる。
            hr_edge = Signal(); vr_edge = Signal()
            self.comb += [hr_edge.eq(hr_p & ~hr), vr_edge.eq(vr_p & ~vr)]
            xr = Signal(16)                 # 生HSYNCからの行内カウンタ
            hs_len_r = Signal(16)
            vs_xr = Signal(16)
            self.sync.pix += [
                If(xr != 0xFFFF, xr.eq(xr + 1)),
                If(hr_edge, xr.eq(0), hs_len_r.eq(xr)),
                If(vr_edge, vs_xr.eq(xr)),
            ]
            self.specials += MultiReg(vs_xr, self.stat_vs_x_raw, "sys")
            self.specials += MultiReg(hs_len_r, self.stat_hs_len_raw, "sys")
            # 生VSYNCからの行数を数え、指定行の周期をラッチする
            vrow_r = Signal(13)
            probe_raw = Signal(16)
            self.sync.pix += [
                If(hr_edge,
                    If(vrow_r != 0x1FFF, vrow_r.eq(vrow_r + 1)),
                    If(vrow_r == self.cfg_hs_probe_row, probe_raw.eq(xr)),
                ),
                If(vr_edge, vrow_r.eq(0)),
            ]
            self.specials += MultiReg(probe_raw, self.stat_hs_probe_raw, "sys")

            # 半ライン位相のビット。VSYNCがラインの中央付近に来たフィールドは
            # 半ライン分あとから始まるので、そのラインは1スロット下へ落ちる。
            # どちらが先かは物理で決まるので swap の設定は要らない。
            #
            # 実測(24kHz 1024x848): 位相は 9 と 561 を 45:55 で交互に取り、差は
            # 552 = 生HSYNC周期1103 のちょうど半分だった。判定はライン周期の
            # 1/4〜3/4 を「中央付近」とする(TVP経由の判定と同じ考え方)。
            q_r = Signal(16)
            ph_now_r = Signal()                     # このVSYNCの位相(登録前の値)
            self.comb += [
                q_r.eq(hs_len_r[2:]),               # 周期/4
                ph_now_r.eq((xr > q_r) & (xr < (hs_len_r - q_r))),
            ]
            # 位相の交互性からインターレースを判定する。
            #
            # 上下カウンタにヒステリシスを付ける。交互で+1、同じで-1、0〜15で飽和。
            # 12でセット、4でクリア。**1回の取りこぼしで落ちないこと**が要点で、
            # ここが落ちると織り込みが止まって絵が上下に割れるので、判定は
            # 鈍いほうがよい。12フィールド≒0.2秒でロックする。
            il_cnt = Signal(4)
            self.sync.pix += If(vr_edge,
                ph_raw.eq(ph_now_r),
                # 生同期が生きているか。周期が妥当な範囲にあるかで見る。
                #
                # ★**「配線が無いなら周期は0か飽和値」は成り立たない。** 未接続の
                #   シュミットバッファ入力は浮いて自己発振し、周期がこの窓に入る。
                #   実機で raw_ok=1 になった(2026-09-06、コンポジット。D-SUBに
                #   何も繋いでいないのに立った)。生同期を使わない入力方式では
                #   cfg_no_raw_phase=1 で下の分岐ごと外すこと。
                raw_ok.eq((hs_len_r > 64) & (hs_len_r < 0xF000)),
                # ph_raw はこの時点ではまだ「前のフィールドの位相」なので、
                # ph_now_r と比べれば交互かどうかが分かる
                If(ph_now_r != ph_raw,
                    If(il_cnt != 15, il_cnt.eq(il_cnt + 1)),
                ).Elif(il_cnt != 0,
                    il_cnt.eq(il_cnt - 1),
                ),
                If(il_cnt >= 12, il_raw.eq(1)).Elif(il_cnt <= 4, il_raw.eq(0)),
            )

        # --- SOGOUT(同期スライサ出力)からコンポジット同期を分離して半ライン位相を測る ---
        #
        # C-SYNCしか出ない機種(MSX等)には生HSYNC/生VSYNCが無く、TVP経由の
        # HSOUT/VSOUTは半ライン位相を失っている(実測: LINEパケットのtsを12フィールド
        # 見て位相が全て0、フィールド間隔も1368×262と1368×263の整数で262.5にならない)。
        # SOGOUTは同期処理ブロックを通る前なので位相が残っているはず。
        #
        # やることはLM1881と同じ:
        #   Low期間の長さを測り、長いものを垂直ブロードパルスとみなす。
        #   その垂直区間の開始が直前の水平エッジから何クロック後かが半ライン位相。
        #
        # ここではまず**測定だけ**を入れる。フィールドごとに0と半ラインで交互に
        # なることを実機で確かめてから位置決めへ繋ぐ。極性もパルス幅も未知なので、
        # 判定の閾値は実行時に変えられるようにしておく。
        self.cfg_sog_vth  = Signal(16, reset=400)  # これ以上Lowが続いたら垂直とみなす
        # SOGOUTから取ったフィールド極性。sogoutが無い構成では常に0/0のまま
        ph_sog = Signal()      # 位相がライン中央付近(=半ライン下のフィールド)
        sog_ok = Signal()      # SOGOUTから同期を分離できているか
        # 極性の向きは実機で決める。ここを1にすると偶奇を入れ替える(key 0x66)
        self.cfg_field_invert = Signal()
        self.stat_sog_hlen = Signal(16)   # SOGOUTの水平周期[pixクロック]
        self.stat_sog_lowmax = Signal(16) # 直近フレームで見た最長Low期間
        self.stat_sog_vphase = Signal(16) # 垂直区間開始時の、直前水平エッジからの経過
        self.stat_sog_vlines = Signal(16) # 垂直区間の間隔[水平エッジ数]
        if hasattr(pads, "sogout"):
            sg0 = Signal(); sg = Signal(); sg_p = Signal()
            self.sync.pix += [sg0.eq(pads.sogout), sg.eq(sg0), sg_p.eq(sg)]
            sg_fall = Signal(); sg_rise = Signal()
            self.comb += [sg_fall.eq(sg_p & ~sg), sg_rise.eq(~sg_p & sg)]

            xs   = Signal(16)     # SOGOUTの直前の立下りからの経過(診断用)
            low  = Signal(16)     # 現在のLow期間の長さ
            # ★**最大値ホールドには必ずリセット経路を付ける。**
            #   以前は lowmax にリセットが無く、一度 0xFFFF に飽和すると二度と
            #   下がらなかった。sog_ok がその飽和値を「使える」と通してしまうので、
            #   壊れた位相を使い続け、**電源を入れ直すまで復帰しなかった**
            #   (実機のS端子で、絵が半ライン上下に震える形で出た。閾値を何に
            #    振っても値が1つも動かないので、信号ではなく測定が凍っていると
            #    分かった)。HSOUTを数えた固定窓で必ず作り直す。
            lowmax_acc = Signal(16)   # 現在の窓での最大
            lowmax = Signal(16)       # 直前の窓の結果(こちらを外へ出す)
            win = Signal(9)           # 512 HSOUT ≒ 2フィールド
            win_v = Signal()          # この窓で垂直検出があったか
            hlen = Signal(16)     # SOGOUTの立下り間隔(診断用)
            is_v = Signal()
            v_seen = Signal()
            vphase = Signal(16)
            vlines = Signal(16); vcnt = Signal(16)
            # 検出時点のライン内位相(ブロードパルス開始まで low ぶん戻す)
            ph_now = Signal(16)
            self.comb += ph_now.eq(Mux(x >= low, x - low,
                                       x + self.cfg_hs_total - low))
            q_s = Signal(16)
            self.comb += q_s.eq(self.cfg_hs_total[2:])       # 公称周期/4
            # ライン格子の基準は **HSOUT** を使う。
            #
            # 当初はSOGOUT自身の立下りから格子を作ったが、垂直区間の構造(等化パルスや
            # 1ラインより長いブロードパルス)に格子が引きずられ、位相が常に0になった
            # (実機: 最長Low=1502 は1ライン1368より長く、その直後のエッジが
            #  「通常ライン」と誤認されて格子をリセットしていた)。
            #
            # HSOUTはTVPが再生成した水平同期で、1ラインに1発、垂直区間でもH-PLLが
            # コーストするので途切れない。そして**キャプチャが行位置を決めるのに
            # 使っている格子そのもの**(x = HSOUTでリセットされるライン内カウンタ)
            # なので、これを基準にすれば測った位相をそのまま位置決めに使える。
            #
            # HSOUTは半ライン位相を失っているが、それは「VSOUTの位置」の話であって
            # ライン格子としては正しい。位相はSOGOUT側から取る。
            self.sync.pix += [
                If(~sg, If(low != 0xFFFF, low.eq(low + 1))),
                If(sg_fall, xs.eq(0), hlen.eq(xs)),
                If(xs != 0xFFFF, xs.eq(xs + 1)),
                If(sg_rise,
                    If(low > lowmax_acc, lowmax_acc.eq(low)),
                    low.eq(0),
                ),
                # HSOUT を数えて、垂直区間を抜けたら次に備える
                If(hs_edge,
                    If(vcnt != 0xFFFF, vcnt.eq(vcnt + 1)),
                    # ★`vcnt == 32` ではなく `>= 32`。等号だと、何かの拍子に
                    #   32 を飛び越えたとき v_seen が二度と戻らず、垂直検出が
                    #   永久に止まる(下の「検出を後ろに置く」の注記)。
                    If(v_seen & (vcnt[5:] != 0), v_seen.eq(0), is_v.eq(0)),
                    # 固定窓で lowmax を作り直す。垂直検出が来なくなっても
                    # ここは回るので、**壊れた状態から自力で復帰できる**。
                    win.eq(win + 1),
                    If(win == 511,
                        lowmax.eq(lowmax_acc), lowmax_acc.eq(0),
                        # この窓で垂直検出が1度も無ければ「使えない」に倒す
                        If(~win_v, sog_ok.eq(0)),
                        win_v.eq(0),
                    ),
                ),
                # ★**垂直検出はこのブロックより後ろに置く。** 検出は vcnt=0 と
                #   v_seen=1 を書くが、上の「HSOUT で vcnt+1」と同じクロックに
                #   重なると、Migen では後に書いた代入が勝つ。以前は検出が前に
                #   あったので、重なると vcnt が戻らずに 33 以上のまま進み、
                #   v_seen を戻す条件(当時は vcnt==32)を二度と満たさなかった。
                #   垂直検出が永久に止まり、sog_ok が倒れてフィールド極性が
                #   判定できなくなる(実機 2026-10-10、PS2 コンポジット: 垂直間隔
                #   35 / 位相 1419 で凍り、sog_vth を振っても値が動かず、電源を
                #   入れ直すまで戻らなかった。絵は半ライン上下に震えた)。
                #   sim_capture_sog.py がライン内の全オフセットで確かめる。
                # Low期間が閾値を超えた瞬間 = 垂直ブロードパルスの検出。
                # そのときのライン内位置 x が、HSOUT格子に対する垂直区間の位相。
                # ブロードパルスは low クロック前に始まっているのでその分戻す。
                If(~sg & (low == self.cfg_sog_vth) & ~v_seen,
                    is_v.eq(1), v_seen.eq(1),
                    vphase.eq(ph_now),
                    vlines.eq(vcnt), vcnt.eq(0),
                    # 位相がライン中央付近にあるフィールドは半ライン分あとから
                    # 始まるので、そのラインは1スロット下へ落ちる。判定の考え方は
                    # 生同期版(ph_raw)と同じで、1/4〜3/4を「中央付近」とする。
                    # 実測(MSXインターレース): 661(=中央付近) と 1348(=境界付近)が
                    # 交互に出た。差は687で半ライン684に一致する。
                    ph_sog.eq((ph_now > q_s) & (ph_now < (self.cfg_hs_total - q_s))),
                    win_v.eq(1),
                    # SOGOUTから同期を分離できているか。
                    #
                    # ★**上限も見る。** 以前は `(vcnt > 32) & (lowmax > 100)` で、
                    #   下限しか見ていなかった。ところが vcnt>32 は下の
                    #   「vcnt==32 で v_seen を戻す」ゲートが作る値(=33)でそのまま
                    #   通り、lowmax>100 は飽和値 65535 でも通る。つまり**測定が
                    #   壊れているときほど通ってしまう**判定だった。
                    #   垂直区間の間隔はフィールド単位262前後/フレーム単位525前後
                    #   なので、その範囲に入っていることを見る。
                    sog_ok.eq((vcnt > 200) & (vcnt < 600)
                              & (lowmax > 100) & (lowmax < 0x8000)),
                ),
            ]
            self.specials += MultiReg(hlen, self.stat_sog_hlen, "sys")
            self.specials += MultiReg(lowmax, self.stat_sog_lowmax, "sys")
            self.specials += MultiReg(vphase, self.stat_sog_vphase, "sys")
            self.specials += MultiReg(vlines, self.stat_sog_vlines, "sys")

        # 診断用: TVP経由のVSYNC位相とFIDOUT。位置決めには使わない(生同期を使う)
        vs_x   = Signal(16)          # VSYNCエッジ時の行内カウンタ(=位相)
        fid_vs = Signal()            # そのときのFIDOUT
        self.sync.pix += If(vs_edge_raw, vs_x.eq(x), fid_vs.eq(fid_in))

        # 位相から決まるフィールド極性。VSYNCがラインの中央付近に来たフィールドは
        # 半ライン分あとから始まるので、そのラインは1スロット下へ落ちる。
        # どちらが先かは物理で決まるので swap の設定は要らない。
        f2_row = Signal(13)
        in_f2  = Signal()
        fld_pos = Signal()
        frow   = Signal(13)          # フィールド内行
        fe     = Signal(13)          # フィールド内の有効行index
        # インターレースの扱い。
        #
        # TVPはインターレース入力でも Lines per Frame をフレーム全体(両フィールド
        # 合計)で報告し、VSOUTもフレームに1回しか出さない(データシート Table 16:
        # 480i60Hz も 480p60Hz も lines per frame = 525)。したがって row は両
        # フィールドを通して数える。折り返し点 vtotal/2 で前半/後半に分け、後半を
        # 1スロット下へ置けば織り込みになる。vtotal が奇数(X68000 24kHz 1024x848
        # では931)なので、この半端が半ラインに相当する。
        #
        # 判定はTVPの検出ビット(38h bit5)を使う。
        #
        # ただし折り返しが必要なのは「TVPのvtotalがフレーム全体(2フィールド分)を
        # 覆っているとき」だけ。同じX68000でもモードによってTVPのVSOUTがフィールド
        # ごとに来ることがあり、そのときvtotalは1フィールド分なので折り返してはいけない
        # (実機の15kHz Mode7: TVP vtotal 260 = 生のフィールドライン数 260。別の
        #  モードでは TVP vtotal 521 = 生 261 の約2倍だった)。
        # 折り返し点を vtotal/2 に置くと1フィールドを真ん中で割ってしまう。
        #
        # 生同期のライン数(pll_divideに依存しない絶対値)との比で判別する。
        # meas_lines_raw は sys のレジスタなので、pix 側では明示的にCDCして受け、
        # 判定もレジスタに落とす。組合せで sys から引くと、比較を経て
        # in_f2 → frow → fe → row_eff まで伸び、eth_rx が要求125MHzを割った
        # (5シード中4つが 123〜124MHz で失敗)。判定はモード切替時にしか
        # 変わらないので1クロック遅れは無害。
        il_frame = Signal()      # TVPのvtotalがフレーム全体を覆っているか
        # 判定に使う3つ(cfg_vtotal / meas_lines_raw / cfg_lpf_tvp)は全て sys の
        # レジスタなので、**判定ごと sys で済ませて1bitだけCDCする**。
        # 以前は meas_lines_raw を16bitでCDCして pix 側で比較していたが、そこへ
        # cfg_lpf_tvp との比較を足したら eth_rx が 123.59MHz まで落ちて要求125MHzを
        # 割った(配線後の最終レポート)。pix側の比較器と広いCDCを無くすことで、
        # in_f2 → frow → fe → row_eff の組合せも短くなる。
        # 判定はモード切替時にしか変わらないので、CDCの遅れは無害。
        il_frame_sys = Signal()
        self.sync += If(self.meas_lines_raw > 32,
            # 生同期が使える機種: TVPのvtotalが生のライン数の1.5倍を超えるか
            il_frame_sys.eq(self.cfg_vtotal >
                            (self.meas_lines_raw + (self.meas_lines_raw >> 1))),
        ).Elif(self.cfg_lpf_tvp != 0,
            # 生同期が使えない機種(MSXのようにC-SYNCしか出ずSOG経由で受けるもの)は
            # meas_lines_raw が0のままなので上が使えない。TVP自身の Lines per Frame
            # (レジスタ37h:38h、内部基準で測るのでH-PLLにも生同期にも依存しない)と
            # cfg_vtotal(VSOUT間のライン数)を比べれば同じ判別ができる:
            #   フレーム単位 cfg_vtotal ≈ LPF     → 1.5倍すればLPFを超える
            #   フィールド単位 cfg_vtotal ≈ LPF/2 → 1.5倍してもLPFに届かない
            # 実測(MSXインターレース): LPF=525, cfg_vtotal=262 → 393 < 525 でフィールド単位。
            # 以前はここが無く「フレーム単位」と決め打ちしていたため、折り返し点
            # vtotal/2 で1フィールドを真ん中から割っていた(絵がスカスカのストライプ)。
            #
            # 0 は「上位から未供給」の意味。TVPが壊れた値(実測で Lines per Frame が
            # 1 になる状態を見ている)を返しても、その場合は比較が真になって従来どおり
            # 「フレーム単位」に落ちるので害は無い。
            il_frame_sys.eq((self.cfg_vtotal + (self.cfg_vtotal >> 1)) >
                            self.cfg_lpf_tvp),
        ).Else(
            # どちらも無い(SIM等)。従来どおりフレーム単位と仮定する
            il_frame_sys.eq(1),
        )
        self.specials += MultiReg(il_frame_sys, il_frame, "pix")
        il_det = Signal()
        # インターレース判定は**2つの情報源のORにする。**
        #
        #   cfg_il_detect  TVPのP/I検出(38h bit5)。X68000の24kHz 1024x848 を
        #                  progressive と誤答する(2026-09-03 実機で確認)
        #   il_raw         生VSYNCの半ライン位相が交互かどうか。上の実測では
        #                  715/11 を 106:94 で交互に取っていて完璧だった
        #
        # ORにするのは、**いま動いているモードを絶対に壊さないため**。TVPが検出
        # できている帯域(15kHz系)は今までどおり通り、TVPが取りこぼす帯域だけを
        # 生同期が拾う。片方を優先する形にすると、生同期側が想定外の信号で
        # 落ちたときに今動いているものが止まる。
        #
        # ★レジスタに落としてから使う。ここは il_det → in_f2 → frow → fe →
        #   row_eff と伸びる組合せ経路の起点で、cfg_il_detect は sys 側から
        #   来ている。以前この経路に比較を1つ足しただけで eth_rx が 123.59MHz
        #   まで落ちて要求125MHzを割った。判定はモード切替時にしか変わらないので
        #   1クロック遅れは無害。
        il_det_r = Signal()
        self.sync.pix += il_det_r.eq(self.cfg_il_detect | il_raw)
        self.comb += [
            il_det.eq(il_det_r),
            f2_row.eq(self.cfg_vtotal[1:]),             # 折り返し点 = vtotal/2
            # 折り返すのはフレーム単位のときだけ
            in_f2.eq(il_det & il_frame & (row >= f2_row)),
            frow.eq(row - Mux(in_f2, f2_row, 0)),
            fe.eq(frow - self.cfg_vs_offset),
            # スロットの偶奇。
            #
            # どちらのフィールドが半ライン下かは物理で決まるので設定は要らない。
            #
            # 垂直位置はVSYNCからの経過時間で決まり、そのフィールドの最初のラインは
            # 「VSYNCの次のHSYNC」から始まる。位相を p(直前のHSYNCから何サンプル後に
            # VSYNCが来たか)とすると、次のHSYNCまでは (htotal - p) サンプル。
            # つまり p が大きいフィールドほど早く始まり、上に来る。
            #
            # 実測(24kHz 1024x848, htotal 1104):
            #   p = 9   → 次のHSYNCは1095サンプル後 → 遅い → 下(スロット +1)
            #   p = 561 → 次のHSYNCは 543サンプル後 → 早い → 上(スロット +0)
            #
            # ph_raw は「pがライン中央付近」なので、下になるのは ~ph_raw の側。
            # 当初 ph_raw をそのまま使って実機で織り込みが逆になった。
            #
            # 生同期が無い場合だけ「TVPのフレームの後半が第2フィールド」と推測する。
            # これはVSOUTが2本のVSYNCのどちらで出るかに依存するので当たらないことが
            # あり、実機では逆になった。その場合の逃げ道として swap を残す。
            # プログレッシブでは1フィールドしかないので偶奇は常に0。
            # 位相による反転はインターレースの第2フィールドを見分けるためのもので、
            # 無条件に適用すると全ての行が奇数スロットへ入り、半ライン分ずれた位置に
            # 置かれる(実機で「全行が同じようにずれる」形で出た)。
            If(~il_det,
                fld_pos.eq(0),
            ).Elif(raw_ok & ~self.cfg_no_raw_phase,
                fld_pos.eq(~ph_raw ^ self.cfg_field_invert),
            ).Elif(sog_ok,
                # 生同期が無い機種(C-SYNCのみ→SOG)はSOGOUTから取った位相を使う。
                # TVPのHSOUT/VSOUT/FIDOUTはいずれも半ライン位相を失っている
                # (実測: VSOUT位相1066固定、FIDOUT=1固定、LINEのtsも全フィールド同位相)。
                fld_pos.eq(~ph_sog ^ self.cfg_field_invert),
            ).Else(
                # 生同期が無い環境(旧基板)向けの推測。TVPのVSOUTが2本のVSYNCの
                # どちらで出るかに依存するので当たらないことがある。現基板では
                # 生同期があるのでこの経路は使わない
                fld_pos.eq(in_f2),
            ),
        ]
        # row_ok / row_eff はレジスタに落とす。これらは画素書込のイネーブル
        # (wr.we)まで届くので、組合せのままだと減算2段+比較がBRAMの書込端子
        # 直前まで伸びる。実際 sys が 53.6→42.5MHz まで落ちて要求45MHzを割った。
        # row は hs_edge でしか変わらず、画素が始まるのは hs_offset(数百クロック)
        # 後なので、1クロック遅れても取りこぼさない。hs_edge 時点の値は「いま
        # 終わったライン」のもので、push の判定に使う値として正しい。
        row_eff = Signal(14)
        row_ok  = Signal()
        field_r = Signal()
        ph_r    = Signal()           # 半ライン位相(このVSYNC周期のフィールド)
        # 行位置は「VSYNCから何半ライン後か」で決める。
        #
        # インターレースの原理そのもので、第2フィールドのVSYNCは半ライン分ずれた
        # 位置に来るので、そのフィールドのラインは第1フィールドのラインの物理的に
        # 間へ落ちる。だから位置を時間(半ライン単位)で決めれば、織り込みは設定
        # 無しで勝手に成立する。以前は il/f2_row/swap/field_src の4つで教えて
        # いたが、どれも「行番号で並べる」という実装の都合から生まれたもので、
        # 信号自体には無かった情報である。
        #
        # プログレッシブでは ph が毎フレーム同じ値になるので、スロットは1つ飛びに
        # 並ぶ。空くスロットは受信側が「次のラインまでの間隔」ぶん太らせて埋める
        # (ビームには太さがあるので物理的にも正しい)。
        #
        # cfg_half_line=0 にすると位相を無視する(位相判定が誤る信号に当たった
        # ときの逃げ道。既定は1)。
        self.sync.pix += [
            # 窓の内か。フィールドあたりの行数(cfg_vactive)と、折り返す前の row で
            # 数えた窓の長さ(cfg_win_rows)の両方で判定する。後者が無いと、VSYNC直後の
            # 帰線期間の行が折り返しで「第2フィールド」と誤判定されて画面下部に出る。
            row_ok.eq((frow >= self.cfg_vs_offset)
                      & (fe < self.cfg_vactive)
                      & (row < self.cfg_win_rows)),
            ph_r.eq(fld_pos),
            field_r.eq(fld_pos),
            # = fe*2 + 位相。cfg_half_line は位相の「取得元」を選ぶ信号なので、
            # ここで偶奇の適用をゲートしてはいけない
            row_eff.eq(Cat(fld_pos, fe)),
        ]

        xpix   = Signal(16)                       # 有効ピクセルx(= x - hs_offset)
        active = Signal()
        pix_we = Signal()                         # 画素ペア書込(末尾クリアと区別)
        # entry = xpix/2(entry_bits幅に切出)。xpix[1:]は15bit幅なので明示スライス
        # しないと face がアドレス上位へ押し出される
        pix_adr = Signal(entry_bits)
        self.comb += [
            xpix.eq(x - self.cfg_hs_offset),
            active.eq((x >= self.cfg_hs_offset) & (xpix < width) & row_ok),
            pix_we.eq(active & xpix[0]),          # 奇数pxが揃った時に1ペア書込
            pix_adr.eq(xpix[1:1 + entry_bits]),
        ]

        # --- ライン内の「黒でない範囲」を entry 単位で記録する ---
        # 送るのはこの範囲だけにする。ライン全体(ブランキング込み)を送ると帯域が
        # 1.4倍になって入らないため。範囲はラインが終わってから push するので、
        # 1ライン分バッファしている今の構造のまま実現できる。
        #
        # ★YC8(生8bit)では判定式のビット割りが合わないので結果は無意味になる。
        #   YC8はブランキングもバーストもライン全体が「中身」なので範囲最適化自体が
        #   成立しない。上位(retrocastx_stream.py)が cfg_full_line 相当を強制し、
        #   ここの ln_first/ln_last を使わないようにしてある。
        def _nz(p):
            # ★しきい値は RGB555 の 5bit 値(0..31)で定義されているので、
            #   8bit スロットの**上位5bit**と比べる。こうすると 32bit 化しても
            #   非黒範囲の判定が従来とビット単位で一致する。
            return ((p[3:8] > self.cfg_black_th)        # R
                    | (p[11:16] > self.cfg_black_th)    # G
                    | (p[19:24] > self.cfg_black_th))   # B
        pair_nz = Signal()
        self.comb += pair_nz.eq(pix_we & (_nz(pixw) | _nz(pair_lo)))
        ln_first = Signal(entry_bits, reset=2 ** entry_bits - 1)
        ln_last = Signal(entry_bits)
        ln_any = Signal()
        self.sync.pix += [
            If(pair_nz,
                If(~ln_any | (pix_adr < ln_first), ln_first.eq(pix_adr)),
                If(~ln_any | (pix_adr > ln_last), ln_last.eq(pix_adr)),
                ln_any.eq(1),
            ),
        ]

        # 窓が行末を超える分(= 毎ライン書かれないままリングの古い内容が見える列)を
        # ライン先頭のバックポーチ期間に黒で埋める。1サイクル1エントリ。
        # cfg_clear_from(=(hs_total-hs_offset)/2)から entries-1 までを埋める。
        # モードが変わると必要範囲も変わるので実行時信号にしてある。0ならクリアしない。
        # バックポーチ中は active=0 なので画素書込と衝突しない。間に合わなくても
        # そのラインの末尾が古い値のまま残るだけで、破綻はしない。
        clr_adr = Signal(max=entries + 1)
        clr_busy = Signal()
        self.comb += clr_busy.eq((self.cfg_clear_from != 0) &
                                 (x < self.cfg_hs_offset) &
                                 (clr_adr < entries))
        # クリアはライン先頭のバックポーチ中しか進められないので、1ライン当たり
        # hs_offset エントリしか消せない。毎ライン先頭に戻していたため、窓が
        # ラインより大幅に広いモード(15kHz 512x512: 1ライン544クロックに対し窓
        # 1024画素)ではクリアが先頭付近しか届かず、右側にリングバッファの古い
        # 内容が残った。ラインをまたいで進め、末端まで行ったら先頭へ戻す。
        # 消した所には二度と画素が書かれないので、一巡すれば黒のまま安定する。
        self.sync.pix += [
            If(clr_busy,
                If(clr_adr >= entries - 1,
                    clr_adr.eq(self.cfg_clear_from),
                ).Else(
                    clr_adr.eq(clr_adr + 1),
                ),
            ),
            # cfg_clear_from が動いた(モードや設定の変更)ときは範囲内へ引き戻す
            If(clr_adr < self.cfg_clear_from, clr_adr.eq(self.cfg_clear_from)),
        ]
        self.comb += If(clr_busy,
            wr.adr.eq(Cat(clr_adr[:entry_bits], face)), wr.dat_w.eq(0), wr.we.eq(1),
        ).Else(
            wr.adr.eq(Cat(pix_adr, face)),
            wr.dat_w.eq(Cat(pair_lo, pixw)),   # {奇数px, 偶数px}
            wr.we.eq(pix_we),
        )

        # メタ push(hs_edge時、直前ラインが有効(row_ok)かつ1画素以上書いた場合)。
        # FIFO満杯なら drop。
        # DATACLK自走カウンタ = プロトコルのタイムスタンプ(ドットクロック単位)。
        # 定数(htotal×frame番号)から算出すると仮定したモードでしか合わないが、
        # 実カウンタなら常に正確で、音声との同期もモードに依らず成立する。
        ts_cnt = Signal(32)
        cur_ts = Signal(32)      # 現ラインの先頭画素(x=hs_offset)でのカウンタ値
        self.sync.pix += [
            ts_cnt.eq(ts_cnt + 1),
            If(hs_edge, cur_ts.eq(ts_cnt + hs_offset)),
        ]

        push = Signal()
        self.comb += [
            # 間引きで落とすフレームは push しない(FIFOにも面にも載せない)
            push.eq(hs_edge & wrote & row_ok & send_frame),
            meta.sink.face.eq(face),
            meta.sink.row.eq(row_eff[:row_bits]),
            meta.sink.frame.eq(frame),
            # インターレース時は実際のフィールド極性を載せる(非対応時は従来の交互)
            # 織り込んでいるときは実際のフィールド極性、そうでなければ従来の交互
            meta.sink.field.eq(Mux(il_det, field_r, field)),
            # hs_edge時点の cur_ts は「今終わったライン」の先頭値(更新はクロック端で
            # 起きるため)。push するのもそのラインなので一致する。
            meta.sink.ts.eq(cur_ts),
            meta.sink.x_lo.eq(ln_first),
            meta.sink.x_hi.eq(ln_last),
            meta.sink.valid.eq(push),
        ]
        drops = Signal(16)
        _hs_body = [
            x.eq(0),
            wrote.eq(0),
            ln_any.eq(0), ln_first.eq(2 ** entry_bits - 1), ln_last.eq(0),
            If(push & meta.sink.ready, face.eq(face + 1)),   # 受理時のみ面前進
            If(push & ~meta.sink.ready, drops.eq(drops + 1)),
        ]
        self.sync.pix += [
            If(active & ~xpix[0], pair_lo.eq(pixw)),  # 偶数x: 低位に保持
            # 「1画素以上書いたか」。末尾クリアでは立てない。
            # 黒でない画素があったかどうかとは別に持つ。全黒の行を送らない設計に
            # すると、Viewer側が「黒い行」と「届かなかった行」を区別できなくなり、
            # 前フレームの内容が残る(インターレースのSIMでも、内容が0の行が
            # まるごと落ちて織り込みが崩れた)。行は必ず送り、中身の範囲だけを
            # x_lo/x_hi で示す(全黒なら空範囲)。
            If(pix_we, wrote.eq(1)),
            If(x != 0xFFFF, x.eq(x + 1)),               # 行内カウンタ(飽和)
        ]
        # 自走(row==cfg_vtotal-1でラップ)+ 位相ゲート付きVSYNC再整列。
        # フレーム境界(frame歩進)は常に row のラップ点=キャプチャ窓の先頭に固定。
        # VSYNCは row を cfg_vs_row_at_sync に入れ直すだけで frame は進めない。これに
        # より、窓をVSYNCより手前から開いても1枚の絵が2つのframe番号に割れない。
        # VSYNCは即座に row を書き換えず「次のHSYNCで row:=cfg_vs_row_at_sync」と
        # 保留する(vs_pend)。即時に書くと、その行は次のhs_edgeで row+1 されて
        # しまい1行まるごと欠落する。また行の途中で row が変わると行番号がずれる。
        # cfg_vtotal==0 なら自走せずVSYNCだけでフレーム境界を決める(旧来の挙動)。
        vs_pend = Signal()
        # フレーム開始 = 「row が 0 に戻る瞬間」。自走ラップか、cfg_vs_row_at_sync==0
        # のときはVSYNC再整列もそれに当たる。この規則にしないと、VSYNCがちょうど
        # ラップ点に来る場合に vs_pend がラップを打ち消して frame が永久に進まなくなる。
        wrap_now = Signal()
        frame_start = Signal()
        free_run = Signal()
        self.comb += [
            free_run.eq(self.cfg_vtotal != 0),
            wrap_now.eq(hs_edge & ~vs_pend & free_run &
                        (row == self.cfg_vtotal - 1)),
            frame_start.eq(wrap_now |
                           (hs_edge & vs_pend & (self.cfg_vs_row_at_sync == 0)) |
                           (vs_edge & ~free_run)),
        ]
        self.sync.pix += [
            # vs_pend は自走時のみ使う(非自走ではVSYNCで即座にrow=0にするので、
            # 保留すると次のhs_edgeでもrowが0に戻り、行番号が1つ重複してしまう)
            If(vs_edge & free_run, vs_pend.eq(1)),
            If(hs_edge,
                *_hs_body,
                If(vs_pend,
                    row.eq(self.cfg_vs_row_at_sync), vs_pend.eq(0),
                ).Elif(wrap_now,
                    row.eq(0),
                ).Else(
                    row.eq(row + 1),
                ),
            ),
            # 自走しない設定ではVSYNCで即座にrowを0へ(旧来の挙動)
            If(vs_edge & ~free_run, row.eq(0), wrote.eq(0)),
            If(frame_start, frame.eq(frame + 1), field.eq(~field)),
            # このフレームを送るか。frame_start ごとに数え、cfg_frame_skip 回
            # 飛ばして1回送る。0 なら常に送る。
            If(frame_start,
                If(skip_cnt >= self.cfg_frame_skip,
                    skip_cnt.eq(0), send_frame.eq(1),
                ).Else(
                    skip_cnt.eq(skip_cnt + 1), send_frame.eq(0),
                ),
            ),
        ]

        # --- 実測タイミング: 1秒窓(sysクロック基準=25MHz水晶由来で正確)で
        #     DATACLK/HSYNC/VSYNC を数える。窓が1秒ちょうどなのでカウント値がHz。
        #     htotal/vtotal は行内カウンタ/行カウンタをそのままラッチして得る。
        if measure:
            m_clk = Signal(32); m_hs = Signal(32); m_vs = Signal(32)
            s_clk = Signal(32); s_hs = Signal(32); s_vs = Signal(32)
            s_htot = Signal(16); s_vtot = Signal(16)
            htot_now = Signal(16); vtot_now = Signal(16)
            self.sync.pix += [
                If(hs_edge, htot_now.eq(x + 1)),   # xはライン先頭で0→次のedgeでperiod-1
                If(vs_meas, vtot_now.eq(vrow_m)),  # 前回VSYNCからのHSYNC数
            ]
            # sys → pix へ「今のカウンタを確定して0に戻せ」のパルスを送る
            self.submodules._samp = _samp = PulseSynchronizer("sys", "pix")
            self.sync.pix += [
                If(_samp.o,
                    s_clk.eq(m_clk), s_hs.eq(m_hs), s_vs.eq(m_vs),
                    s_htot.eq(htot_now), s_vtot.eq(vtot_now),
                    m_clk.eq(0), m_hs.eq(hs_edge), m_vs.eq(vs_meas),
                ).Else(
                    m_clk.eq(m_clk + 1),
                    If(hs_edge, m_hs.eq(m_hs + 1)),
                    If(vs_meas, m_vs.eq(m_vs + 1)),
                ),
            ]
            # sys側: 1秒ごとにサンプルパルスを出し、少し待って確定値を取り込む。
            # s_* はパルス後しか変化しないので、待ってから MultiReg で受ければ安全。
            WIN = max(int(sys_clk_freq), 4)
            win = Signal(max=WIN)
            wait = Signal(6)
            vs_stable = None
            for src, dst in ((s_clk, self.meas_dotclk), (s_hs, self.meas_hfreq),
                             (s_vs, None), (s_htot, self.meas_htotal),
                             (s_vtot, self.meas_vtotal)):
                stable = Signal(len(src))
                self.specials += MultiReg(src, stable, "sys")
                if dst is None:
                    vs_stable = stable      # VSYNCは下の8秒積算で使う
                else:
                    self.sync += If(wait == 1, dst.eq(stable))
            self.comb += _samp.i.eq(win == WIN - 1)
            self.sync += [
                If(win == WIN - 1, win.eq(0)).Else(win.eq(win + 1)),
                If(win == WIN - 1, wait.eq(32)).Elif(wait != 0, wait.eq(wait - 1)),
            ]
            # --- 生同期を sysドメインで数える(pll_divideに依存しない絶対値)---
            if hasattr(pads, "hs_raw") and hasattr(pads, "vs_raw"):
                # 生同期は sys に対して非同期なので2段FFで受ける
                sh0 = Signal(); sh = Signal(); sh_p = Signal()
                sv0 = Signal(); sv = Signal(); sv_p = Signal()
                self.sync += [sh0.eq(pads.hs_raw), sh.eq(sh0), sh_p.eq(sh),
                              sv0.eq(pads.vs_raw), sv.eq(sv0), sv_p.eq(sv)]
                she = Signal(); sve = Signal()
                self.comb += [she.eq(sh_p & ~sh), sve.eq(sv_p & ~sv)]
                ch = Signal(32); cv = Signal(32)
                lines_now = Signal(16); lines_cnt = Signal(16)
                vacc_r = Signal(24); vwin_r = Signal(3)
                self.sync += [
                    # 生VSYNC間の生HSYNC数 = そのモードのvtotal(pll非依存)
                    If(she, lines_cnt.eq(lines_cnt + 1)),
                    If(sve, lines_now.eq(lines_cnt), lines_cnt.eq(0)),
                    # 1秒窓のエッジ数 = 周波数[Hz]
                    If(win == WIN - 1,
                        self.meas_fh_raw.eq(ch), ch.eq(she),
                        self.meas_lines_raw.eq(lines_now),
                        # fVは8秒積算して mHz にする(1秒窓だと分解能±1Hz)
                        If(vwin_r == 7,
                            self.meas_fv_raw.eq((vacc_r + cv) * 125),
                            vacc_r.eq(0), vwin_r.eq(0),
                        ).Else(
                            vacc_r.eq(vacc_r + cv), vwin_r.eq(vwin_r + 1),
                        ),
                        cv.eq(sve),
                    ).Else(
                        If(she, ch.eq(ch + 1)),
                        If(sve, cv.eq(cv + 1)),
                    ),
                ]

            # --- TVPのHSOUT/VSOUTも sysドメインで数える ---
            # 生同期(hs_raw/vs_raw)はC-SYNCのみの機種(MSX等、SOG経由)では無信号に
            # なるため、上の絶対測定が全部0になり「ロックしているか」を判定できない。
            # stat_hs_probe_tvp は DATACLK基準で、DATACLK自体がこのHSOUTにロックした
            # PLLの出力なので常に pll_divide を返す循環参照になっていて使えない。
            # sysクロック基準で数えれば pll_divide に依存しない絶対値が得られる。
            th0 = Signal(); th = Signal(); th_p = Signal()
            tv0 = Signal(); tv = Signal(); tv_p = Signal()
            self.sync += [th0.eq(pads.hs), th.eq(th0), th_p.eq(th),
                          tv0.eq(pads.vs), tv.eq(tv0), tv_p.eq(tv)]
            the = Signal(); tve = Signal()
            self.comb += [the.eq(th_p & ~th), tve.eq(tv_p & ~tv)]
            tch = Signal(32); tcv = Signal(32)
            tlines_now = Signal(16); tlines_cnt = Signal(16)
            tvacc = Signal(24); tvwin = Signal(3)
            self.sync += [
                If(the, tlines_cnt.eq(tlines_cnt + 1)),
                If(tve, tlines_now.eq(tlines_cnt), tlines_cnt.eq(0)),
                If(win == WIN - 1,
                    self.meas_fh_tvp.eq(tch), tch.eq(the),
                    self.meas_lines_tvp.eq(tlines_now),
                    If(tvwin == 7,
                        self.meas_fv_tvp.eq((tvacc + tcv) * 125),
                        tvacc.eq(0), tvwin.eq(0),
                    ).Else(
                        tvacc.eq(tvacc + tcv), tvwin.eq(tvwin + 1),
                    ),
                    tcv.eq(tve),
                ).Else(
                    If(the, tch.eq(tch + 1)),
                    If(tve, tcv.eq(tcv + 1)),
                ),
            ]

            # vfreqは1秒窓のエッジ数だと分解能±1Hz(55.456Hz→55と表示された)。
            # 8秒積算して×125すれば mHz 単位で 0.125Hz 分解能になる。htotal/vtotal と
            # dotclk は1秒窓のままにして応答性(モード変化の検出)を保つ。
            vacc = Signal(24)
            vwin = Signal(3)
            self.sync += If(wait == 1,
                If(vwin == 7,
                    self.meas_vfreq.eq((vacc + vs_stable) * 125),   # mHz
                    vacc.eq(0), vwin.eq(0),
                ).Else(
                    vacc.eq(vacc + vs_stable), vwin.eq(vwin + 1),
                ))

        # --- モード自動追従(垂直) ---
        # 実測 vtotal が安定したら cfg_* に反映する。これをやらないと、モードが
        # 変わったとき自走カウンタのラップ点が合わず、絵が縦に繰り返して見える
        # (実測: 24kHz 1024x424 は vtotal 930。568固定のままだと2枚に割れる)。
        # 位置(vs_row_at_sync)は「VSYNCの何行後から窓を開くか」で持つ。
        # 垂直バックポーチはモードで多少違うが、まず vbp 固定で追従させる。
        # 揺れで書き換え続けないよう、同じ値が連続してから反映する(ヒステリシス)。
        if auto_vtotal:
            # ±1 の違いでは採り直さない。
            #
            # インターレースでは1フィールドが 262.5 ラインなので、VSOUT間のHSOUT数は
            # 262 と 263 を行き来する。どちらに丸まるかは半ライン位相のドリフトで
            # ゆっくり入れ替わり、実測では「263が24回続いた後262が33回続く」といった
            # 塊で観測された。そのまま採用すると塊が変わるたびにモードが切り替わり、
            # スロット割り当てが崩れて未充填523・画面が暗転する(実機で数秒〜十数秒に
            # 一度「ぐらぐらっと揺れる」形で出た)。
            #
            # ±1 は信号の性質であってモード変更ではないので無視する。本物のモード
            # 変更(例 262→525)は2以上動くので従来どおり追従する。
            # ただし「大きい方へは1でも追従する」。
            #
            # cfg_vtotal はフレーム境界の自走カウンタの一周点でもある。実際の
            # フィールドが cfg_vtotal より1行長いと、自走が先に一周して余分な
            # フレーム境界が生まれ、そこに残り1行だけが入った偽フレームができる。
            # 実機では「262行, 262行, 1行」の3つ組が延々と繰り返し、その1行の
            # フレームで受信側の未充填が523になって画面全体が暗転していた。
            # 交互に出る262/263のうち大きい方に張り付けば早回りは起きない。
            #
            # 「連続して同じ値か」の判定は pix 側(meas_vtotal_stable)で
            # フレーム単位に済ませてある。ここは範囲と距離だけを見る。
            # 以前はここで sysクロックを数えており、1秒に1回しか変わらない
            # meas_vtotal に対して常に飽和していたため、単発の異常値(実機で
            # 観測した 210/311/367/1136/2446)がそのまま採用されていた。
            vt_far = Signal()
            self.comb += vt_far.eq((self.meas_vtotal_stable > self.cfg_vtotal)
                                   | (self.meas_vtotal_stable < (self.cfg_vtotal - 1)))
            self.sync += [
                If((self.meas_vtotal_stable >= 100)
                   & (self.meas_vtotal_stable < 1500) & vt_far,
                    self.cfg_vtotal.eq(self.meas_vtotal_stable),
                ),
            ]
            # vbp から導く値は毎サイクル更新する。以前は上の「安定判定が成立した1回」
            # の中で代入していたため、vtotalが安定している間はvbpを変えても何も
            # 起きなかった(実機で発覚)。
            # 組合せにするとsysのレジスタからpixドメインへ減算器を挟んで渡ることに
            # なり、配置次第でタイミングが悪化した(eth_rxが130→116MHzに落ちた)。
            # レジスタのまま毎サイクル更新すれば、1クロック遅れるだけで即座に反映され、
            # pix側は短いレジスタ出力を見るだけで済む。
            vstart = Signal(13)      # 窓の先頭から frame 末尾までの行数
            fstart = Signal(13)      # インターレース時のフィールドあたり有効行数
            vs_row = Signal(13)      # VSYNC検出時に row へ入れる値
            self.comb += [
                vstart.eq(self.cfg_vtotal - self.cfg_vbp),
                fstart.eq(self.cfg_vtotal[1:] - self.cfg_vbp),
                # row に入れる値は vtotal 未満でなければならない。vbp=0 だと
                # vtotal - vbp = vtotal になり、ラップ判定(row == vtotal-1)を
                # 通り越して二度と回らず、フレームが進まなくなって映像が止まる
                # (実機で vbp=0 にして 0fps になった)。0 は「VSYNCが窓の先頭」
                # そのものなので 0 に折り返す。
                If((self.cfg_vbp == 0) | (self.cfg_vbp >= self.cfg_vtotal),
                    vs_row.eq(0),
                ).Else(
                    vs_row.eq(vstart),
                ),
            ]
            self.sync += [
                # VSYNC位相ゲートは vtotal の 3/8。
                #
                # 以前は 3/4 にしていたため、インターレース信号の「フィールド毎に
                # 来るVSYNC」のうち2本目(前のVSYNCから約 vtotal/2 後)が捨てられて
                # いた。すると vtotal が2フィールド分(931など)として測られ、その
                # 大きな vtotal からゲートが更に上がって自己強化する。結果
                # 「1VSYNCに2フィールド入っている」ように見えていた(24kHz
                # 1024x848 で vtotal 931 と測れたのはこれ)。等化パルスは
                # VSYNCの直近に出るので 3/8 でも十分に落とせる。
                self.cfg_vs_min_rows.eq((self.cfg_vtotal >> 2) +
                                        (self.cfg_vtotal >> 3)),
                # 窓の先頭 = VSYNCの vbp 行後
                self.cfg_vs_row_at_sync.eq(vs_row),
                # 窓の長さ(折り返す前の row で数えた行数)= vtotal - vbp
                self.cfg_win_rows.eq(vstart),
                # 送出行数(フィールド内の有効行数) = min(height/2, vtotal - vbp)。
                #
                # 行位置は常に半ライン単位のスロットなので、スロットは最大で
                # vactive*2 になる。バッファの行数を超えないよう上限は height/2。
                # 位置決めが位相ベースになったので、インターレースかどうかで
                # 分岐する必要は無い。
                If(vstart < (height >> 1),
                    self.cfg_vactive.eq(vstart),
                ).Else(
                    self.cfg_vactive.eq(height >> 1),
                ),
            ]

        # 受信側へ「1VSYNC周期あたりのスロット数が vtotal 個か 2×vtotal 個か」を伝える。
        # フレーム単位のインターレース(折り返しあり)のときだけ vtotal 個になる。
        self.il_slot1 = Signal()
        self.comb += self.il_slot1.eq(il_det & il_frame)
        # インターレース判定の内訳(読み出し用)。「織り込まれない」を追うとき、
        # どの材料が0なのかが分からないと切り分けられない。
        #   bit0 il_raw   生VSYNCの半ライン位相が交互か
        #   bit1 raw_ok   生同期が使える状態か
        #   bit2 TVPのP/I検出(38h bit5 の反転)
        #   bit3 il_frame TVPのvtotalが2フィールドを覆っているか
        self.stat_il = Signal(4)
        self.specials += MultiReg(Cat(il_raw, raw_ok, self.cfg_il_detect, il_frame),
                                  self.stat_il, "sys")

        # 報告用の行数。行位置は常に半ライン単位のスロットなので、フィールド内
        # 行数の2倍になる(プログレッシブでも1つ飛びに並ぶだけで範囲は2倍)。
        self.comb += self.out_vactive.eq(Cat(0, self.cfg_vactive))   # = vactive*2

        # ================= sys ドメイン =================
        self.comb += [
            self.line_valid.eq(meta.source.valid),
            self.line_face.eq(meta.source.face),
            self.line_row.eq(meta.source.row),
            self.line_frame.eq(meta.source.frame),
            self.line_field.eq(meta.source.field),
            self.line_ts.eq(meta.source.ts),
            self.line_first.eq(meta.source.x_lo),
            self.line_last.eq(meta.source.x_hi),
            meta.source.ready.eq(self.line_ack),
            rd.adr.eq(Cat(self.rd_word, self.rd_face)),  # 送信側ラッチ面を読む
            self.rd_data.eq(rd.dat_r),
        ]
        # 指定行の範囲を push 時点でラッチ(pixドメイン)。row_eff[:row_bits] は
        # meta.sink.row と同じ値なので、FIFOに載る値そのものを見ていることになる。
        probe_lo = Signal(entry_bits)
        probe_hi = Signal(entry_bits)
        probe_any = Signal()
        self.sync.pix += [
            If(push & (row_eff[:row_bits] == self.cfg_span_probe_row),
                probe_lo.eq(ln_first), probe_hi.eq(ln_last), probe_any.eq(ln_any),
            ),
        ]
        # パルス後しか変化しないのでMultiRegで受けて良い(既存のstat_*と同じ扱い)
        self.specials += MultiReg(Cat(probe_lo, probe_hi, probe_any),
                                 self.stat_span_probe[:2 * entry_bits + 1], "sys")
        # pop した瞬間の先頭の値(sysドメインなのでCDC不要)
        self.sync += [
            If(self.line_ack & meta.source.valid,
                self.stat_pop_probe.eq(
                    Cat(meta.source.x_lo, meta.source.x_hi,
                        meta.source.row[:32 - 2 * entry_bits])),
            ),
        ]
        # 診断CDC
        self.specials += MultiReg(frame, self.cap_frame, "sys")
        self.specials += MultiReg(drops, self.cap_drops, "sys")
        self.specials += MultiReg(vs_x, self.stat_vs_x, "sys")
        self.specials += MultiReg(fid_vs, self.stat_fid, "sys")
