kunichiko/RetroCastX/client/src/protocol.rs

//! RetroCastX protocol v0 (little-endian).
//! Mirror of `host/python/retrocastx/protocol.py` — that file is the reference.

pub const MAGIC: u8 = 0x52;
pub const VERSION: u8 = 0;
pub const DEFAULT_PORT: u16 = 34600;

pub const TYPE_LINE: u8 = 0;
pub const TYPE_MODE: u8 = 1;
#[allow(dead_code)]
pub const TYPE_AUDIO: u8 = 2;
pub const TYPE_INFO: u8 = 3;
pub const TYPE_SUBSCRIBE: u8 = 4;
pub const TYPE_CONFIG: u8 = 5;

pub const PIXFMT_RGB888: u8 = 0;
pub const PIXFMT_RGB555: u8 = 1;
pub const PIXFMT_RGB565: u8 = 2;
/// 生ADC値 2B/px。byte0 = 緑ch 8bit / byte1 = 赤ch 8bit。
///
/// コンポジットを D-SUB の緑ピンに入れる運用では byte0 が CVBS そのもの
/// (byte1 は未接続の赤chなので≒0)。将来のS-Videoでは byte0=Y / byte1=C。
/// RGB555 の5bitではカラーバーストが9コードp-pしか無く副搬送波の位相を
/// 推定できないので、復調するには8bitのまま運ぶ必要がある。
/// 2B/px は RGB555 と同じなので断片化もバッファ確保も共通。
pub const PIXFMT_YC8: u8 = 3;

pub fn bytes_per_px(pixfmt: u8) -> Option<usize> {
    match pixfmt {
        PIXFMT_RGB888 => Some(3),
        PIXFMT_RGB555 | PIXFMT_RGB565 | PIXFMT_YC8 => Some(2),
        _ => None,
    }
}

#[derive(Debug, Clone, PartialEq)]
pub struct Mode {
    pub mode_id: u8,
    pub pixfmt: u8,
    /// bit0 = MFLAG_INTERLACE。織り込み済みかどうかで1VSYNC周期あたりの
    /// スロット数が変わる(織り込み時は1ラインが1スロット、そうでなければ2スロット)
    pub mflags: u16,
    pub hactive: u16,
    pub htotal: u16,
    pub vactive: u16,
    pub vtotal: u16,
    pub dotclk_hz: u32,
    pub hfreq_mhz_x1000: u32,
    pub vfreq_mhz_x1000: u32,
    pub seq: u16,
}

#[derive(Debug)]
pub struct Line<'a> {
    pub frame: u16,
    pub seq: u16,
    #[allow(dead_code)]
    pub flags: u8,
    pub line: u16,
    pub offset_px: u16,
    pub count_px: u16,
    pub pixfmt: u8,
    pub mode_id: u8,
    #[allow(dead_code)]
    pub timestamp: u32,
    pub pixels: &'a [u8],
}

/// AUDIO(type=2): s16le L/R interleaved。timestamp は映像LINEと同一の
/// ドットクロックカウンタ(A/V同期用)。
#[derive(Debug)]
pub struct Audio<'a> {
    pub source: u8,          // 0=RGB端子音声, 1=LINE入力, 2=S/PDIF
    pub format: u8,          // 0=PCM16
    pub nsamples: u16,       // サンプルフレーム数(L+Rで1)
    pub rate_hz: u32,
    pub timestamp: u32,
    pub samples: &'a [u8],
    pub seq: u16,
}

pub const AUDIO_FMT_PCM16: u8 = 0;

#[derive(Debug, Clone)]
pub struct Announce {
    pub mac: [u8; 6],
    pub udp_port: u16,
    pub fw_version: u16,
    pub caps: u16,
    pub name: String,
    pub seq: u16,
}

#[derive(Debug)]
pub enum Packet<'a> {
    Line(Line<'a>),
    Mode(Mode),
    Audio(Audio<'a>),
    Announce(Announce),
    /// CONFIG応答等(共通seq空間の追跡に必要な範囲のみ保持)
    Other { ptype: u8, flags: u8, seq: u16 },
}

fn u16le(d: &[u8], o: usize) -> u16 {
    u16::from_le_bytes([d[o], d[o + 1]])
}

fn u32le(d: &[u8], o: usize) -> u32 {
    u32::from_le_bytes([d[o], d[o + 1], d[o + 2], d[o + 3]])
}

pub fn parse(d: &[u8]) -> Result<Packet<'_>, &'static str> {
    if d.len() < 8 {
        return Err("short datagram");
    }
    if d[0] != MAGIC || d[1] != VERSION {
        return Err("bad magic/version");
    }
    let (ptype, flags, frame, seq) = (d[2], d[3], u16le(d, 4), u16le(d, 6));
    let body = &d[8..];
    match ptype {
        TYPE_LINE => {
            if body.len() < 12 {
                return Err("short LINE packet");
            }
            let count_px = u16le(body, 4);
            let pixfmt = body[6];
            let pixels = &body[12..];
            let bpp = bytes_per_px(pixfmt).ok_or("unknown pixfmt")?;
            if pixels.len() != count_px as usize * bpp {
                return Err("LINE payload size mismatch");
            }
            Ok(Packet::Line(Line {
                frame,
                seq,
                flags,
                line: u16le(body, 0),
                offset_px: u16le(body, 2),
                count_px,
                pixfmt,
                mode_id: body[7],
                timestamp: u32le(body, 8),
                pixels,
            }))
        }
        TYPE_MODE => {
            if body.len() < 24 {
                return Err("short MODE packet");
            }
            Ok(Packet::Mode(Mode {
                mode_id: body[0],
                pixfmt: body[1],
                mflags: u16le(body, 2),
                hactive: u16le(body, 4),
                htotal: u16le(body, 6),
                vactive: u16le(body, 8),
                vtotal: u16le(body, 10),
                dotclk_hz: u32le(body, 12),
                hfreq_mhz_x1000: u32le(body, 16),
                vfreq_mhz_x1000: u32le(body, 20),
                seq,
            }))
        }
        TYPE_AUDIO => {
            if body.len() < 12 {
                return Err("short AUDIO packet");
            }
            let format = body[1];
            let nsamples = u16le(body, 2);
            let samples = &body[12..];
            if format != AUDIO_FMT_PCM16 {
                return Err("unknown audio format");
            }
            // s16le × 2ch = 4B/フレーム
            if samples.len() != nsamples as usize * 4 {
                return Err("AUDIO payload size mismatch");
            }
            Ok(Packet::Audio(Audio {
                source: body[0],
                format,
                nsamples,
                rate_hz: u32le(body, 4),
                timestamp: u32le(body, 8),
                samples,
                seq,
            }))
        }
        TYPE_INFO => {
            if body.len() < 32 {
                return Err("short INFO packet");
            }
            let mut mac = [0u8; 6];
            mac.copy_from_slice(&body[0..6]);
            let name_raw = &body[16..32];
            let name_end = name_raw.iter().position(|&b| b == 0).unwrap_or(16);
            Ok(Packet::Announce(Announce {
                mac,
                udp_port: u16le(body, 10),
                fw_version: u16le(body, 12),
                caps: u16le(body, 14),
                name: String::from_utf8_lossy(&name_raw[..name_end]).into_owned(),
                seq,
            }))
        }
        t => Ok(Packet::Other { ptype: t, flags, seq }),
    }
}

pub const CFG_FLAG_REPLY: u8 = 0x01;

/// 全ボードに向けるワイルドカード宛先MAC(発見用/単一ボードLAN専用)。
pub const WILDCARD_MAC: [u8; 6] = [0xFF; 6];

/// CONFIG(24B): 共通ヘッダ8B + 宛先MAC 6B + 予約2B + target/op/key 4B + value 4B。
/// op: 0=SET(値を書いて現在値を返す), 1=GET(現在値を返す)。
/// target 0 = ボード本体の設定。key は gateware 側と対応:
///   0x0001 音声ソース有効マスク / 0x0010 vbp / 0x0011 hs_offset / 0x0012 pll_divide
pub fn pack_config(
    seq: u16, target: u8, op: u8, key: u16, value: u32, mac: &[u8; 6],
) -> [u8; 24] {
    let mut p = [0u8; 24];
    p[0] = MAGIC;
    p[1] = VERSION;
    p[2] = TYPE_CONFIG;
    p[6..8].copy_from_slice(&seq.to_le_bytes());
    p[8..14].copy_from_slice(mac);
    p[16] = target;
    p[17] = op;
    p[18..20].copy_from_slice(&key.to_le_bytes());
    p[20..24].copy_from_slice(&value.to_le_bytes());
    p
}

pub const CFG_KEY_VBP: u16 = 0x0010;
pub const CFG_KEY_HS_OFFSET: u16 = 0x0011;
pub const CFG_KEY_PLL_DIVIDE: u16 = 0x0012;
/// インターレース方式。0=なし / 1=1回のVSYNCにフィールドが2枚 /
/// 2=フィールドごとにVSYNC(標準的なインターレース)
pub const CFG_KEY_INTERLACE: u16 = 0x0013;
/// 第2フィールドが始まる row。0 なら vtotal/2 を使う
pub const CFG_KEY_F2_ROW: u16 = 0x0014;
/// フィールドの偶奇を入れ替える(どちらが偶数ラインかは信号から分からない)
pub const CFG_KEY_FIELD_SWAP: u16 = 0x0015;
/// 方式2のフィールド極性の取得元。0=VSYNCの水平位相 / 1=TVP7002のFIDOUT
pub const CFG_KEY_FIELD_SRC: u16 = 0x0016;
/// TVP7002のアナログ映像帯域(レジスタ0x3F)。0=最大(既定) 〜 15=最小(約95MHz)
pub const CFG_KEY_VIDEO_BW: u16 = 0x0017;
/// サンプリング位相 0..31(TVPの04h bit[7:3])。1ドット周期の1/32刻みで、
/// ADCがドットのどこを掴むかを決める。ずれると全画素が一様にぼける。
/// 最適値はモードごとに変わる(遅延は固定[ns]だがこの刻みはドット周期に比例)。
pub const CFG_KEY_PHASE: u16 = 0x001F;
/// 1ラインまるごと送る(非黒範囲の最適化を切る)。0=通常 / 1=全ライン。
///
/// 診断用に入れたが、実用上の回避策にもなっている。全黒行が続いた直後の数行の
/// 範囲判定が壊れて行が欠ける不具合があり、これを1にすると範囲を使わないので
/// 完全に消える。帯域は 1ライン=htotal画素ぶんに増える(31kHzで約555Mbps)。
/// 個体設定(ボード名 / 静的IP)。実体は基板のEUI-48 EEPROMの空き領域。
/// **SETは即座に効き、`IDENT_SAVE` で焼くまでは電源で消える**(試してから決められる)。
pub const CFG_KEY_NET_MODE: u16 = 0x0046;   // bit0=静的IPを使う(0=リンクローカル)
pub const CFG_KEY_STATIC_IP: u16 = 0x0047;  // ネットワークバイト順の整数
/// ボード名16バイトを4語に分けたもの(UTF-8, NUL詰め, 各語リトルエンディアン)。
pub const CFG_KEY_NAME0: u16 = 0x0048;
pub const CFG_KEY_NAME1: u16 = 0x0049;
pub const CFG_KEY_NAME2: u16 = 0x004A;
pub const CFG_KEY_NAME3: u16 = 0x004B;
/// SET 1=EEPROMへ焼く / GET 0=未実行 1=実行中 2=成功 3=失敗
pub const CFG_KEY_IDENT_SAVE: u16 = 0x004C;
/// bit0=妥当な設定ページがあった bit2:1=1未設定/2破損/3EEPROM無応答(読専)
pub const CFG_KEY_IDENT_EE: u16 = 0x004D;

pub const CFG_KEY_FULL_LINE: u16 = 0x0030;
/// フレーム間引き。0=毎フレーム / 1=2フレームに1回 / 2=3回に1回…
///
/// 低スペックな受信機で取りこぼす場合の保険。映像(LINE)だけを間引き、音声は
/// 間引かないので、同じ受信キューを共有している音声の取りこぼしも減る。
/// ボード側では push の段階で落とすので、FIFOにも面にも載らない。
pub const CFG_KEY_FRAME_SKIP: u16 = 0x0035;
/// 伝送ピクセル形式。1=RGB555(既定) / 3=YC8(生8bit。コンポジット/S-Video用)。
/// YC8にするとボード側で「黒でない範囲」の最適化が自動的に切れ、
/// 1ライン=htotal画素まるごと届く(ブランキングもバーストも中身なので)。
pub const CFG_KEY_PIXFMT: u16 = 0x0036;
/// 非黒判定の閾値(成分の上位5bit と比較, 0..31)。既定0。
/// ★上げると**暗い絵の中身が送出範囲から外れて送られなくなる**。
/// 閾値2で X68000 の32階調の下2段が消えていた(2026-09-03 実測)。
pub const CFG_KEY_BLACK_TH: u16 = 0x0037;
/// インターレースのフィールド極性を入れ替える(0/1)。
///
/// 捕捉側は「生VSYNCがラインの中央付近に来たフィールドは半ライン分あとから
/// 始まる = 1スロット下」で偶奇を決める。その符号がどちら向きかは配線と
/// 同期の極性で決まるので、映像ソースごとに実測で決める。
///
/// ★X68000は 1(反転)が正しい。2026-09-03 に24kHz 1024x848 で実測:
///   織り込みのずれが 0=17.5 / 1=0.68 と**25倍**違った。VSOUTがフレーム単位
///   (reg22h=0x08、折り返しあり)でもフィールド単位(0x09、折り返しなし)でも
///   同じ結論だったので、折り返しとの相対関係ではなく生位相の符号そのもの。
pub const CFG_KEY_FIELD_INVERT: u16 = 0x0066;
/// H-PLL制御(TVPレジスタ03h)。VCOレンジ[7:6] + チャージポンプ電流[5:3]。
/// ピクセルクロックとpixels per lineから決まるので、モードごとに計算して送る
pub const CFG_KEY_PLL_CTL: u16 = 0x0019;

// --- 映像ソース(入力方式)の切替に要るキー。profiles.rs の input_regs で使う ---
//
// 値の意味と根拠は host/python/retrocastx/protocol.py と
// gateware/retrocastx_i2c.py のコメントにある。**あちらが正**。

/// TVPのクランプ開始位置(レジスタ05h)[DATACLK]
pub const CFG_KEY_CLAMP_START: u16 = 0x001A;
/// TVPのクランプ幅(レジスタ06h)[DATACLK]
pub const CFG_KEY_CLAMP_WIDTH: u16 = 0x001B;
/// 細ゲイン Blue(レジスタ08h)。Gain = 1 + N/256 で**下げられない**
pub const CFG_KEY_GAIN_B: u16 = 0x001C;
/// 細ゲイン Green(レジスタ09h)
pub const CFG_KEY_GAIN_G: u16 = 0x001D;
/// 細ゲイン Red(レジスタ0Ah)
pub const CFG_KEY_GAIN_R: u16 = 0x001E;
/// TVP同期制御(レジスタ0Eh)。0x52=HSYNC/VSYNCを別線で受ける / 0x5B=HもVもSOGから
pub const CFG_KEY_SYNC_CTL: u16 = 0x0022;
/// 同期処理制御(TVPレジスタ22h)。既定 08h。**bit0 = VS Bypass。**
///
/// 0 だと「同期セパレータの活動が無いときはハーフライン積算器が VSOUT を作る」
/// 条件分岐が働き、VSOUTが**2フィールドに1回**しか出なくなることがある。
/// 1 にすると VSOUT が同期セパレータ直結になり、フィールドごとに出る。
///
/// ★X68000は 0x09(bit0=1)が正しい。2026-09-03 に24kHz 1024x848 で実測:
///
/// ```text
///     0x08 (フレーム単位) 織り込みのずれ 4.84 / 4.95 / 4.59
///     0x09 (フィールド単位)            1.44 / 1.44 / 1.39
/// ```
///
/// フレーム単位だと捕捉側が vtotal/2 = 465 で折り返すが、実際のフィールド長は
/// 半ラインのぶん 465 と 466 で1行違うので、片方が必ず1行ずれる。フィールド単位
/// ならそれぞれのVSYNCで位置が決まるので折り返しが要らない。
/// 注: VSOUTの遅延が reg 11h に依存するようになり reg 35h は無効になるので、
/// 縦位置(vbp)を合わせ直す必要があるかもしれない。
pub const CFG_KEY_SYNC_CTL2: u16 = 0x005B;
/// レジスタ1Ah bit[7:6]=SOG LPF bit[5:4]=クランプLPF。
/// 既定C2hはHDTV向け。15kHz機は 0x12(SOG 2.5MHz + クランプ 0.5MHz)が適正
pub const CFG_KEY_IN_MUX2: u16 = 0x005D;
/// レジスタ10h bit[2:0] bit2=Blue bit1=Green bit0=Red。0=ボトム / 1=ミッドレベル。
/// RGB入力は 0b000 / コンポジットは 0b010(Greenのみミッド=バーストを丸ごと入れる)
pub const CFG_KEY_CLAMP_SEL: u16 = 0x005E;
/// レジスタ1Bh [7:4]=Green [3:0]=Blue、Gain = 0.5 + N/10
pub const CFG_KEY_COARSE_GAIN_GB: u16 = 0x005F;
/// レジスタ1Fh bit[5:0] 粗アナログオフセット Green
pub const CFG_KEY_COARSE_OFF_G: u16 = 0x0065;
/// レジスタ1Ch 粗アナログゲイン Red。**1Bhとビット割りが違う**
/// ([7:4]=Reserved [3:0]=N)。同じ1.2倍でも 1Bh=0x77 / 1Ch=0x07
pub const CFG_KEY_COARSE_GAIN_R: u16 = 0x0067;
/// レジスタ20h bit[5:0] 粗アナログオフセット Red
pub const CFG_KEY_COARSE_OFF_R: u16 = 0x0068;
/// レジスタ10h bit[7:3] SOGスライス閾値(5bit)。**同期をどの高さで切るか。**
///
/// ★S端子で実測(2026-08-15): 既定 0x0B では暗い映像を同期と誤認して垂直検出が
///   壊れ、フィールド極性が判定できずに絵が半ライン上下に震えた。16〜24 が
///   正しい窓で、その中央の 20 にすると垂直間隔が 262/263 に安定する。
pub const CFG_KEY_SOG_THRESH: u16 = 0x0050;

/// レジスタ37h:38h。**TVP自身が数えた1フレームのライン数。**
/// 読み出し専用。SOGスライス閾値を振ったときの合否はこれで見る
/// (15.7kHz系なら 262/263 に収束するのが正しい。閾値が低すぎて暗部を同期と
/// 誤認していると、ここが 1 になったり値が暴れたりする)。
pub const CFG_KEY_LINES_PER_FRAME: u16 = 0x0055;

/// レジスタ38h の生値。読み出し専用。**bit5 = P/I detect(0=インターレース)**。
pub const CFG_KEY_LPF_MSBS: u16 = 0x0057;

/// インターレース判定の内訳(読み出し専用、4bit)。**「織り込まれない」ときに
/// どの材料が 0 なのかを見るためのもの。** 捕捉側の `fld_pos` はこれらで決まる:
///
/// ```text
///   bit0 il_raw       生VSYNCの半ライン位相が交互か
///   bit1 raw_ok       生同期(TTL)が使える状態か
///   bit2 il_detect    TVPのP/I検出(38h bit5 の反転。1=インターレース)
///   bit3 il_frame     TVPのvtotalが2フィールドを覆っているか
/// ```
pub const CFG_KEY_STAT_IL: u16 = 0x002D;

/// SOGOUTの水平周期[pixクロック]。読み出し専用
pub const CFG_KEY_SOG_HLEN: u16 = 0x0060;

/// 生同期(TTL)の位相をフィールド極性の判定に使わない。0=使う(既定) / 1=使わない。
///
/// ★**生同期を繋がない入力方式(コンポジット/S端子/MSX)では 1 にする。**
///   未接続のシュミットバッファ入力は浮いて自己発振し、捕捉側の `raw_ok` が
///   誤って立つ。すると**存在しない同期の位相**でフィールド極性が決まり、
///   極性が交互にならないので両フィールドが同じスロットに交互に上書きされ、
///   絵が1ライン上下に震える(実機 2026-09-06、コンポジット480i:
///   `il: raw0 rawok1 P/I1 frame0` / `SOG lowmax 773` = SOG側は健全だった)。
///   **1 にして直ることを同日に実機で確認**。震えが消え、有効映像の高さが
///   217/240 → 432 になった(織り込みが成立した)。`rawok` は 1 のままなので、
///   効いたかどうかは `rawok` ではなく織り込みの成立で判断すること。
pub const CFG_KEY_NO_RAW_PHASE: u16 = 0x006A;

/// 直近で見た SOGOUT の最長Low期間[pixクロック]。読み出し専用。
///
/// ★**捕捉側の `sog_ok` はこれを使う**(`lowmax > 100 && lowmax < 0x8000`)。
///   飽和(65535)すると SOG からフィールド極性を取る経路が丸ごと落ちて、
///   両フィールドが同じスロットに書かれる。
pub const CFG_KEY_SOG_LOWMAX: u16 = 0x0061;

/// SOGOUTのLow期間を「垂直ブロードパルス」とみなす閾値[pixクロック]。既定400。
///
/// ★**既定は MSX(DATACLK 21.48MHz)で決めた値。** NTSC 8fsc(28.6356MHz)では
///   水平同期 4.7µs ≈ 135クロック / 垂直ブロードパルス 27µs ≈ 776クロックなので、
///   その間に入っていればよい。映像源で幅が違うので実行時に振れる。
pub const CFG_KEY_SOG_VTH: u16 = 0x0064;

/// レジスタ19h [7:6]=SOG [5:4]=R [3:2]=G [1:0]=B、00=_1 / 01=_2 / 10=_3。
/// v0.9.0 は入力ごとに系統が分かれているので**全ビット同じ値**になる:
/// 0x00=S端子/コンポジット(J5) / 0x55=第2入力(aux 2x5) / 0xAA=D-SUB。
/// **入力方式の切替に必須**(手組み機では「SOGだけ_2」= 0x6A が要った)
pub const CFG_KEY_IN_MUX1: u16 = 0x0069;

/// SUBSCRIBE(16B): 共通ヘッダ8B + 宛先MAC 6B + 予約2B。
/// mac で宛先ボードを指名する(WILDCARD_MAC で全ボード)。
pub fn pack_subscribe(seq: u16, announce_only: bool, mac: &[u8; 6]) -> [u8; 16] {
    let mut p = [0u8; 16];
    p[0] = MAGIC;
    p[1] = VERSION;
    p[2] = TYPE_SUBSCRIBE;
    p[3] = if announce_only { 1 } else { 0 };
    p[6..8].copy_from_slice(&seq.to_le_bytes());
    p[8..14].copy_from_slice(mac);
    p
}

#[cfg(test)]
pub mod testutil {
    //! Packet builders for tests (mirror of the Python pack_* functions).
    use super::*;

    pub fn pack_line(
        frame: u16, seq: u16, line: u16, offset_px: u16, pixfmt: u8, mode_id: u8,
        timestamp: u32, pixels: &[u8],
    ) -> Vec<u8> {
        let bpp = bytes_per_px(pixfmt).unwrap();
        assert_eq!(pixels.len() % bpp, 0);
        let count_px = (pixels.len() / bpp) as u16;
        let mut p = vec![MAGIC, VERSION, TYPE_LINE, 0x01];
        p.extend_from_slice(&frame.to_le_bytes());
        p.extend_from_slice(&seq.to_le_bytes());
        p.extend_from_slice(&line.to_le_bytes());
        p.extend_from_slice(&offset_px.to_le_bytes());
        p.extend_from_slice(&count_px.to_le_bytes());
        p.push(pixfmt);
        p.push(mode_id);
        p.extend_from_slice(&timestamp.to_le_bytes());
        p.extend_from_slice(pixels);
        p
    }

    /// AUDIO(PCM16)。samples は s16le の L,R インターリーブ
    pub fn pack_audio(seq: u16, source: u8, rate_hz: u32, samples: &[u8]) -> Vec<u8> {
        assert_eq!(samples.len() % 4, 0);
        let mut p = vec![MAGIC, VERSION, TYPE_AUDIO, 0];
        p.extend_from_slice(&0u16.to_le_bytes());
        p.extend_from_slice(&seq.to_le_bytes());
        p.push(source);
        p.push(AUDIO_FMT_PCM16);
        p.extend_from_slice(&((samples.len() / 4) as u16).to_le_bytes());
        p.extend_from_slice(&rate_hz.to_le_bytes());
        p.extend_from_slice(&0u32.to_le_bytes());
        p.extend_from_slice(samples);
        p
    }

    pub fn pack_mode(m: &Mode, frame: u16, seq: u16) -> Vec<u8> {
        let mut p = vec![MAGIC, VERSION, TYPE_MODE, 0];
        p.extend_from_slice(&frame.to_le_bytes());
        p.extend_from_slice(&seq.to_le_bytes());
        p.push(m.mode_id);
        p.push(m.pixfmt);
        p.extend_from_slice(&m.mflags.to_le_bytes());
        p.extend_from_slice(&m.hactive.to_le_bytes());
        p.extend_from_slice(&m.htotal.to_le_bytes());
        p.extend_from_slice(&m.vactive.to_le_bytes());
        p.extend_from_slice(&m.vtotal.to_le_bytes());
        p.extend_from_slice(&m.dotclk_hz.to_le_bytes());
        p.extend_from_slice(&m.hfreq_mhz_x1000.to_le_bytes());
        p.extend_from_slice(&m.vfreq_mhz_x1000.to_le_bytes());
        p
    }
}

#[cfg(test)]
mod tests {
    use super::*;

    #[test]
    fn subscribe_roundtrip_shape() {
        let mac = [0x02, 0x52, 0x43, 0x58, 0x00, 0x01];
        let p = pack_subscribe(7, true, &mac);
        assert_eq!(&p[..4], &[MAGIC, VERSION, TYPE_SUBSCRIBE, 1]);
        assert_eq!(u16le(&p, 6), 7);
        assert_eq!(&p[8..14], &mac);
        // ワイルドカードも parse できる形であること(受信側では自身は判定しないが)
        let w = pack_subscribe(0, false, &WILDCARD_MAC);
        assert_eq!(&w[8..14], &[0xFF; 6]);
    }

    #[test]
    fn parse_line() {
        let pixels = [1u8, 2, 3, 4, 5, 6];
        let d = testutil::pack_line(9, 10, 11, 0, PIXFMT_RGB888, 1, 0xDEADBEEF, &pixels);
        match parse(&d).unwrap() {
            Packet::Line(l) => {
                assert_eq!((l.frame, l.seq, l.line, l.count_px), (9, 10, 11, 2));
                assert_eq!(l.timestamp, 0xDEADBEEF);
                assert_eq!(l.pixels, &pixels);
            }
            _ => panic!("wrong type"),
        }
    }

    #[test]
    fn parse_mode() {
        let m = Mode {
            mode_id: 1, pixfmt: PIXFMT_RGB555, mflags: 0,
            hactive: 512, htotal: 655, vactive: 512, vtotal: 542,
            dotclk_hz: 10_650_300, hfreq_mhz_x1000: 16_260_000,
            vfreq_mhz_x1000: 30_000, seq: 3,
        };
        let d = testutil::pack_mode(&m, 0, 3);
        match parse(&d).unwrap() {
            Packet::Mode(got) => assert_eq!(got, m),
            _ => panic!("wrong type"),
        }
    }
}
