kunichiko/RetroCastX/client/src/ntsc.rs

//! NTSCコンポジットの復調(Y/C分離 + 直交復調)。
//!
//! `host/python/retrocastx/ntsc.py` の移植。**あちらが仕様の正**で、合成6色に
//! 対する回帰試験(`tests/test_ntsc.py`、誤差2.1°以内)もあちらにある。
//! ここを直したら向こうも直すこと。
//!
//! ## なぜ 8fsc だと軽いか
//!
//! サンプルレートが副搬送波のちょうど8倍なので、`cos(2πn/8)` は
//! `n mod 8` の8点しか取らない。位相基準はライン毎のバーストから決まるので、
//! **1サンプルあたり積和2回**で直交復調できる。テーブルすら小さい。
//!
//! 実測の負荷: 1820サンプル × 262行 × 59.94フィールド/秒 = 28.6 MSa/s。
//! 1サンプルあたり20〜30演算なので 0.6〜0.9 G演算/秒。
//!
//! ## コムのペアは測って決める
//!
//! NTSCは227.5周期/ラインなので、**時間的に隣のライン**とは位相が180°ずれる。
//! ところがフレームバッファの行番号は「フィールド内の行×2 + 極性」なので、
//! 1フィールドだけ来ている間は**奇数行(または偶数行)だけ**が埋まり、
//! 時間的に隣なのは N と N±2 になる。織り込み設定によっても変わる。
//!
//! なので**行番号の差1と2の両方で位相差を測り、180°に近い方を採る**。
//! 決め打ちにすると設定が変わった瞬間に色が消える(コムが同位相の行を引く)。

/// バースト区間 [µs]。同期立ち下がりを0とする
const BURST_US: (f32, f32) = (5.4, 7.7);
/// 同期チップとバックポーチ(レベル校正に使う。絵の内容に依存しない)
const TIP_US: (f32, f32) = (0.7, 4.2);
const PORCH_US: (f32, f32) = (7.9, 9.3);
/// 有効映像の区間 [µs]。**この外は黒にする。**
///
/// ★実機で管面の左端に細い緑の帯が出た(実測 R2.5 / G21 / B0)。カラーバーストを
///   そのまま復調した色だった。バーストは輝度0 IREのところに色だけ乗っているので、
///   RGBに直すと R と B が0にクランプされて G だけ残る。
///   実際のブラウン管はこの区間ビームが消えているので何も映らない。
///   管面は時間で窓を決めるので、窓を広げると帰線区間まで映ってしまう。
///   生の波形を見たいときは「復調しない(生のYを見る)」を使う。
///
/// ★**幅はビデオデッキの HDMI 出力に合わせてある**(2026-10-09 実測)。白黒の
///   格子パターンで、中央の点を目印に同じ物差しで比べると、デッキは
///   9.95〜60.87µs(50.9µs)を映していて、**中心が中央の点にぴったり**だった。
///   以前の (9.6, 62.0) は規格上の有効区間ほぼいっぱいで、中心が 0.35µs 右へ
///   ずれ、右端はデッキに無い縦線まで見えていた。
///   表示側の初期の管面(main.rs の `MON_NTSC`)もこの窓と同じにしてある。
///
/// ★左端がチラつくのを見て、一度は窓を 10.4µs まで詰めた。**原因は窓ではなく
///   TVPのクランプ窓が映像の頭に食い込んでいたこと**だった(profiles.rs の
///   CLAMP_START の注記)。ラインの頭が半分の明るさになり、その終わりが
///   フレームごとに動いていた。ジェネレータの信号の揺れと誤読しかけたが、
///   デッキは同じ時刻を真っ白で安定して出していた。クランプを直せば
///   デッキと同じ幅で揺れない。
pub const ACTIVE_US: (f32, f32) = (9.95, 60.87);

/// クロマの移動平均長[サンプル]。**8の倍数にすること。**
///
/// 直交復調の積には必ず 2fsc 成分が出る。8の倍数で平均するとちょうど整数周期
/// ぶん入って完全に消える。適当な窓長だと色に細かい縞が残る。
const CHROMA_LPF: usize = 16;

/// 3次元コムで「動いている」と判定する輝度の時間差[IRE]。
///
/// 動き検出には **2 NTSCフレーム前**(位相0°でクロマが消える)を使う。
/// 1フレーム前は位相180°なのでクロマがそのまま差に出て、**色のある所が全部
/// 「動いている」ことになる**(実測で副搬送波成分が 388 対 9315)。
///
/// 実測の動き量の分布は 中央値 2.3 IRE / 90%点 4.7 / 最大 52.3 で、ノイズ床が
/// 2〜4 IRE。閾値をノイズ床より下にすると常に2次元へ落ちて意味が無くなる。
const MOTION_IRE: f32 = 8.0;

/// 動き量のうち「動きではない」とみなす分[IRE]。これを超えた分だけで
/// 2次元へ寄せる(MOTION_IRE で完全に2次元)。
///
/// ★以前は `a = 動き量 / MOTION_IRE` で**0から比例**させていたので、雑音だけの
///   静止部分でも 1〜2割、カラーバーの境界では最大7割ほど2次元が混ざっていた
///   (実測 2026-10-09)。2次元の輝度は境界でクロマを引き残すので、それが
///   フレームごとに反転してちらついた。サンプル位置の揺れを補正した後の
///   静止部分の動き量は 99%点で 1.7コード(≒1.9 IRE)なので、その上に置く。
const MOTION_CORE_IRE: f32 = 3.0;

/// 2次元で輝度から引くクロマを選ぶ「縦の変化」(上下の行の差)[IRE]。
/// LO 以下なら2次元コムのクロマ(境界まで正確)、HI 以上なら帯域制限した再変調
/// (横棒を上下に広げない)。間は線形に混ぜる。
const VDETAIL_LO_IRE: f32 = 3.0;
const VDETAIL_HI_IRE: f32 = 10.0;

/// バーストが取れたと判定する相関の下限。これ未満の行は無彩色にする。
///
/// ★真っ黒な領域では相関が雑音になり、**色相が乱数になる**(実測: 彩度0.03〜0.09の
///   行で色相が230〜300°をふらついた)。無彩色に倒す方が絵として正しい。
const BURST_MIN: f32 = 60.0;

/// S端子と判定する「Cチャネルのバースト / バックポーチ」比の下限。
///
/// 実測(コンポジット、赤ch未接続)で 1.0 前後、バーストが載っていれば数十になる
/// ので、間は大きく空いている。
const SVIDEO_SNR_MIN: f32 = 6.0;

/// 白黒として出すのに要る同期の深さ(バックポーチ − 同期チップ)[コード]。
///
/// バーストが無いときは同期だけが頼りなので、同期が見えていない(無信号、
/// 横位置が大きくずれている)ときに無理に校正すると、ゲインが暴れて
/// 雑音を全面に引き伸ばした絵になる。そのときは生のYを残す。
const MONO_SYNC_MIN: f32 = 10.0;

/// フレームコムの位相ズレ補正で受け付ける ε の上限[度]。
///
/// 実測の |ε| は中央値 4.8°、滑らかに±15°を揺れる程度。これを大きく超える値は
/// バーストの測り損ね(暗い行、欠損行)なので、補正を掛けない方が安全。
/// tan(ε/2) が暴れると 3次元の枝ごと壊れる。
const PHASE_FIX_MAX_DEG: f32 = 30.0;

pub struct Info {
    pub lines_locked: u32,
    pub comb_step: usize,
    pub phase_delta_deg: f32,
    pub code_per_ire: f32,
    /// 3次元(動き適応フレームコム)を使えた行数
    pub lines_3d: u32,
    /// そのうち「動いている」と判定した画素の割合(0..1)
    pub motion_frac: f32,
    /// 赤ch(C)にバーストが載っていた = S端子として復調した。
    /// このときコムは一切使わない(Y と C が最初から別々に来ているため)。
    pub svideo: bool,
    /// バーストが無いので白黒として出した(レベル校正だけ掛けた Y)。
    /// 白黒のパターンジェネレータなど。テレビのカラーキラーと同じ扱い
    pub mono: bool,
    /// TBC で並べ直した量(行ごとのずれの二乗平均平方根)[サンプル]。
    /// 取り込み位置の揺れの大きさそのもの。0 なら並べ直していない
    pub tbc_rms: f32,
    /// 1 NTSCフレーム前との副搬送波位相のズレ |ε| の中央値[度]。
    /// これがフレームコムの消し残し(= フレームごとに反転するドットクロール)を
    /// 決める。残留は C·sin(ε/2)。
    pub phase_drift_deg: f32,
}

fn win(us: (f32, f32), sps: f32, w: usize) -> (usize, usize) {
    let a = (us.0 * 1e-6 * sps) as usize;
    let b = (us.1 * 1e-6 * sps) as usize;
    (a.min(w), b.min(w))
}

fn median(v: &mut [f32]) -> f32 {
    if v.is_empty() {
        return 0.0;
    }
    v.sort_by(|a, b| a.partial_cmp(b).unwrap_or(std::cmp::Ordering::Equal));
    v[v.len() / 2]
}

/// -180..180 に畳んだ角度差[度]
fn ang_diff(a: f32, b: f32) -> f32 {
    let mut d = (a - b) % 360.0;
    if d > 180.0 {
        d -= 360.0;
    }
    if d < -180.0 {
        d += 360.0;
    }
    d
}

/// 1フィールドを復調して `fb`(RGBA)へ書く。
///
/// `raw` は 2バイト/サンプル(下位=緑ch=CVBS、上位=赤ch。コンポジットでは赤は未使用)。
/// `filled[y]` がそのラインを受信したか。受信していない行は触らない
/// (呼び出し側の欠損補間・減衰に任せる)。
/// 3次元コム用の履歴。`p2` は1 NTSCフレーム前(位相180°)、`p4` は2フレーム前
/// (位相0°、動き検出用)。`hist_n[y] >= 3` の行だけ3次元を使う。
/// 見た目の調整。**復調の正しさとは別に持つ。**
///
/// 信号内の基準(同期40 IRE / バースト40 IRE p-p / 黒0 IRE / 白100 IRE)に合わせた
/// 結果が「正しい」絵で、既定値はそこを指す。ここはその上に載せる好みの調整で、
/// 復調の校正を触らない(校正を歪めると、後で数値で追えなくなる)。
#[derive(Clone, Copy, Debug, PartialEq)]
pub struct Adjust {
    /// 色相[度]。NTSCの tint。バースト位相にそのまま足す
    pub hue_deg: f32,
    /// 彩度。1.0 = 信号どおり
    pub saturation: f32,
    /// 明るさ[IRE]。黒レベルを上下する
    pub brightness: f32,
    /// コントラスト。1.0 = 信号どおり。輝度と色差の両方に掛ける
    /// (色差に掛けないと、コントラストを上げたとき色が薄く見える)
    pub contrast: f32,
    /// ガンマ。1.0 = 信号どおり(素通し)。出力を `v^(1/gamma)` にする。
    ///
    /// ★**1.0 が正しい。素通しが正解で、ここは好みの調整。**
    ///
    /// ## なぜ素通しが正しいか(「ブラウン管のガンマを補正すべき」は誤り)
    ///
    ///     被写体の光(リニア)
    ///       → カメラの OETF ≈ v^(1/2.2) で符号化   ← 信号は既にガンマ済み
    ///       → コンポジット/S端子はこの符号化済みの値を運ぶ
    ///       → ブラウン管の EOTF ≈ 2.2〜2.5 で復号 → 光
    ///
    /// **符号化は最初からブラウン管のガンマを見越して掛けられている。** 受け側で
    /// 改めて補正するものではない。そして現代の液晶(sRGB)も同じ EOTF ≈ 2.2 を
    /// 意図的に実装しているので、符号化済みの値をそのまま8bitへ書けば液晶が
    /// ブラウン管の代わりを務める。
    ///
    /// もし本当にブラウン管ガンマを補正(リニア化)したら、sRGB表示でもう一度2.2が
    /// 掛かって**暗くなる**。持ち上がる方向にはならない。
    ///
    /// 厳密にはブラウン管の EOTF は2.4〜2.5で、符号化が1/2.2なので系全体のガンマは
    /// 1.1〜1.2 になる。これは意図的(暗い部屋での dim surround 補償)。sRGB液晶で
    /// 素通しすると系全体は1.0なので、**ブラウン管より気持ち平坦**になる。
    ///
    /// ## 実測(2026-08-15)と、その**帰属の訂正**(2026-09-03)
    ///
    /// 同じ画面のYouTube版と分位で比べると、端点(黒0・白255)は一致し中間だけ違った。
    /// v^(1/g) を当てはめると **g=2.2 で9点すべてが平均誤差1.8コード**で一致した。
    ///
    /// 当時は「**あちら**が符号化済みの値をリニアとして扱って二重に符号化した絵
    /// (washed out)」と結論した。★**これは帰属が逆だった。暗かったのはこちら。**
    ///
    /// 2026-09-03、映像テクスチャを `Rgba8UnormSrgb` 決め打ちで作っていたため、
    /// 描画先が非sRGBのとき**サンプル時の sRGB→リニア復号だけが残る**バグを
    /// 見つけた(render::video_tex_format で修正)。実測でフレームバッファの
    /// 8/16/24/32/41/49/57 が画面上で 1/1/2/4/6/8/11 になっていた。
    /// **sRGB→リニアの曲線はガンマ2.2相当**で、上の「9点が誤差1.8コードで一致」は
    /// 偶然ではなくこのバグの指紋だった。窓経路がこのテクスチャを使い始めたのは
    /// 2026-08-09(EguiBlit 導入)で、ガンマを足した 08-15 の6日前にあたる。
    ///
    /// つまり YouTube 版が正しく、こちらが2.2ぶん暗かった。**ガンマを 1.2〜1.6 に
    /// 上げると暗部が見える」という当時の実用上の助言も、実際には自分のバグの
    /// 相殺だった。** 修正後は既定の 1.0 で32階調が8刻みに並ぶことを実機で確認済み。
    ///
    /// 素通しが正しいという上の議論そのものは変わらない。変わったのは
    /// 「観測された2.2の差を誰のせいにするか」だけ。
    /// ★**測った差を相手のせいにする前に、自分の出力経路を疑うこと。**
    pub gamma: f32,
}

impl Default for Adjust {
    fn default() -> Self {
        Self { hue_deg: 0.0, saturation: 1.0, brightness: 0.0, contrast: 1.0,
               gamma: 1.0 }
    }
}

pub struct History<'a> {
    pub p2: &'a [u8],
    pub p4: &'a [u8],
    pub hist_n: &'a [u8],
}

/// 1ラインの区間 [x0,x1) から (振幅, cos成分, sin成分) を測る。
///
/// `ch` は 0=緑ch(CVBS または Y) / 1=赤ch(S端子の C)。
/// バーストが `A·cos(2π(n-x0)/8 - φ)` と表せる φ を `si.atan2(ci)` で得る。
fn burst(row: &[u8], x0: usize, x1: usize, ch: usize) -> (f32, f32, f32) {
    let mut mean = 0.0f32;
    for n in x0..x1 {
        mean += row[n * 2 + ch] as f32;
    }
    mean /= (x1 - x0) as f32;
    let (mut ci, mut si) = (0.0f32, 0.0f32);
    for n in x0..x1 {
        let v = row[n * 2 + ch] as f32 - mean;
        let k = (n - x0) & 7;
        ci += v * COS8[k];
        si += v * SIN8[k];
    }
    ((ci * ci + si * si).sqrt(), ci, si)
}

/// `burst` の浮動小数版(TBC で並べ直した行を測る)。
fn burst_f(row: &[f32], x0: usize, x1: usize) -> (f32, f32, f32) {
    let mean = row[x0..x1].iter().sum::<f32>() / (x1 - x0) as f32;
    let (mut ci, mut si) = (0.0f32, 0.0f32);
    for n in x0..x1 {
        let v = row[n] - mean;
        let k = (n - x0) & 7;
        ci += v * COS8[k];
        si += v * SIN8[k];
    }
    ((ci * ci + si * si).sqrt(), ci, si)
}

/// TBC(タイムベース補正)で受け付ける1行のずれの上限[サンプル]。
/// 実測の揺れは標準偏差 0.06〜0.1、最大 0.4 程度。これを大きく超えるのは
/// バーストの測り損ね(暗い行・欠損)なので、その行は並べ直さない。
const TBC_MAX_SAMPLES: f32 = 1.0;

/// 緑ch(CVBS)を浮動小数の1面に取り出し、`tbc` なら**行ごとの取り込み位置の
/// 揺れをバーストの位相で測って並べ直す**。`rows` の行だけを扱う。
///
/// ★DATACLK は HSYNC に PLL でロックしているので、行ごとに取り込み位置が
///   揺れる(実測 2026-10-09: 2フレーム前との横ずれが標準偏差 0.10サンプル、
///   最大 0.39。隣の行とは相関 0.77、8行離れるとほぼ無相関)。絵そのものが
///   行ごとに横へ動くので、色の境界では色の混ざり方が変わってちらつく。
///   ジェネレータの副搬送波は安定しているので、**バーストの位相のずれが
///   そのまま取り込み位置のずれ**になる(8fsc で 45°/サンプル。絵から測った
///   ずれとの相関 0.91)。各行を「フィールド内の基準位相」に揃えるように
///   3次補間でずらすと、2フレーム前との横ずれは 0.10 → 0.042サンプルになった
///   (録った生信号での試算)。
///
///   基準は全行の位相を **180°を法として**平均したもの(2φ の円周平均)。
///   隣の行は副搬送波が180°反転しているので、行番号の偶奇に頼らずに済む。
///   行ごとの位相の傾き(副搬送波と fH の比のずれ)は実測 0.01°/行程度で
///   無視できる。フィールド上部の決まった曲がり(垂直同期の後の PLL の乱れ、
///   上端で -8.6°)も一緒に直る。
///
/// 戻り値は (面, 並べ直した量の二乗平均平方根[サンプル])。
fn tbc_plane(src: &[u8], w: usize, h: usize, rows: &[bool], ba: usize, bb: usize,
             step: usize, tbc: bool) -> (Vec<f32>, f32) {
    let mut out = vec![0.0f32; w * h];
    let used = |y: usize| rows.get(y).copied().unwrap_or(false);
    let mut tau = vec![0.0f32; h];
    let mut has = vec![false; h];
    if tbc {
        let mut ph = vec![f32::NAN; h];
        let (mut c2, mut s2) = (0.0f32, 0.0f32);
        for y in 0..h {
            if !used(y) {
                continue;
            }
            let (m, ci, si) = burst(&src[y * w * 2..(y + 1) * w * 2], ba, bb, 0);
            if m <= BURST_MIN {
                continue;
            }
            let p = si.atan2(ci);
            ph[y] = p;
            c2 += (2.0 * p).cos();
            s2 += (2.0 * p).sin();
        }
        let refp = 0.5 * s2.atan2(c2);
        for y in 0..h {
            if ph[y].is_nan() {
                continue;
            }
            // (-90°, 90°] に畳む
            let mut d = ph[y] - refp;
            let half = std::f32::consts::FRAC_PI_2;
            while d > half { d -= std::f32::consts::PI; }
            while d <= -half { d += std::f32::consts::PI; }
            let t = d / std::f32::consts::FRAC_PI_4;
            if t.abs() <= TBC_MAX_SAMPLES {
                tau[y] = t;
                has[y] = true;
            }
        }
    }
    let (mut ss, mut nn) = (0.0f32, 0usize);
    let mut pad: Vec<f32> = Vec::with_capacity(w + 16);
    for y in 0..h {
        if !used(y) {
            continue;
        }
        let row = &src[y * w * 2..(y + 1) * w * 2];
        let o = &mut out[y * w..(y + 1) * w];
        let t = tau[y];
        // ★**行の中でもずれは伸びる**(速度誤差)。取り込みクロックの周波数が
        //   行ごとにわずかに違うので、バーストで揃えた後の残りが行の右へ行くほど
        //   直線的に増えていた(実測: 13.6µs で 0.019 → 57.6µs で 0.069サンプル)。
        //   クロックは行をまたいで連続しているので、**時間的に次の行のバースト**が
        //   この行の終わりのずれを表す。その間を直線で結ぶと右端の残りは 0.043 に
        //   なった(前後4本の3次補間でも 0.041 で、差は小さいので直線にした)。
        //   時間的に次の行 = 同じフィールドの隣 = コム間隔 `step` 先の行。
        let dt = if step > 0 && y + step < h && has[y] && has[y + step] {
            (tau[y + step] - t) / w as f32
        } else {
            0.0
        };
        let nb = (ba + bb) as f32 * 0.5;
        if t == 0.0 && dt == 0.0 {
            for n in 0..w {
                o[n] = row[n * 2] as f32;
            }
            continue;
        }
        ss += t * t;
        nn += 1;
        // Catmull-Rom。線形補間だと副搬送波の振幅がずれ量で変わる
        // (0.5サンプルで 7.6%)ので、行ごとに彩度が揺れてしまう。
        // 端の処理を内側のループから追い出すため、両端を延ばした行を作る
        // (ずれは TBC_MAX_SAMPLES と速度ぶんで高々数サンプル)
        const PAD: usize = 8;
        pad.clear();
        pad.extend(std::iter::repeat(row[0] as f32).take(PAD));
        pad.extend((0..w).map(|n| row[n * 2] as f32));
        pad.extend(std::iter::repeat(row[(w - 1) * 2] as f32).take(PAD));
        let lim = (PAD - 2) as f32;
        for n in 0..w {
            let sh = (t + dt * (n as f32 - nb)).clamp(-lim, lim);
            let x = n as f32 + sh;
            let i = x.floor();
            let f = x - i;
            let i = (i as isize + PAD as isize) as usize;
            let (p0, p1, p2, p3) = (pad[i - 1], pad[i], pad[i + 1], pad[i + 2]);
            o[n] = p1 + 0.5 * f * (p2 - p0
                + f * (2.0 * p0 - 5.0 * p1 + 4.0 * p2 - p3
                + f * (3.0 * (p1 - p2) + p3 - p0)));
        }
    }
    (out, if nn > 0 { (ss / nn as f32).sqrt() } else { 0.0 })
}

/// 赤ch(C)にバーストが載っているか。バースト区間の fsc 相関を、信号の無い
/// バックポーチのそれと比べた比で返す。
///
/// **S端子かコンポジットかを測って決める**ために使う。絶対値で閾値を切ると
/// チャネルのゲイン設定に依存するので、同じチャネルの信号の無い区間を基準にする。
/// 配線と設定が食い違っても絵が出る(コムの間隔やインタレースと同じ方針)。
fn c_burst_snr(raw: &[u8], w: usize, h: usize, filled: &[bool],
               ba: usize, bb: usize, pa: usize, pb: usize) -> f32 {
    let n = (bb - ba).min(pb.saturating_sub(pa));
    if n < 16 {
        return 0.0;
    }
    let (mut bs, mut ps) = (Vec::new(), Vec::new());
    for y in 0..h {
        if !filled.get(y).copied().unwrap_or(false) {
            continue;
        }
        let row = &raw[y * w * 2..(y + 1) * w * 2];
        bs.push(burst(row, ba, ba + n, 1).0);
        ps.push(burst(row, pa, pa + n, 1).0);
    }
    if bs.len() < 8 {
        return 0.0;
    }
    median(&mut bs) / median(&mut ps).max(1e-6)
}

/// `cur` が `prev` に対して横に何サンプルずれているか(cur(n) ≈ prev(n - s) の s)。
///
/// 差を prev の傾きで最小二乗に当てる。ずれが1サンプルより十分小さい前提の
/// 1次近似なので、大きく外れたら(絵が本当に動いたなど)0 として扱う。
fn line_shift(cur: impl Fn(usize) -> f32, prev: impl Fn(usize) -> f32,
              a: usize, b: usize) -> f32 {
    let (mut dg, mut gg) = (0.0f32, 0.0f32);
    for n in a..b {
        let g = (prev(n + 1) - prev(n - 1)) * 0.5;
        dg += (cur(n) - prev(n)) * g;
        gg += g * g;
    }
    if gg < 1e-3 {
        return 0.0;
    }
    let s = -dg / gg;
    if s.abs() > 1.0 { 0.0 } else { s }
}

/// 同期チップとバックポーチの緑chレベル(中央値)を測る。`use_line(y)` が真の
/// 受信済みラインだけを使う。使える行が無ければ None。
fn levels(sample: impl Fn(usize, usize) -> f32, w: usize, h: usize, filled: &[bool],
          sps: f32, use_line: impl Fn(usize) -> bool) -> Option<(f32, f32)> {
    let (ta, tb) = win(TIP_US, sps, w);
    let (pa, pb) = win(PORCH_US, sps, w);
    let mut tips = Vec::new();
    let mut porches = Vec::new();
    for y in 0..h {
        if !filled.get(y).copied().unwrap_or(false) || !use_line(y) {
            continue;
        }
        let mut s = 0.0f32;
        for n in ta..tb {
            s += sample(y, n);
        }
        tips.push(s / (tb - ta).max(1) as f32);
        let mut s = 0.0f32;
        for n in pa..pb {
            s += sample(y, n);
        }
        porches.push(s / (pb - pa).max(1) as f32);
    }
    if tips.is_empty() {
        return None;
    }
    Some((median(&mut tips), median(&mut porches)))
}

/// ガンマは256エントリの表にしておく。画素ごとに powf を3回呼ぶと
/// 28.6 MSa/s では到底間に合わない(1.0 のときは表自体を使わない)。
fn gamma_lut(adj: Adjust) -> Option<[u8; 256]> {
    if (adj.gamma - 1.0).abs() <= 1e-3 {
        return None;
    }
    let inv = 1.0 / adj.gamma.max(0.1);
    let mut t = [0u8; 256];
    for (i, v) in t.iter_mut().enumerate() {
        *v = ((i as f32 / 255.0).powf(inv) * 255.0 + 0.5).clamp(0.0, 255.0) as u8;
    }
    Some(t)
}
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
