kunichiko/RetroCastX/client/src/profiles.rs

//! 映像ソースのプロファイルから pll_divide を決める。
//!
//! pll_divide は「1ラインを何サンプルで取るか」= H-PLLの帰還分周比で、
//! 1サンプル=1ドットにするには入力の水平トータル(htotal)に一致させる必要がある。
//!
//! 絵の内容から探す方法(スペクトル占有率、鮮鋭度の山登り)は、絵が真っ黒だったり
//! 細かい模様が無かったりすると当てにならず、実機でも変な値に着地することが多い。
//!
//! こちらは信号だけで決める。レトロPCのドットクロックは水晶を分周した有限個の値
//! しか取らないので、
//!
//! ```text
//!     htotal = f_dot / fH
//! ```
//!
//! の f_dot に候補を入れて「整数になるもの」を選べばよい。fH は pll_divide に
//! 依存しない絶対値で、MODE が持っている(sysドメインで1秒間エッジを数えた値)。
//!
//! 精度: fH の測定誤差は ±1Hz。htotal への影響は htotal/fH で、31.5kHz・
//! htotal 1104 なら ±0.035カウント。整数を選び分けるには十分すぎる。
//!
//! ## 入力方式の切替も持つ
//!
//! 「映像ソース」は配線の方式(RGB / コンポジット / S端子)でもある。TVPの入力MUX・
//! 同期の取り方・クランプ・ゲインが方式ごとに違うので、選んだときに `input_regs` を
//! そのままボードへ書く。**焼き直しは要らない**(全部 CONFIG で済む)。

use crate::protocol as proto;

/// TVP7002のピクセルクロック下限[Hz]。データシートの保証範囲は12〜165MHz で、
/// 下回るとクランプが効かなくなり画面の下ほど色がずれる(実測: 12.02MHz は正常、
/// 11.25MHz から崩れ、9.72MHz では白の青/赤比が上下で0.43違った)。
const TVP_DOTCLK_MIN: f64 = 12.0e6;
pub const PLL_MIN: i32 = 200;
/// ラインバッファの幅[サンプル](gateware の TvpCapture width)。1ラインが
/// 入り切らないと外接矩形が有効映像の幅を表さなくなるので、実用上限はこちら
/// (gateware の絶対上限 2304 ではない)。
pub const LINE_BUFFER_W: i32 = 2048;

/// 映像ソースを選んだときにボードへ書く TVP のレジスタ設定。
///
/// `host/python/retrocastx/videoin.py` の MODES の移植。**あちらが仕様の正**で、
/// 値の根拠(なぜミッドレベルクランプなのか、なぜ粗ゲインを一緒に下げるのか等)は
/// あちらのコメントと docs/composite-video-plan.md にある。
///
/// ★**どのモードも同じキー集合を書く。** 書かないキーがあると、方式を切り替えた
///   ときに前の方式の値が残る。Python側で実際にやらかしていて(RGB系で pll_divide を
///   省いていて composite → x68k で 1820 が残った)、回帰試験で見つかった。
///   ここでも `all_modes_write_the_same_keys` で担保する。
pub type InputRegs = &'static [(u16, u32, &'static str)];

/// 実機の水晶ひとつと、**その水晶で実在する分周比**。
///
/// 分周比を水晶ごとに持つのが要点。機種の中でも系統によって使える分周比が違い、
/// 共通のリストにすると実在しないドットクロックが候補に混ざる。X68000がまさに
/// そうで、69.552MHz側は /2,3,4,6,8 が全部使われるのに 38.864MHz側は /4,8 しか
/// 無い。共通リストにすると 38.864/2 = 19.432MHz という存在しない値が生まれ、
/// 他機種の fH に誤マッチする余地を作ってしまう。
pub struct Clock {
    pub name: &'static str,
    pub hz: f64,
    pub dividers: &'static [i32],
}

pub struct Profile {
    /// 設定ファイルに書く名前
    pub key: &'static str,
    pub label: &'static str,
    /// この映像ソースを選んだときにボードへ書く TVP レジスタ。
    /// 空なら pll_divide の推定に使うだけで、ボードには何も書かない。
    pub input_regs: InputRegs,
    /// 「自動」(プロファイル未選択)のときの候補に入れるか。
    ///
    /// コンポジット/S端子を入れてはいけない。8fsc(28.636MHz)は fH 31.5kHz でも
    /// htotal 909.1 という「それらしい」候補を出すので、RGB機の自動選択を横取りする。
    pub auto_pick: bool,
    /// 実機の水晶と分周比。モードごとのドットクロックを列挙するより漏れにくい。
    ///
    /// **ここが「簡易スキャン」の探索空間そのもの**でもある。fH と突き合わせて
    /// 整数の htotal になる組だけが候補になるので、機種を足すときはこの表だけを
    /// 正確に書けば、探索側は何も変えなくてよい。
    pub oscillators: &'static [Clock],
    /// htotal の粒度。X68000のCRTCは水平トータルを8ドット単位で持つので、
    /// 正解は必ず8の倍数になる。この制約が候補をさらに絞る
    pub htotal_multiple: i32,
    /// この映像入力と組になる音声入力(0=RGB端子 / 1=LINE / 2=S/PDIF)。
    ///
    /// ★**基板の音声入力は3系統しかなく、どれと組になるかは配線で決まっている。**
    ///   RGB端子(J10)は X68000 式の2列DA-15 で、ピン10/11 に音声が来る。だから
    ///   X68000 だけが 0 で、それ以外は音声が別配線になるので LINE 入力(1)。
    ///   S/PDIF は「その機種はこれ」と言えるものではないので既定にはしない。
    ///
    ///   これは**既定であって固定ではない**。音声を「自動」にしているときだけ
    ///   参照され、ユーザーが明示的に選べばそちらが優先される。
    pub audio_src: Option<u8>,
    /// 実機で裏を取れているか。**自動選択の順位付けに使う。**
    ///
    /// 水晶が違っても fH ひとつからは同じくらいよく合う候補が出ることがある。
    /// 実際 MSX の fH 15.699kHz に対し、未検証の pc98(21.0525MHz)が
    /// htotal 1341(相対誤差 6.7e-6)で、正解の msx(342、相対誤差 4.8e-5)より
    /// 良く見えてしまう。残差の閾値を通っている時点でどちらも「信号を説明できる」
    /// ので、そこから先は推測の水晶より実測済みの水晶を優先する。
    pub verified: bool,
}
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
